impatrq/aeroalert/AES-CTRT-VDB_programs/pc-simulador/imagenes_GUI/llave2.png

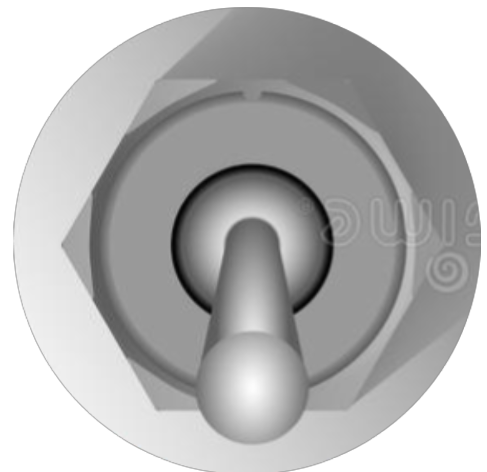
AES-CTRT-VDB_programs/pc-simulador/imagenes_GUI/llave2.png
