impatrq/aeroalert/AES-CTRT-VDB_programs/pc-simulador/imagenes_GUI/llave.png

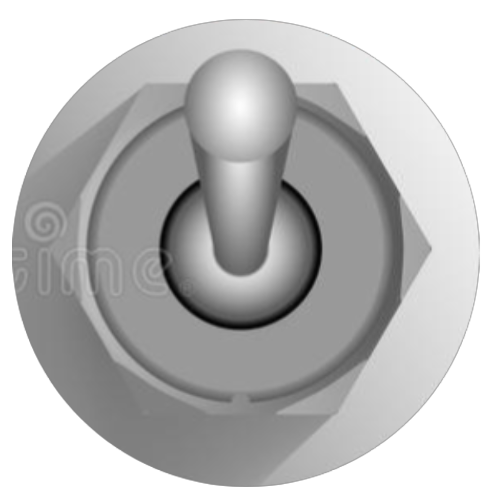
AES-CTRT-VDB_programs/pc-simulador/imagenes_GUI/llave.png
