impatrq/aeroalert/CAD/AES/AES - Exploded View.png

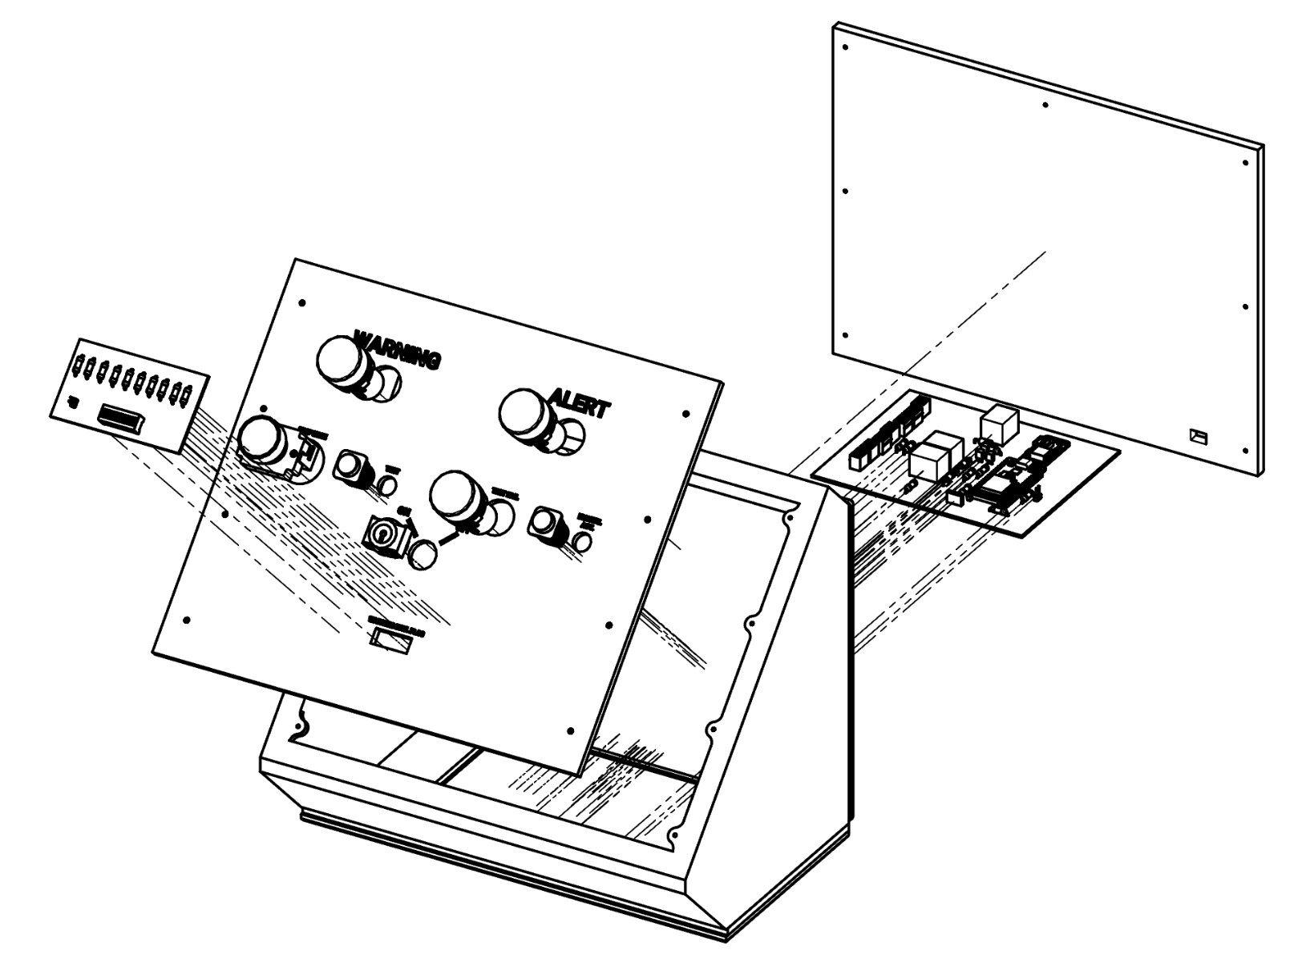
CAD/AES/AES - Exploded View.png
