impatrq/aeroalert/CAD/AES/Electrical/PCB/AES Blueprint.png

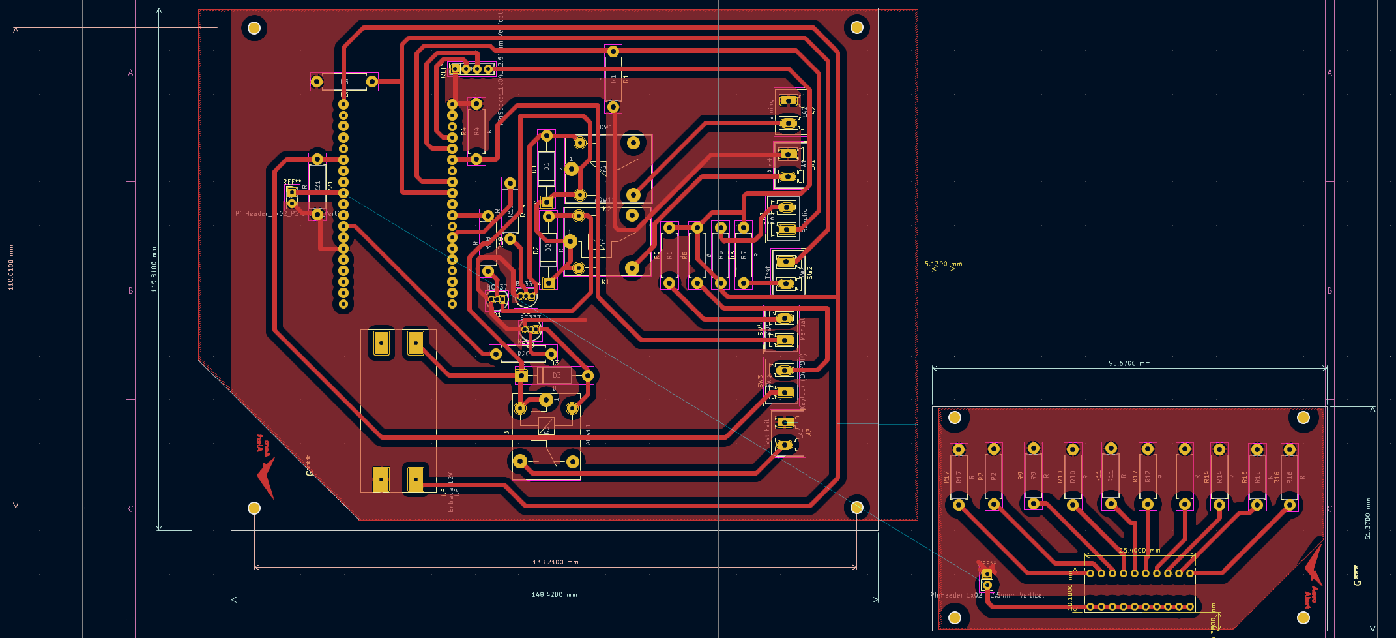
CAD/AES/Electrical/PCB/AES Blueprint.png
