impatrq/aeroalert/CAD/CTRT/CTRT - Exploded View.png

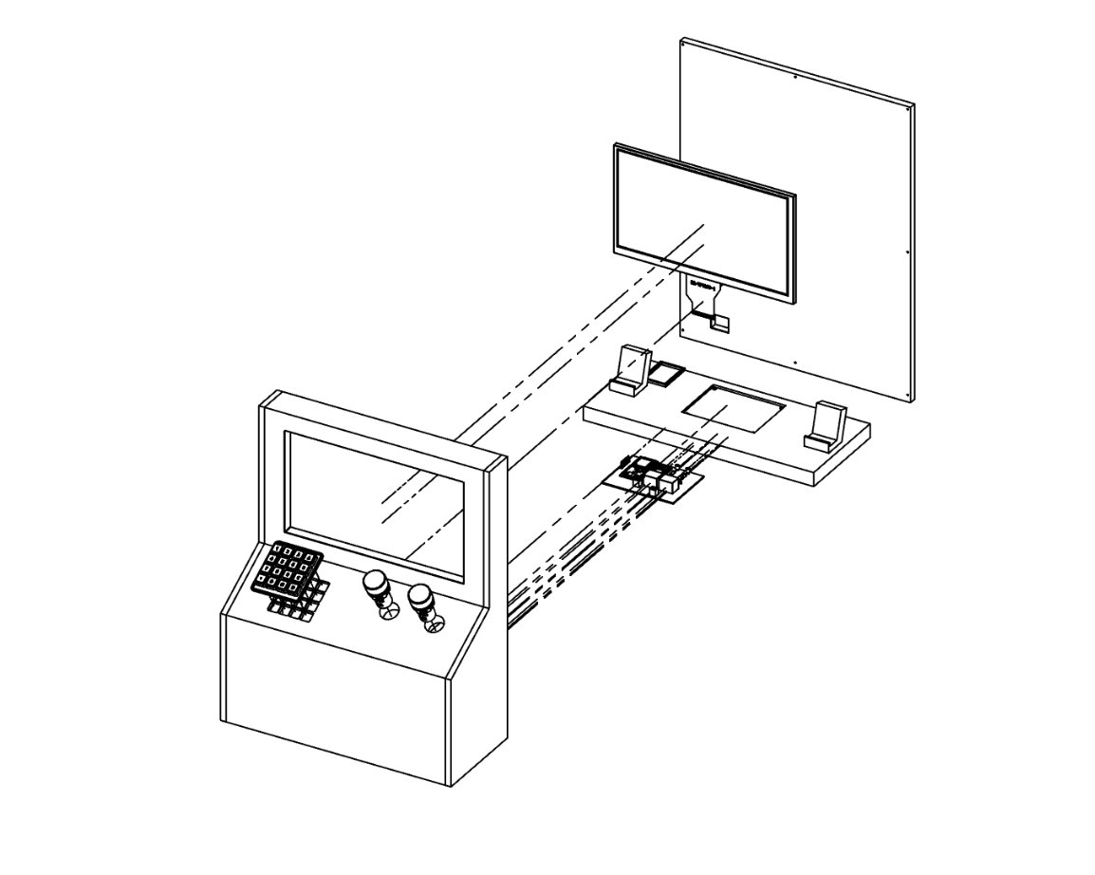
CAD/CTRT/CTRT - Exploded View.png
