impatrq/aeroalert/CAD/CTRT/Electrical/PCB/CTRT Blueprint.png

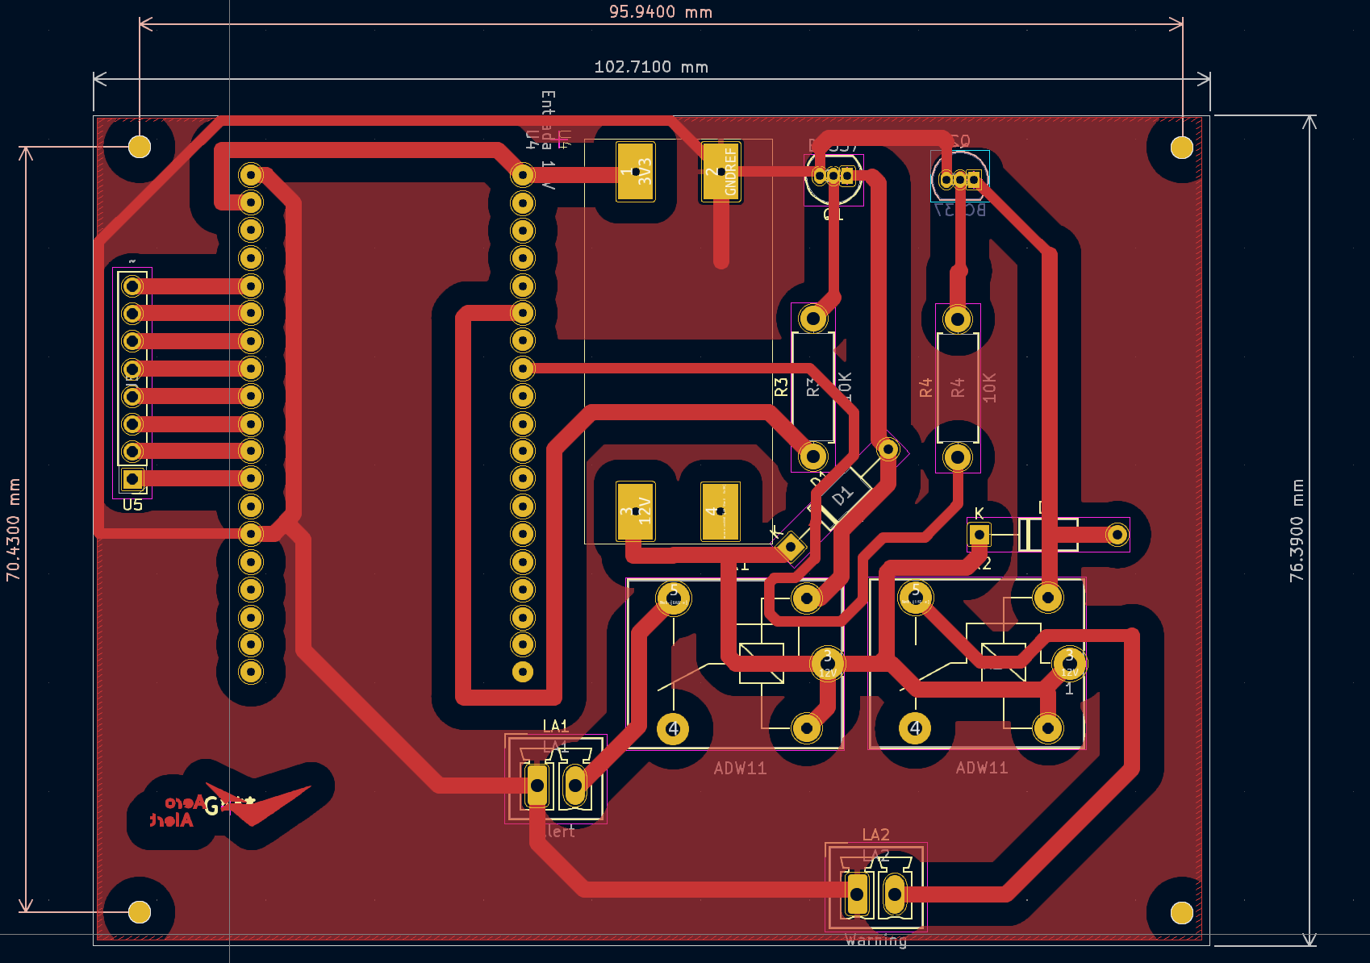
CAD/CTRT/Electrical/PCB/CTRT Blueprint.png
