impatrq/aeroalert/CAD/STEP Templates/Rendering/Pinout.jpg

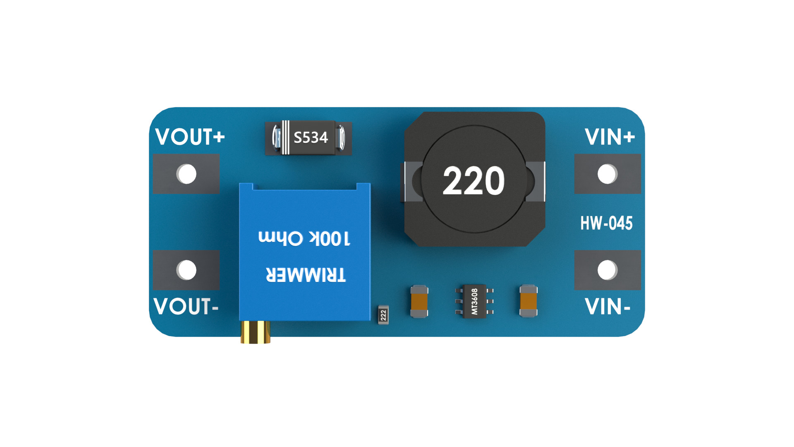
CAD/STEP Templates/Rendering/Pinout.jpg
