impatrq/aeroalert/CAD/VDB/Electrical/PCB/VDB Blueprint.png

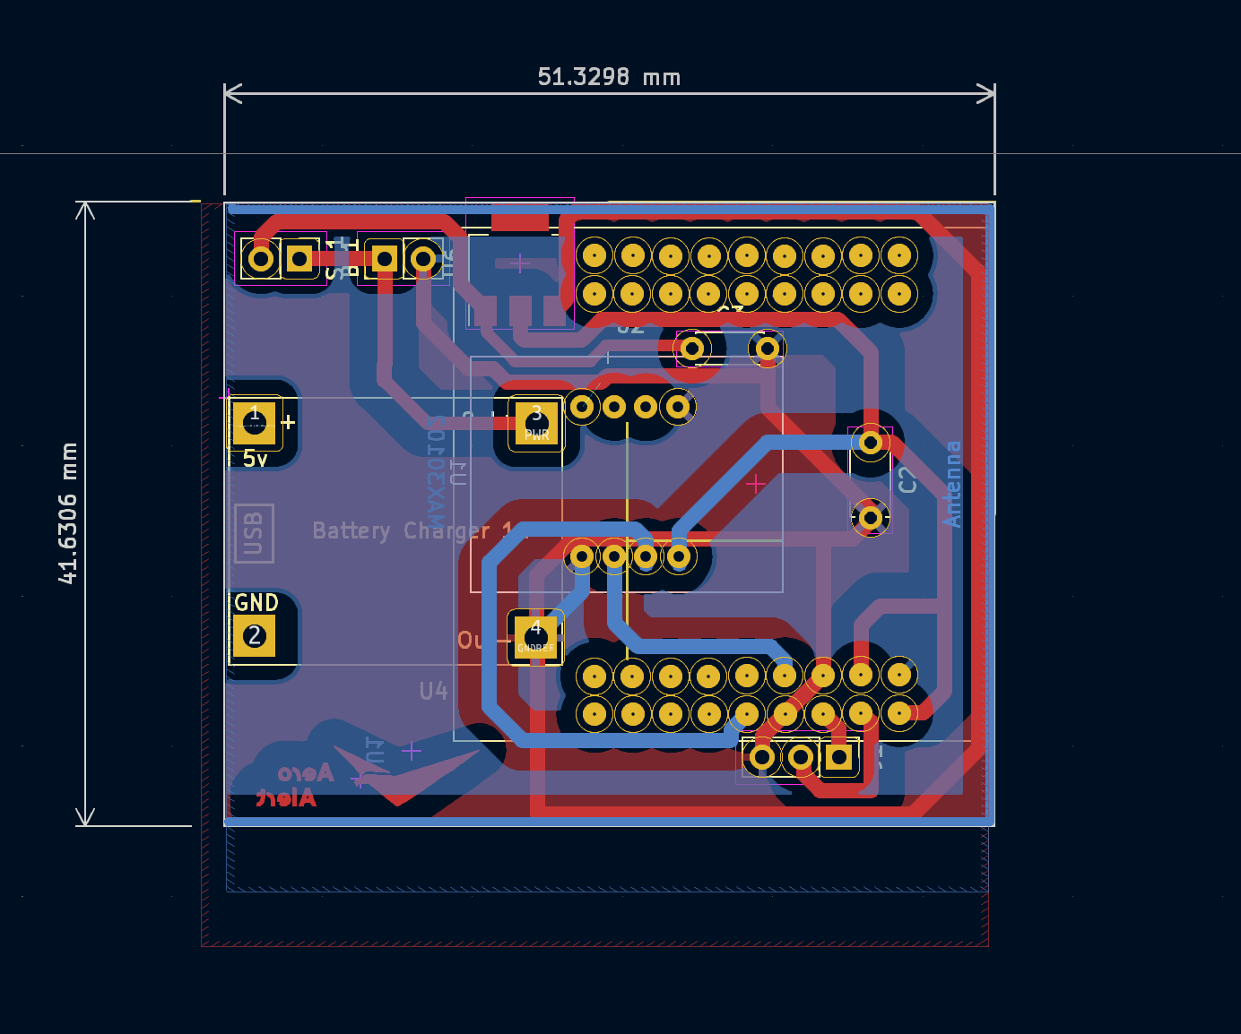
CAD/VDB/Electrical/PCB/VDB Blueprint.png
