impatrq/aeroalert/CAD/VDB/VDB - Exploded View.png

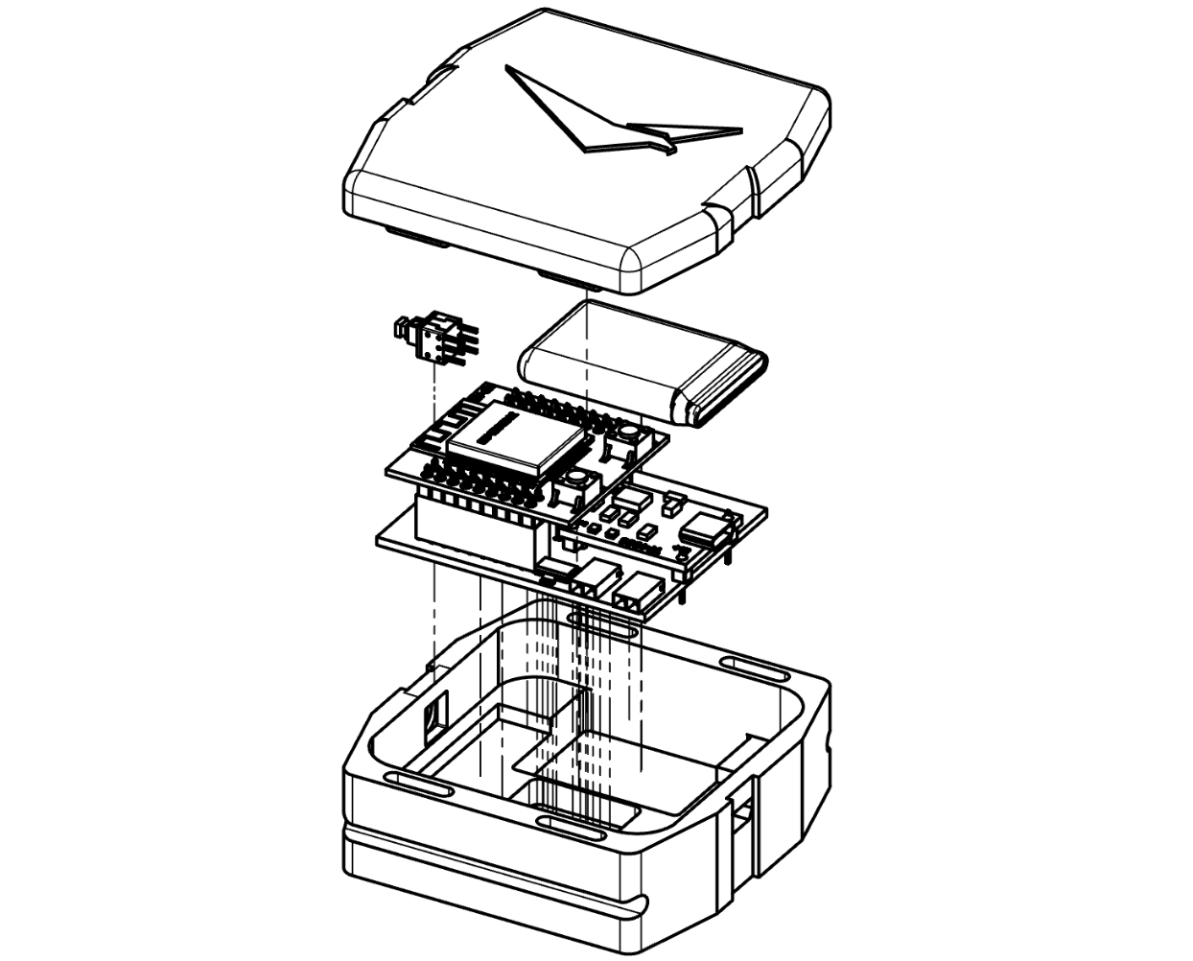
CAD/VDB/VDB - Exploded View.png
