impatrq/aeroalert/Diseños de marca/Destacadas/Nosotros AeroAlert.png

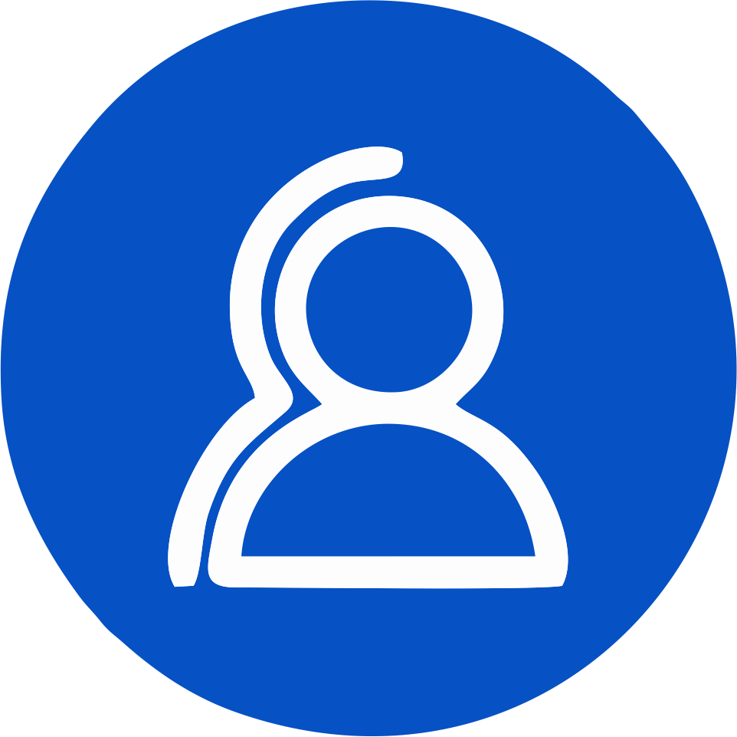
Diseños de marca/Destacadas/Nosotros AeroAlert.png
