impatrq/aeroalert/Diseños de marca/Destacadas/ONIET 2023.png

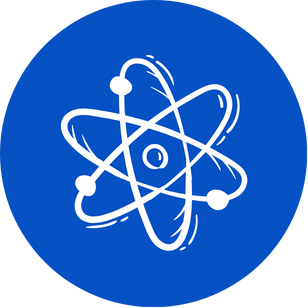
Diseños de marca/Destacadas/ONIET 2023.png
