impatrq/aeroalert/Diseños de marca/Destacadas/Progreso AeroAlert.png

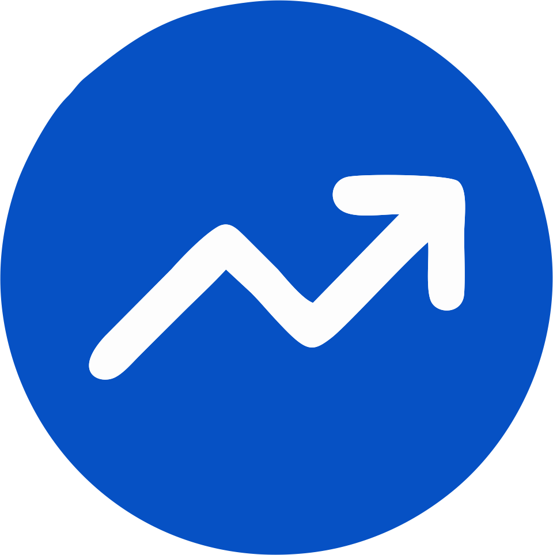
Diseños de marca/Destacadas/Progreso AeroAlert.png
