impatrq/aeroalert/Diseños de marca/Exposición/QR de Difusión.png

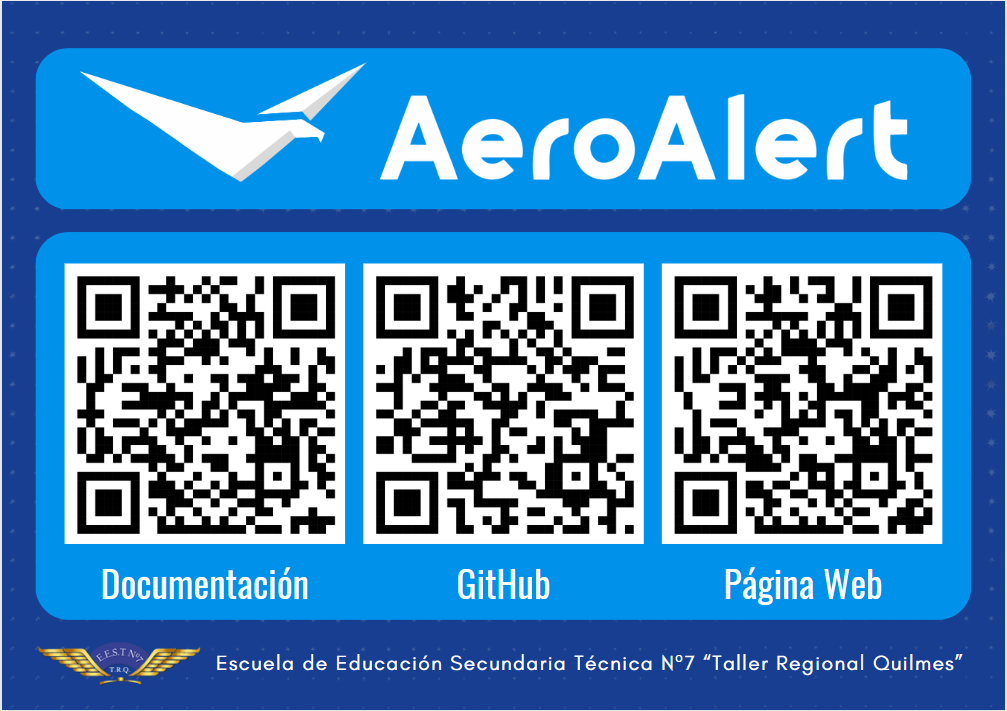
Diseños de marca/Exposición/QR de Difusión.png
