impatrq/aeroalert/Diseños de marca/Letras/Letras AeroAlert.png

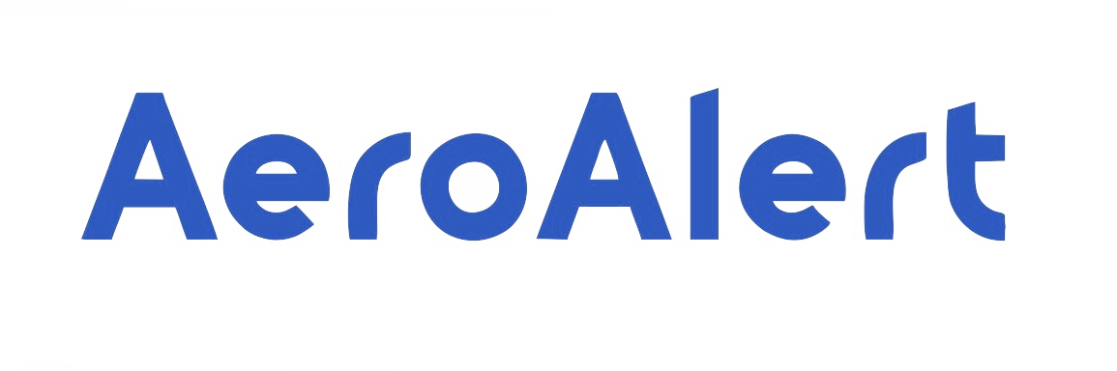
Diseños de marca/Letras/Letras AeroAlert.png
