impatrq/aeroalert/Diseños de marca/Recursos adicionales/inicio-avio.png

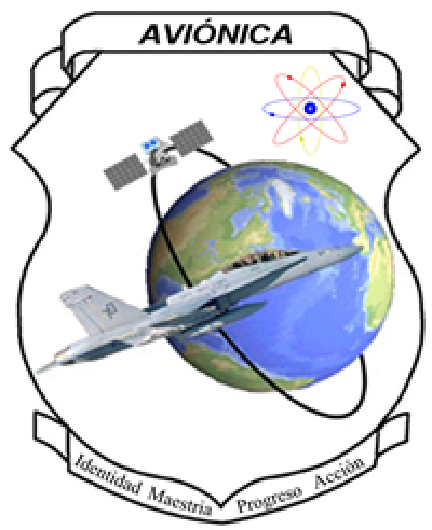
Diseños de marca/Recursos adicionales/inicio-avio.png
