impatrq/aeroalert/Pagina Web/CV Personales/CV Teo Lopez.jpeg

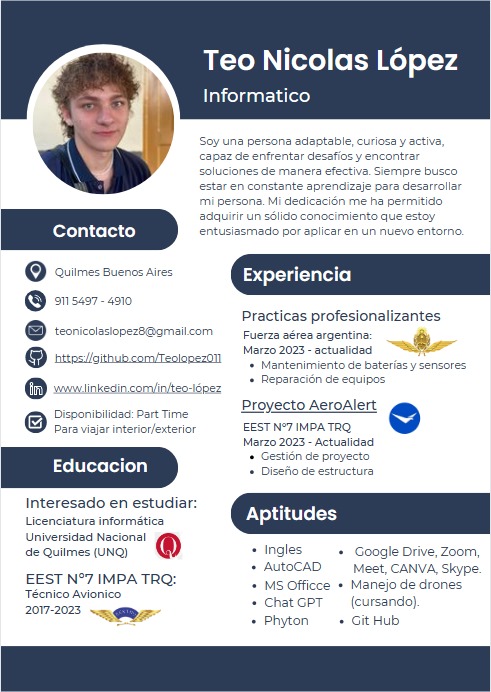
Pagina Web/CV Personales/CV Teo Lopez.jpeg
