impatrq/aeroalert/Pagina Web/imgs/Captura desde 2023-05-15 09-19-19.png

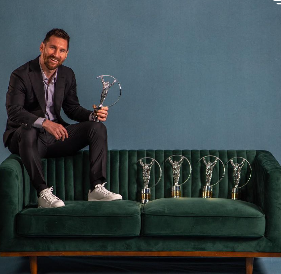
Pagina Web/imgs/Captura desde 2023-05-15 09-19-19.png
