impatrq/aeroalert/Pagina Web/imgs/Captura ESP32.png

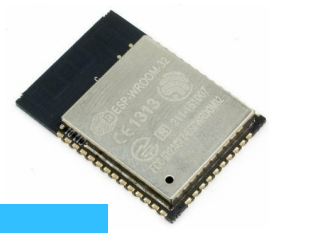
Pagina Web/imgs/Captura ESP32.png
