impatrq/aeroalert/Pagina Web/imgs/Captura Helios.png

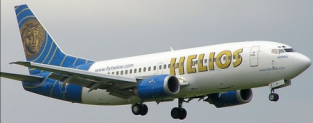
Pagina Web/imgs/Captura Helios.png
