impatrq/aeroalert/Pagina Web/imgs/Captura Pilotos zzzz.png

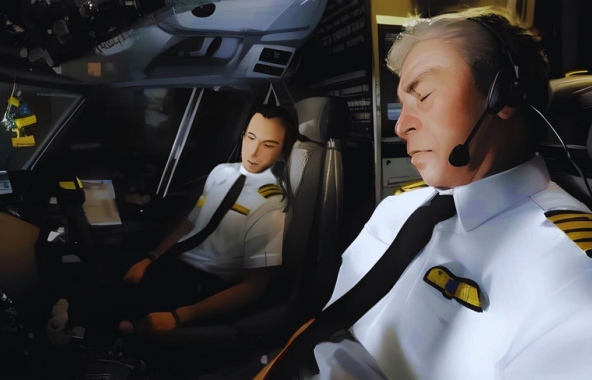
Pagina Web/imgs/Captura Pilotos zzzz.png
