impatrq/aeroalert/Pagina Web/imgs/Contacto.jpeg

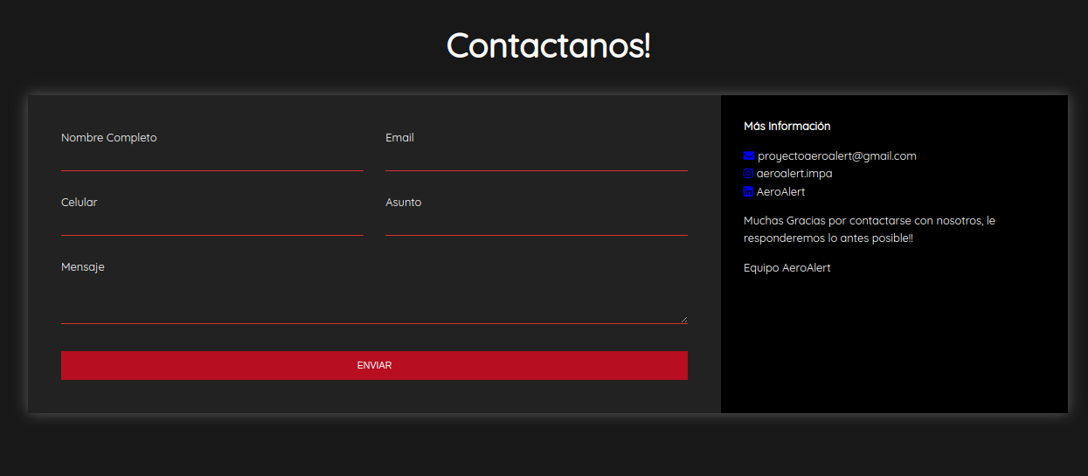
Pagina Web/imgs/Contacto.jpeg
