impatrq/aeroalert/Pagina Web/imgs/descarga.jpg

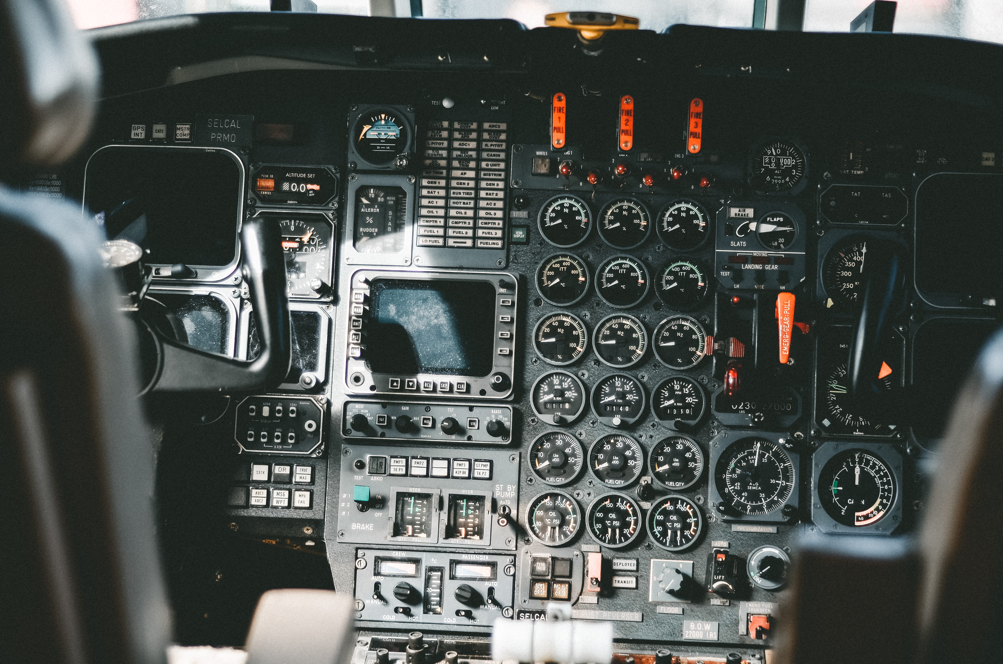
Pagina Web/imgs/descarga.jpg
