impatrq/aeroalert/Pagina Web/imgs/foto de los pibes.jpeg

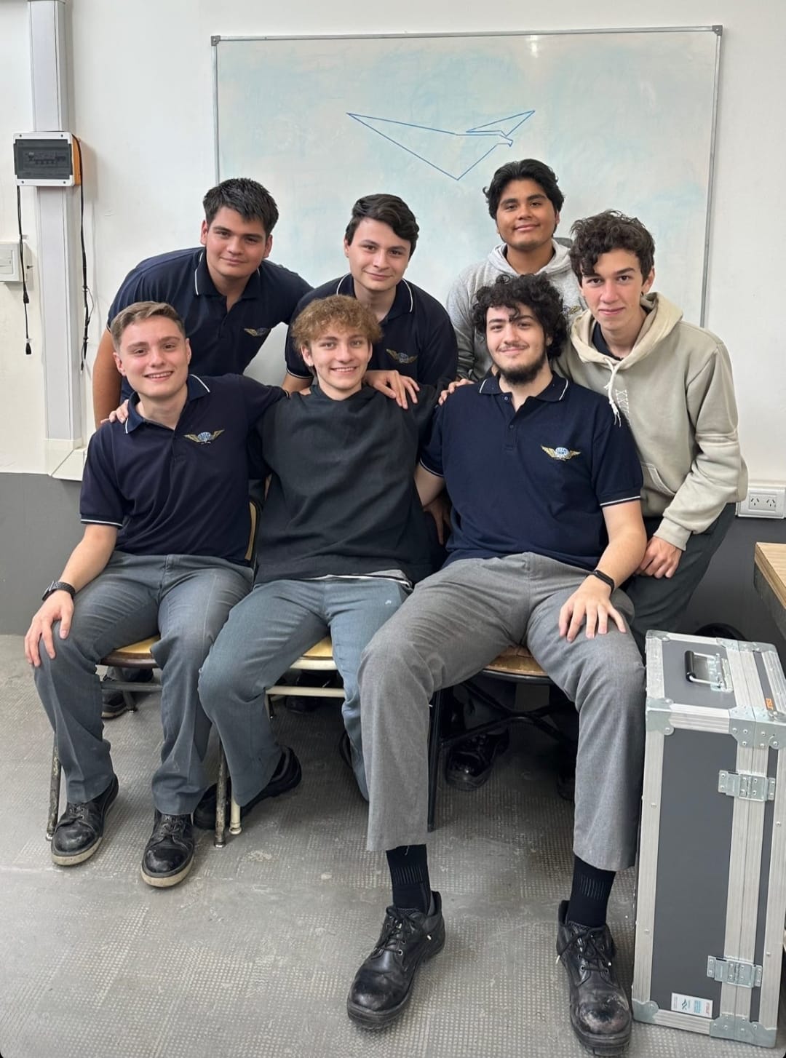
Pagina Web/imgs/foto de los pibes.jpeg
