impatrq/aeroalert/Pagina Web/imgs/husu 2 foto.jpeg

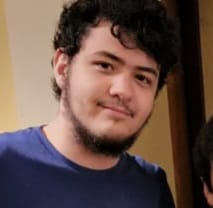
Pagina Web/imgs/husu 2 foto.jpeg
