impatrq/aeroalert/Pagina Web/imgs/Husu foto.jpeg

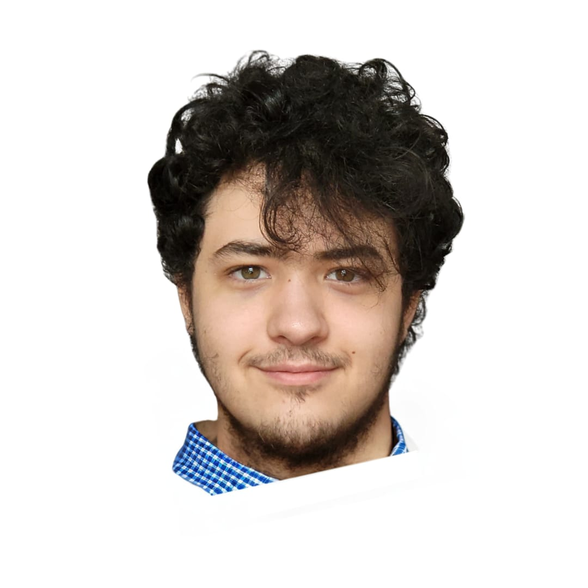
Pagina Web/imgs/Husu foto.jpeg
