impatrq/aeroalert/Pagina Web/imgs/Jonas foto.png

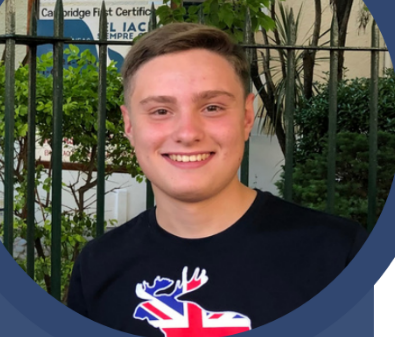
Pagina Web/imgs/Jonas foto.png
