impatrq/aeroalert/Pagina Web/imgs/juan foto.jpeg

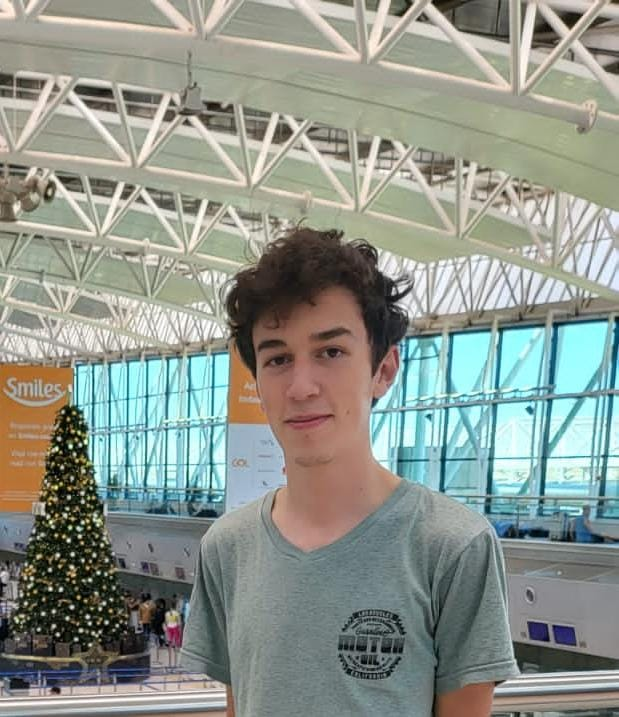
Pagina Web/imgs/juan foto.jpeg
