impatrq/aeroalert/Pagina Web/imgs/Mauro Foto 2.jpeg.png

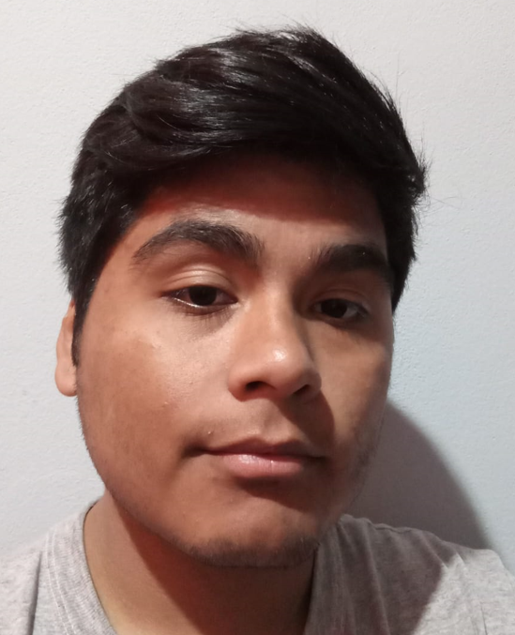
Pagina Web/imgs/Mauro Foto 2.jpeg.png
