impatrq/aeroalert/Pagina Web/imgs/Mauro Foto.jpeg

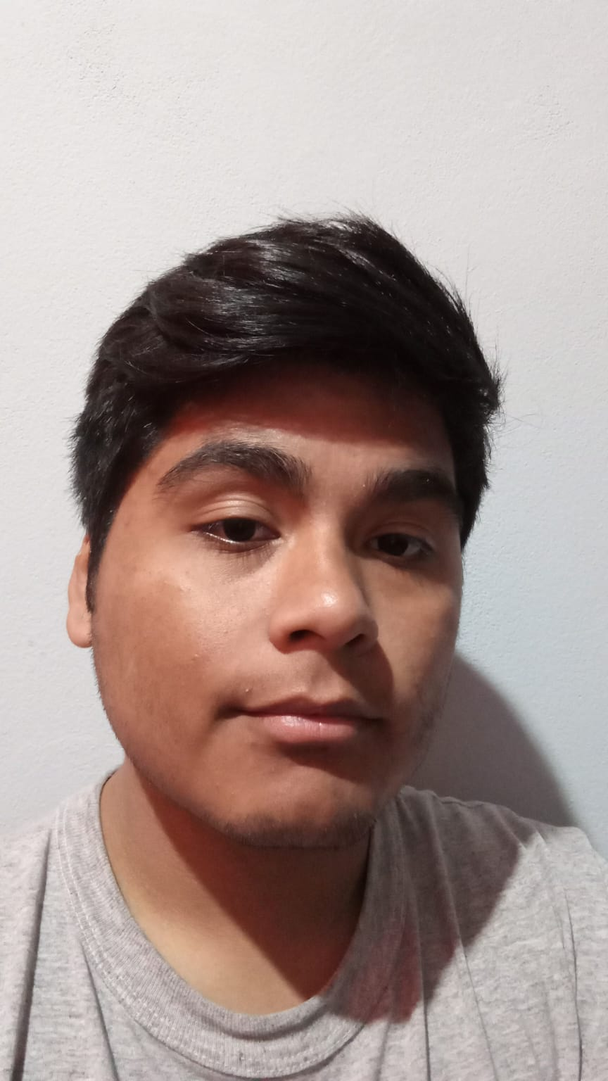
Pagina Web/imgs/Mauro Foto.jpeg
