impatrq/aeroalert/Pagina Web/imgs/Mi proyecto Azul.jpeg

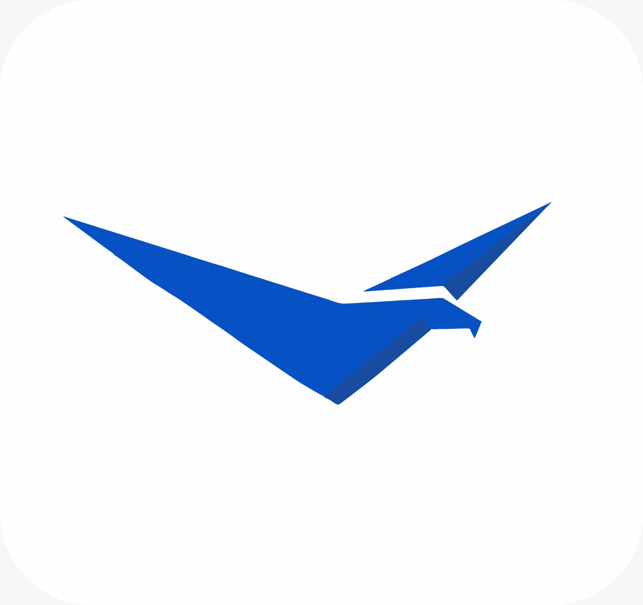
Pagina Web/imgs/Mi proyecto Azul.jpeg
