impatrq/aeroalert/Pagina Web/imgs/Mi proyecto.png

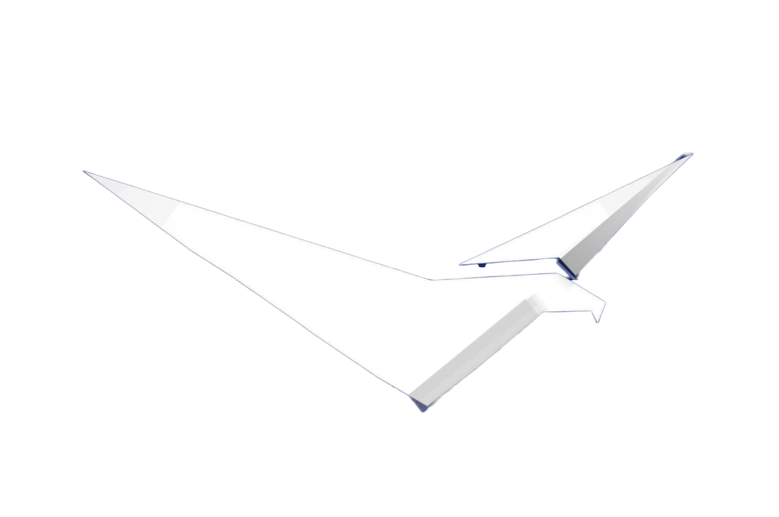
Pagina Web/imgs/Mi proyecto.png
