impatrq/aeroalert/Pagina Web/imgs/nicolas foto.jpeg

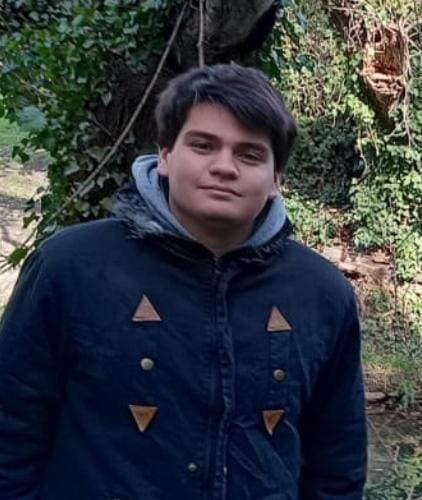
Pagina Web/imgs/nicolas foto.jpeg
