impatrq/aeroalert/Pagina Web/imgs/Programacion.jpg

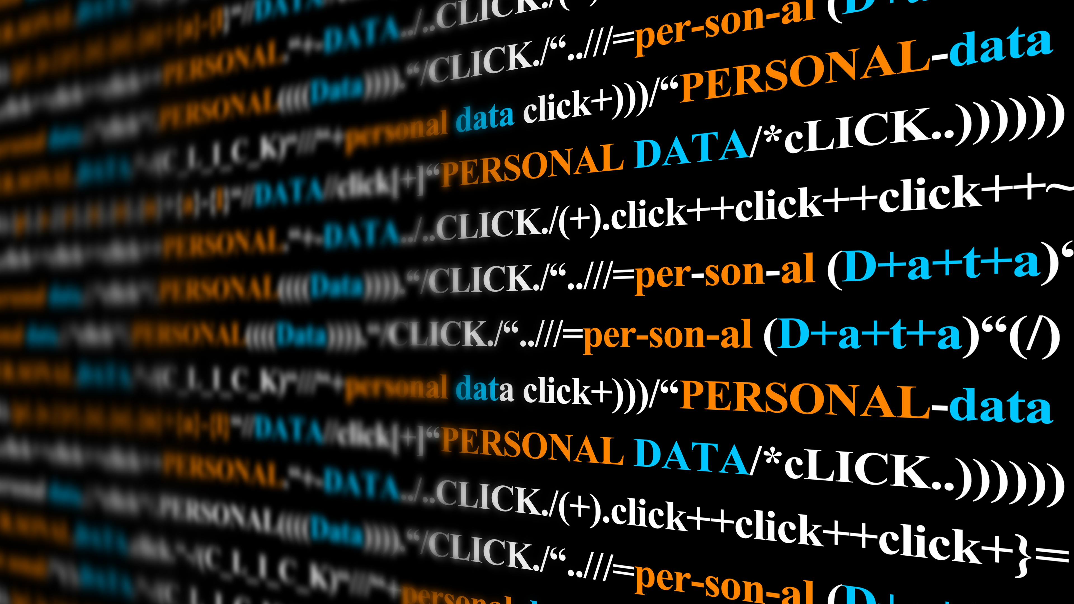
Pagina Web/imgs/Programacion.jpg
