impatrq/aeroalert/Pagina Web/imgs/Teo2.png

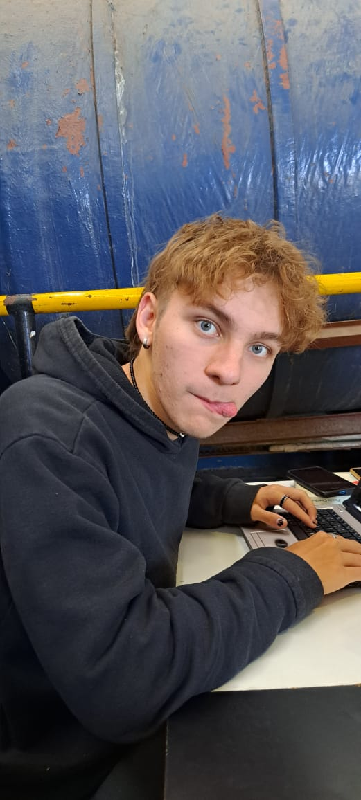
Pagina Web/imgs/Teo2.png
