impatrq/aeroalert/Pagina Web/imgs/Teo Lopez Foto.jpeg

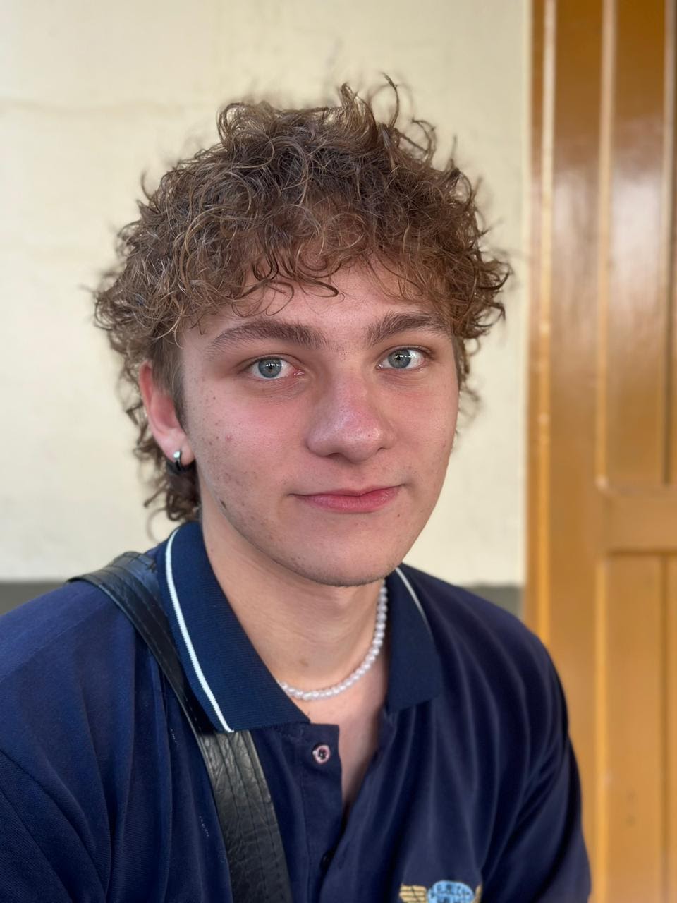
Pagina Web/imgs/Teo Lopez Foto.jpeg
