impatrq/aeroalert/Pagina Web/imgs/Teo.jpeg

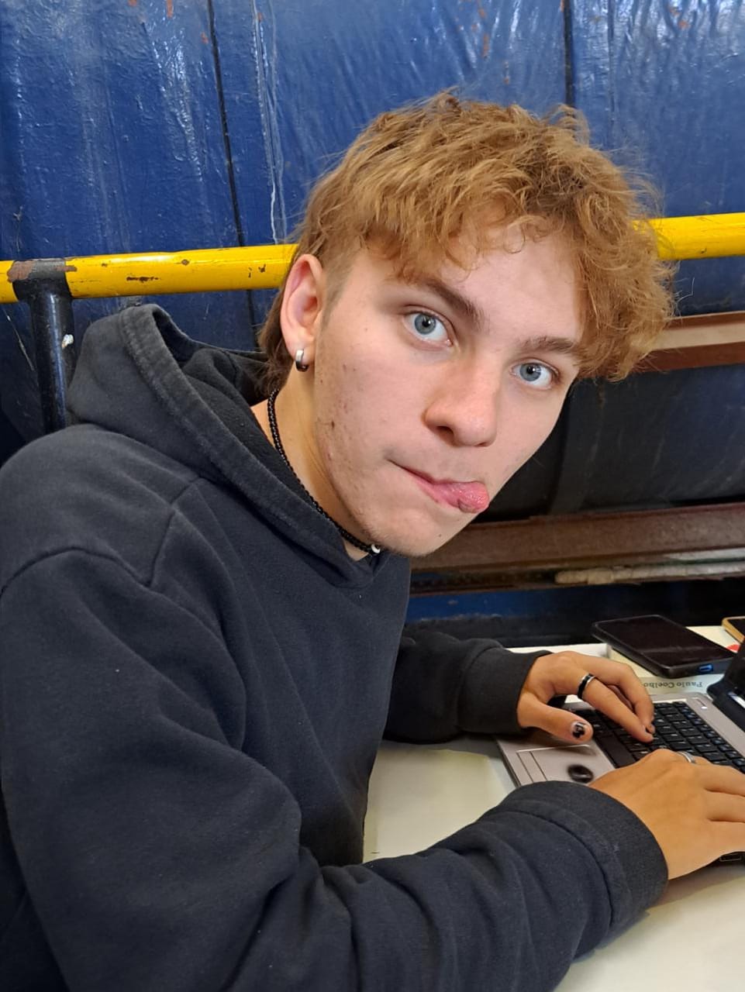
Pagina Web/imgs/Teo.jpeg
