impatrq/aeroalert/CAD/CNC Routing/CTRT/Part 3/Part Studio 1 - Part 3.dxf

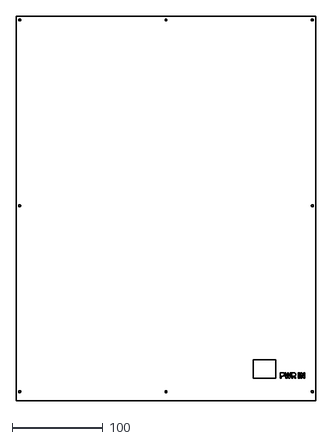
[picture p121: CAD file, 2023-11-29]
CAD/CNC Routing/CTRT/Part 3/Part Studio 1 - Part 3.dxf
330.0 x 423.0
