impatrq/aeroalert/CAD/CNC Routing/Plancha 120 x 80 cm.dxf

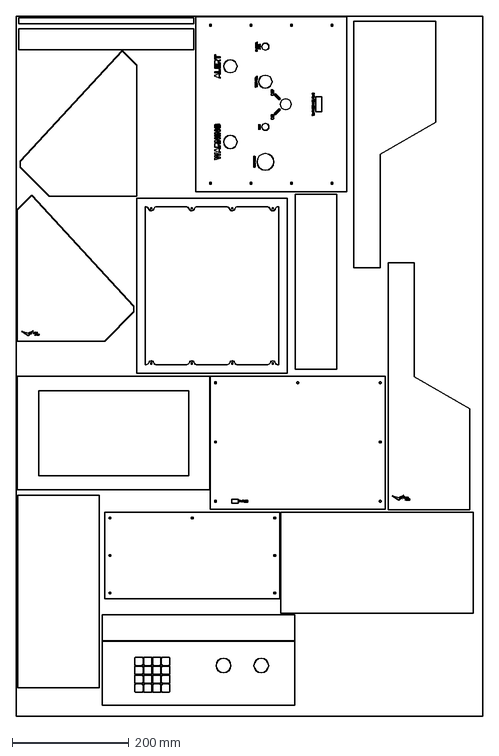
[picture p122: CAD file, 2023-11-29]
CAD/CNC Routing/Plancha 120 x 80 cm.dxf
800.0 x 1200.0 mm
