impatrq/aeroalert/CAD/CTRT/CTRT - Keycaps.stl

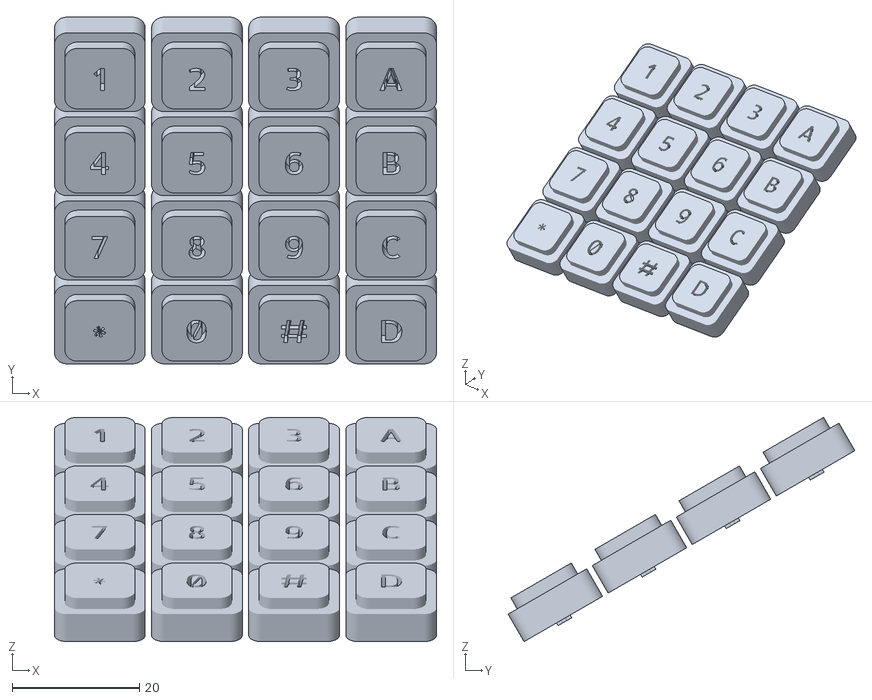
[picture p123: CAD file, 2023-11-15]
CAD/CTRT/CTRT - Keycaps.stl
60.1 x 54.6 x 35.3
