impatrq/aeroalert/CAD/STEP Templates/10-segment-linear-display-1/Display_10SegBlue.SLDPRT

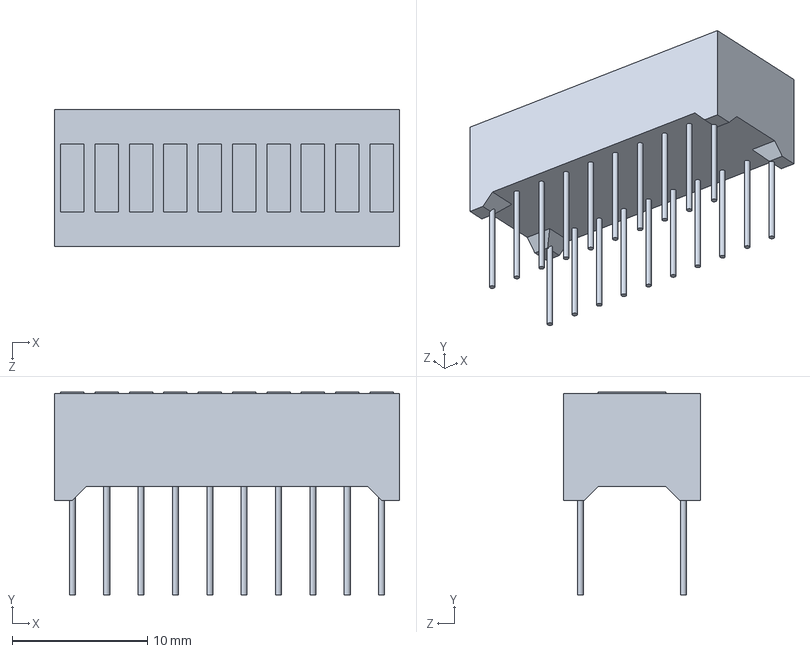
[picture p124: CAD file, 2023-11-28]
CAD/STEP Templates/10-segment-linear-display-1/Display_10SegBlue.SLDPRT
25.5 x 15.0 x 10.1 mm
