impatrq/aeroalert/CAD/STEP Templates/emergency-stop-12/PushButton27mm.STEP

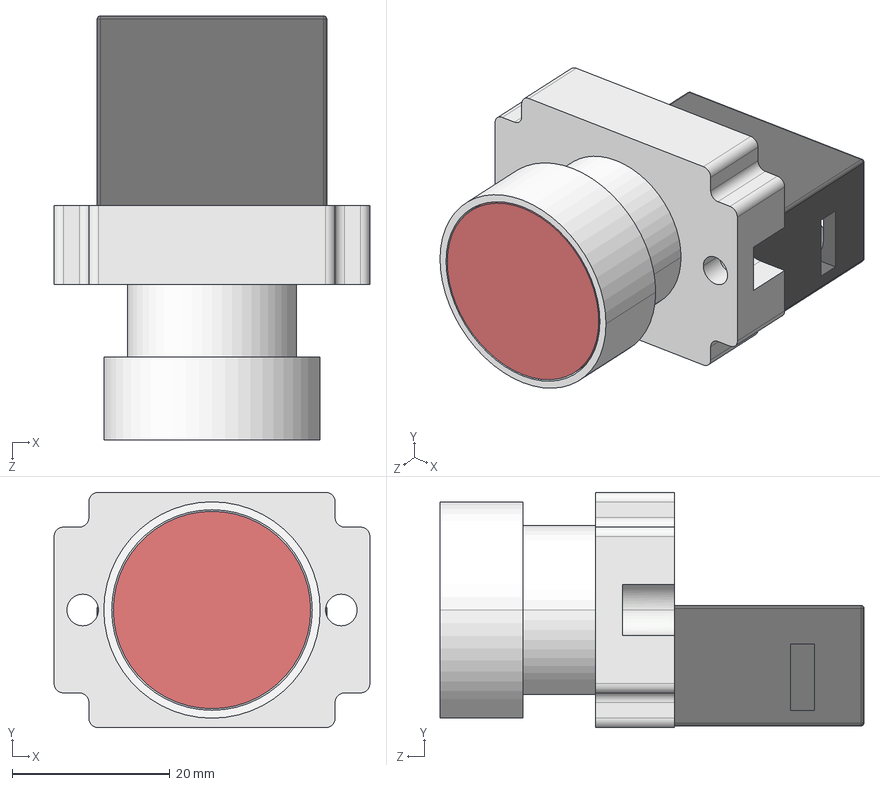
[picture p126: CAD file, 2023-11-28]
CAD/STEP Templates/emergency-stop-12/PushButton27mm.STEP
40.0 x 29.8 x 53.7 mm
