impatrq/aeroalert/CAD/STEP Templates/keyboard-4x4-1/TEC-MA-4X4.STEP

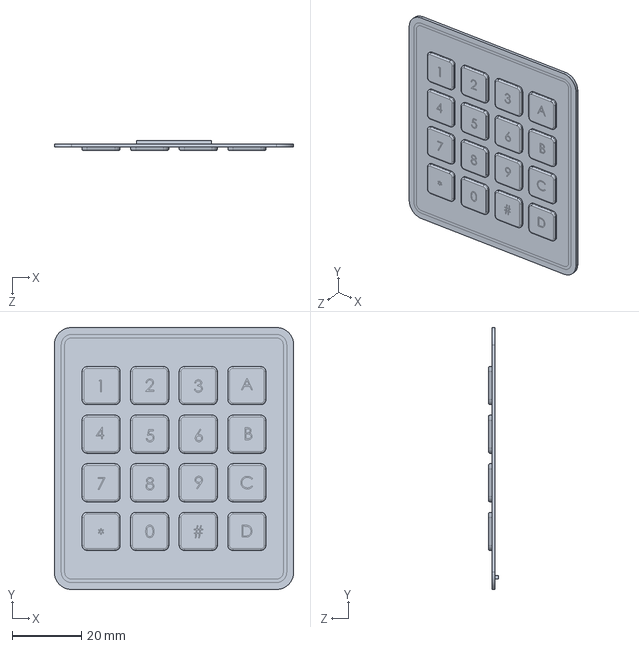
[picture p127: CAD file, 2023-11-28]
CAD/STEP Templates/keyboard-4x4-1/TEC-MA-4X4.STEP
69.0 x 75.5 x 3.00 mm
