impatrq/aeroalert/CAD/STEP Templates/keylock-switch-adp16k4-1/KeySwitch16_Part2.SLDPRT

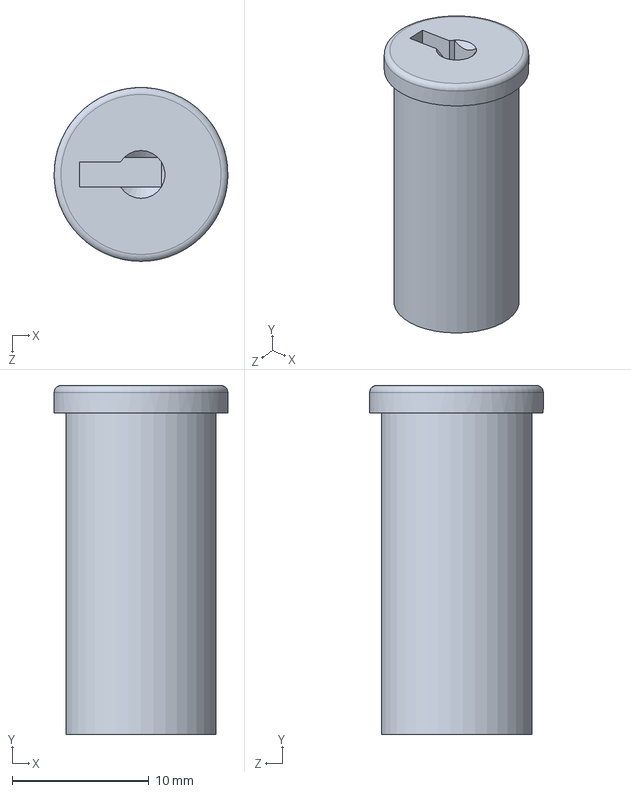
[picture p128: CAD file, 2023-11-28]
CAD/STEP Templates/keylock-switch-adp16k4-1/KeySwitch16_Part2.SLDPRT
12.7 x 25.5 x 12.7 mm
