impatrq/aeroalert/CAD/STEP Templates/led-pushbutton-1/LED Pushbutton.step

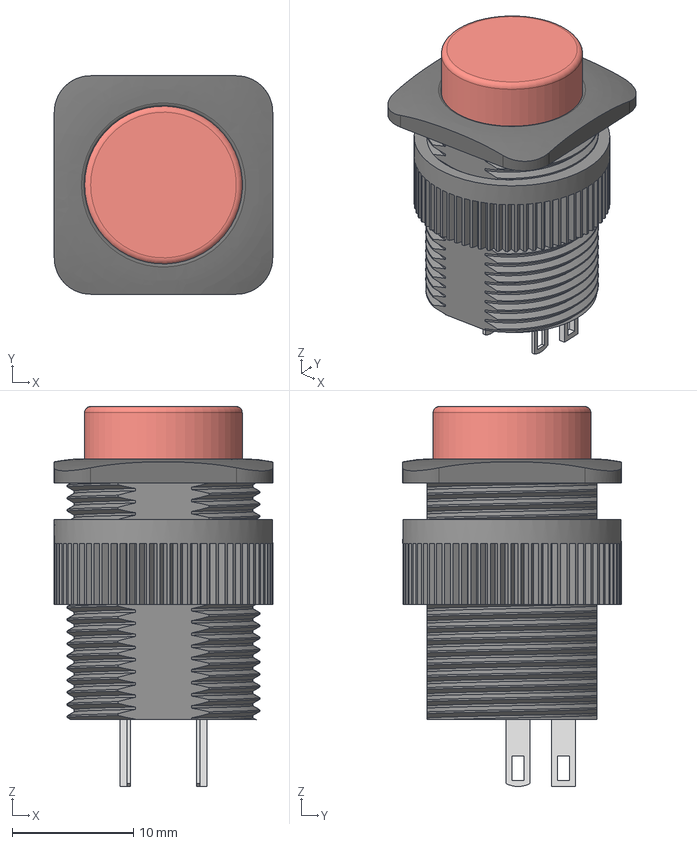
[picture p129: CAD file, 2023-11-28]
CAD/STEP Templates/led-pushbutton-1/LED Pushbutton.step
18.0 x 18.0 x 31.3 mm
Top
Bezel
Barrel
Lock Nut
Lug
Lug 2
Lug(Mirror)
Lug 2(Mirror)
