impatrq/aeroalert/CAD/STEP Templates/mini-toggle-switches-1/6mm DPDT Mini Toggle Switch.step

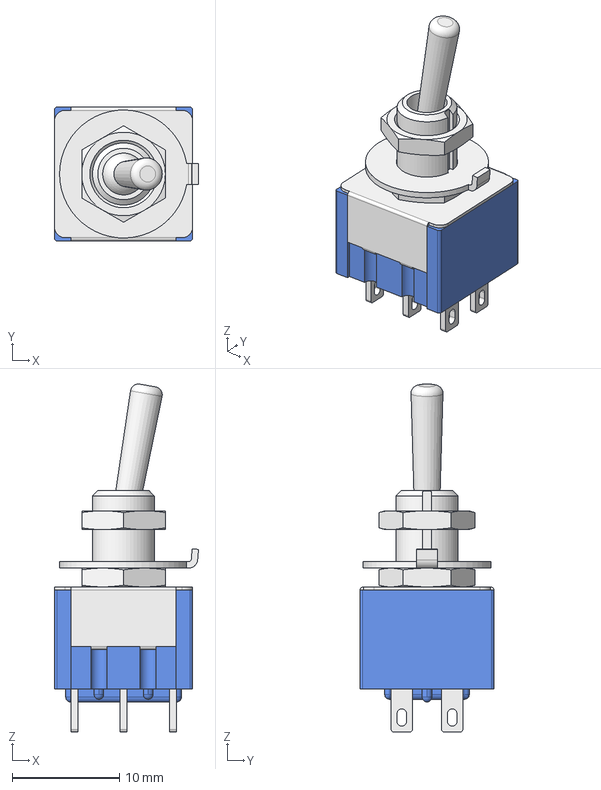
[picture p130: CAD file, 2023-11-28]
CAD/STEP Templates/mini-toggle-switches-1/6mm DPDT Mini Toggle Switch.step
13.4 x 12.5 x 32.5 mm
