impatrq/aeroalert/CAD/STEP Templates/mini-toggle-switches-1/FreeCAD Files/Set.FCStd

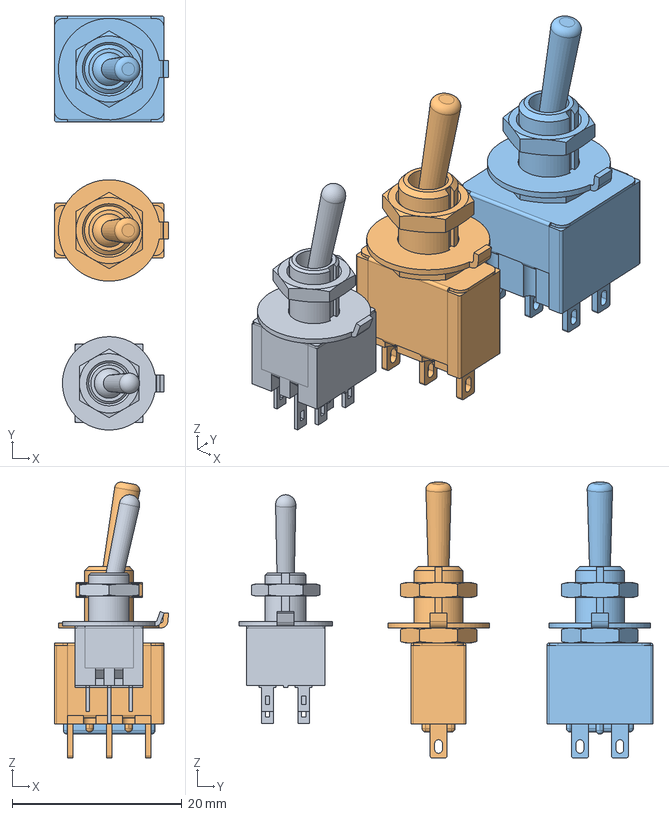
[picture p131: CAD file, 2023-11-28]
CAD/STEP Templates/mini-toggle-switches-1/FreeCAD Files/Set.FCStd
13.4 x 48.7 x 32.5 mm
5mm DPDT Mini Toggle Switch_001
6mm SPDT Mini Toggle Switch_001
6mm DPDT Mini Toggle Switch_001
