impatrq/aeroalert/CAD/STEP Templates/panel-light-indicator-_-red-1/PANEL LIGHT_RED.step

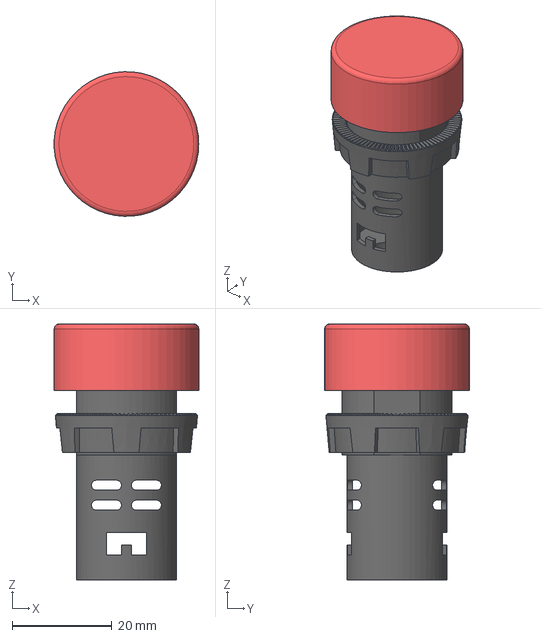
[picture p132: CAD file, 2023-11-28]
CAD/STEP Templates/panel-light-indicator-_-red-1/PANEL LIGHT_RED.step
29.0 x 29.0 x 51.3 mm
