impatrq/aeroalert/CAD/VDB/VDB - Top Cover.stl

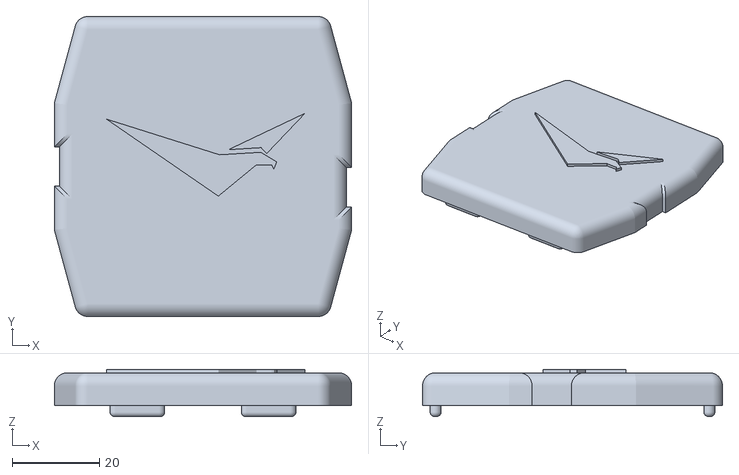
[picture p134: CAD file, 2023-11-15]
CAD/VDB/VDB - Top Cover.stl
68.0 x 68.6 x 10.8
