impatrq/aeroalert/CAD/CNC Routing/CTRT/Part 1/Part Studio 1 - Part 1-2.dxf

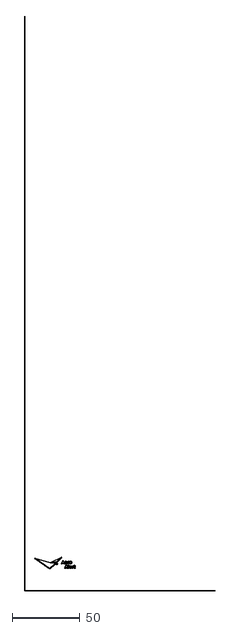
[picture p135: CAD file, 2023-11-29]
CAD/CNC Routing/CTRT/Part 1/Part Studio 1 - Part 1-2.dxf
140.0 x 423.0
