impatrq/aeroalert/CAD/STEP Templates/keylock-switch-adp16k4-1/Key Switch ADP16K4-ATO-1A.STEP

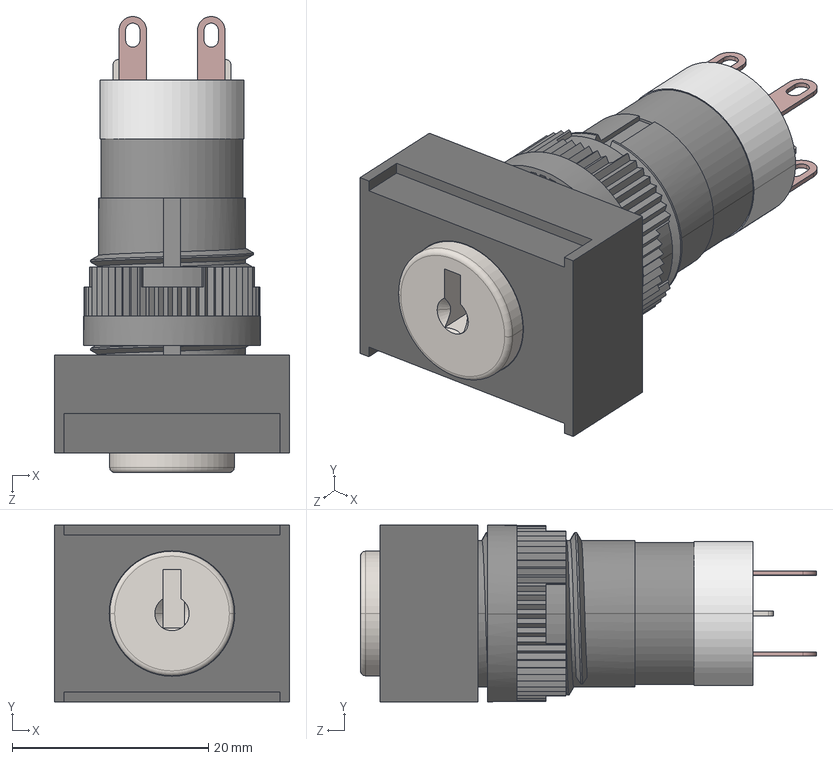
[picture p137: CAD file, 2023-11-28]
CAD/STEP Templates/keylock-switch-adp16k4-1/Key Switch ADP16K4-ATO-1A.STEP
24.0 x 18.0 x 46.5 mm
KeySwitch16_Part1
KeySwitch16_Part2
KeySwitch16_Part3
KeySwitch16_Part4
