impatrq/aeroalert/CAD/STEP Templates/LED bar.STEP

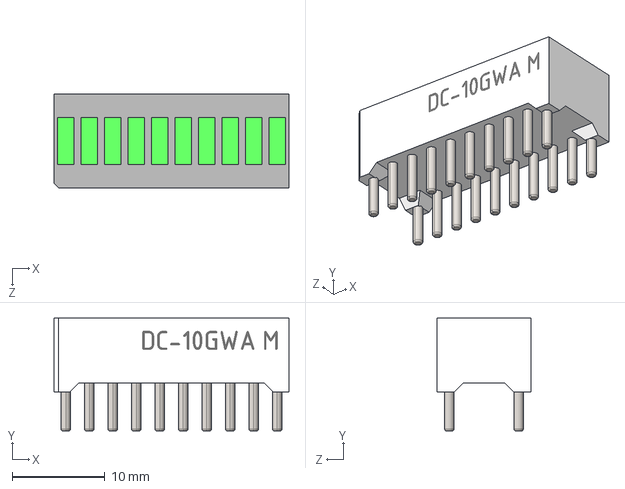
[picture p138: CAD file, 2023-11-28]
CAD/STEP Templates/LED bar.STEP
25.4 x 12.2 x 10.2 mm
