impatrq/aeroalert/CAD/STEP Templates/mini-toggle-switches-1/5mm DPDT Mini Toggle Switch.step

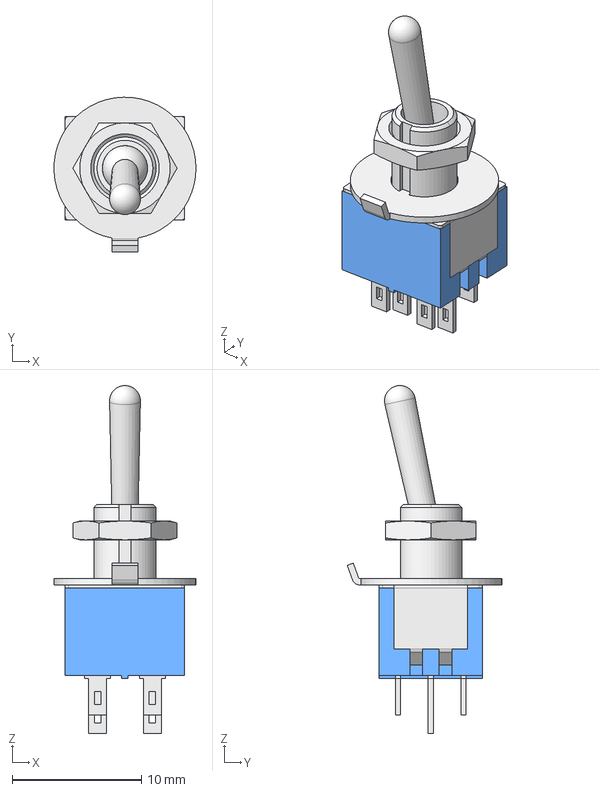
[picture p139: CAD file, 2023-11-28]
CAD/STEP Templates/mini-toggle-switches-1/5mm DPDT Mini Toggle Switch.step
11.0 x 12.0 x 26.9 mm
