impatrq/aeroalert/CAD/CNC Routing/CTRT/Part 1/Part Studio 1 - Part 1.dxf

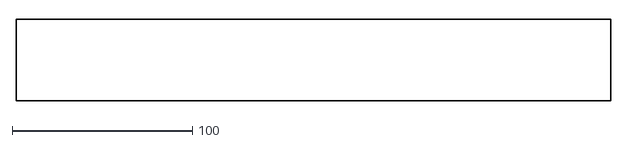
[picture p140: CAD file, 2023-11-29]
CAD/CNC Routing/CTRT/Part 1/Part Studio 1 - Part 1.dxf
330.0 x 45.0
