impatrq/aeroalert/CAD/STEP Templates/DS1040 (DIP-switch)/DS1040-04 (DIP_switch).stp

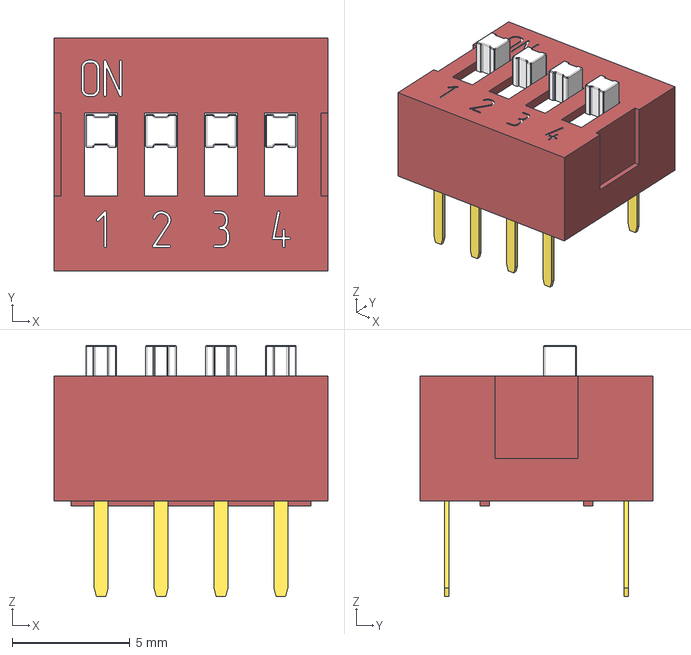
[picture p141: CAD file, 2023-11-28]
CAD/STEP Templates/DS1040 (DIP-switch)/DS1040-04 (DIP_switch).stp
11.6 x 9.90 x 10.7 mm
