impatrq/aeroalert/CAD/STEP Templates/keylock-switch-adp16k4-1/KeySwitch16_Part4.SLDPRT

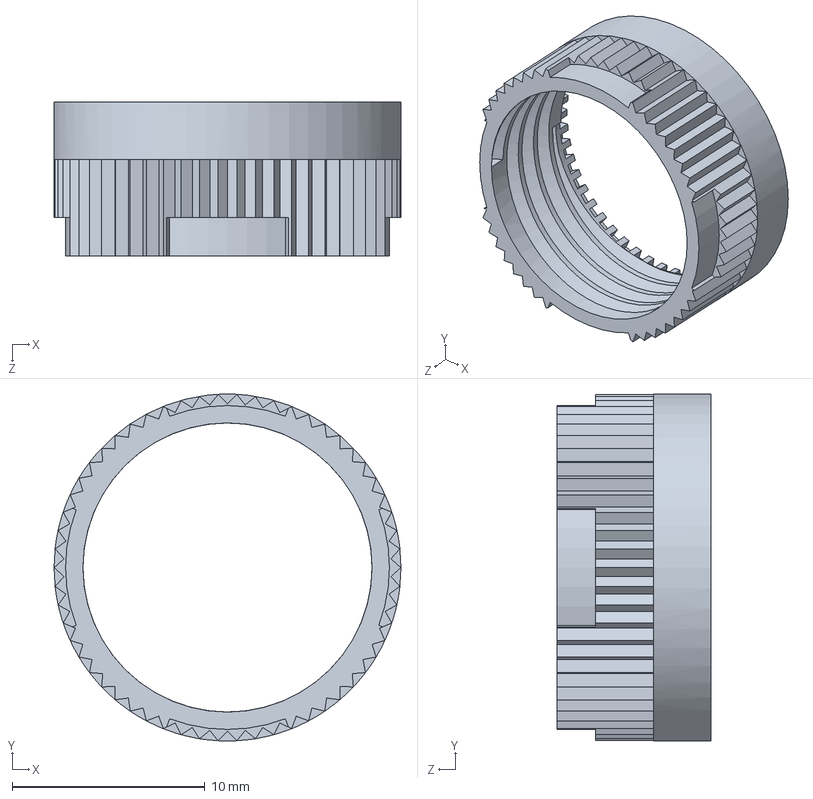
[picture p142: CAD file, 2023-11-28]
CAD/STEP Templates/keylock-switch-adp16k4-1/KeySwitch16_Part4.SLDPRT
18.0 x 18.0 x 8.00 mm
