impatrq/aeroalert/CAD/STEP Templates/mini-toggle-switches-1/6mm SPDT Mini Toggle Switch.step

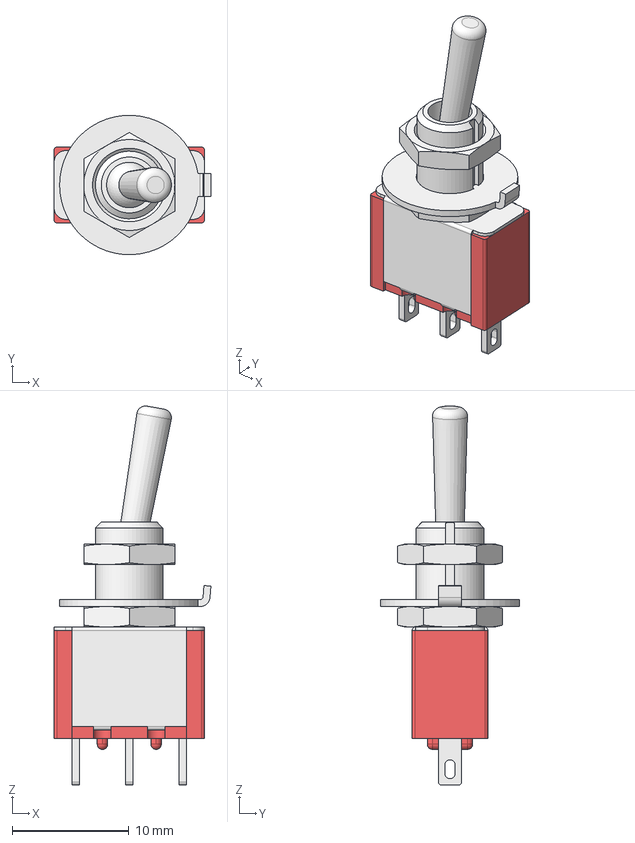
[picture p143: CAD file, 2023-11-28]
CAD/STEP Templates/mini-toggle-switches-1/6mm SPDT Mini Toggle Switch.step
13.4 x 11.9 x 32.5 mm
