impatrq/aeroalert/CAD/STEP Templates/PinHeader_3x06_P2.54mm_Horizontal.step

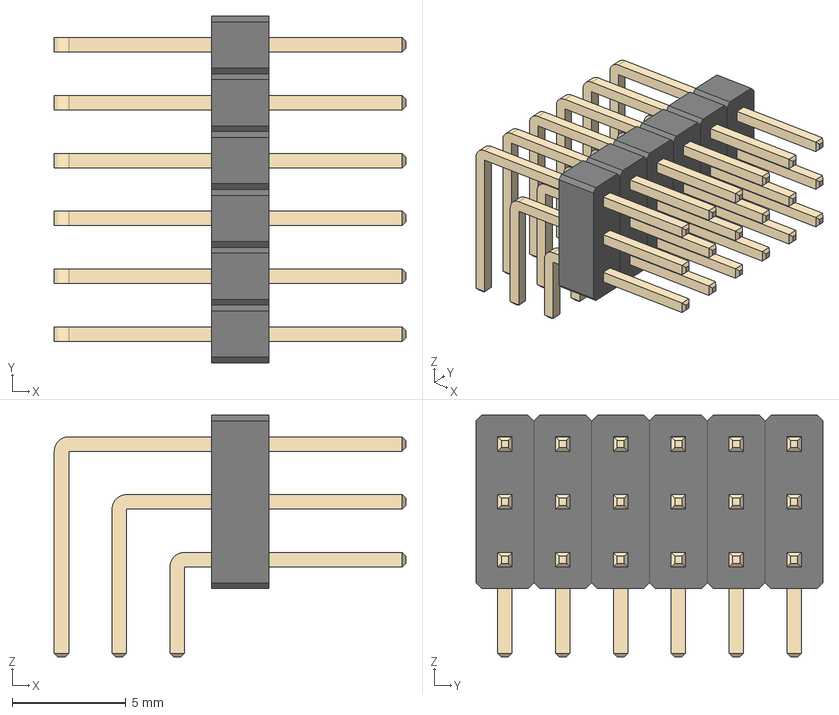
[picture p144: CAD file, 2023-11-28]
CAD/STEP Templates/PinHeader_3x06_P2.54mm_Horizontal.step
15.4 x 15.2 x 10.6 mm
