impatrq/aeroalert/CAD/CNC Routing/CTRT/Part 1/Part Studio 1 - Part 1-4.dxf

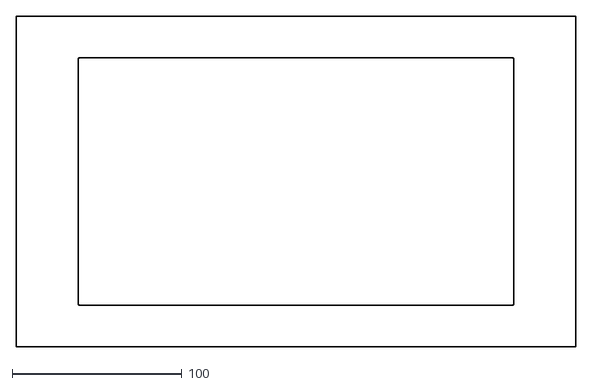
[picture p145: CAD file, 2023-11-29]
CAD/CNC Routing/CTRT/Part 1/Part Studio 1 - Part 1-4.dxf
330.0 x 195.2
