impatrq/aeroalert/CAD/STEP Templates/keylock-switch-adp16k4-1/KeySwitch16_Part1.SLDPRT

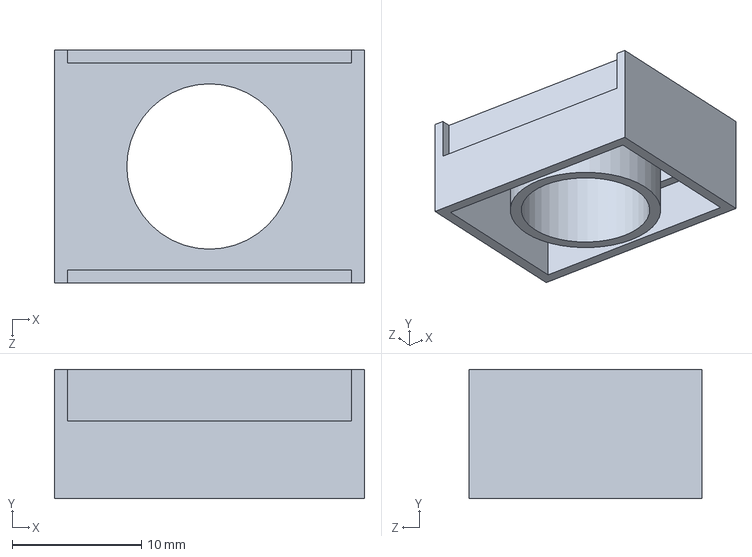
[picture p147: CAD file, 2023-11-28]
CAD/STEP Templates/keylock-switch-adp16k4-1/KeySwitch16_Part1.SLDPRT
24.0 x 10.0 x 18.0 mm
