impatrq/aeroalert/CAD/CNC Routing/CTRT/Part 1/Part Studio 1 - Part 1-7.dxf

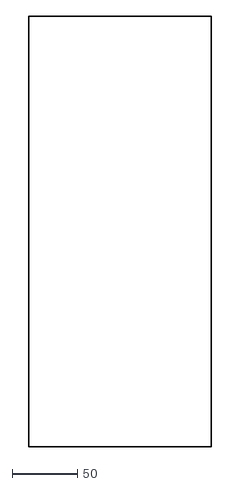
[picture p148: CAD file, 2023-11-29]
CAD/CNC Routing/CTRT/Part 1/Part Studio 1 - Part 1-7.dxf
140.0 x 330.0
