impatrq/aeroalert/CAD/STEP Templates/keylock-switch-adp16k4-1/KeySwitch16_Part3.SLDPRT

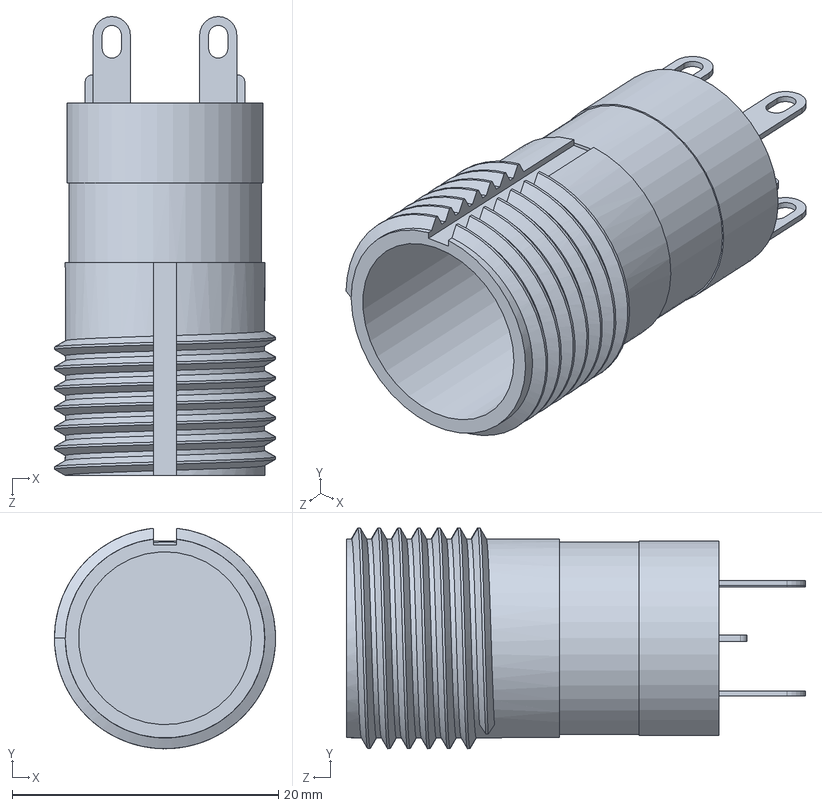
[picture p150: CAD file, 2023-11-28]
CAD/STEP Templates/keylock-switch-adp16k4-1/KeySwitch16_Part3.SLDPRT
16.6 x 16.6 x 34.5 mm
