impatrq/aeroalert/CAD/STEP Templates/PinHeader_3x40_P2.54mm_Horizontal.step

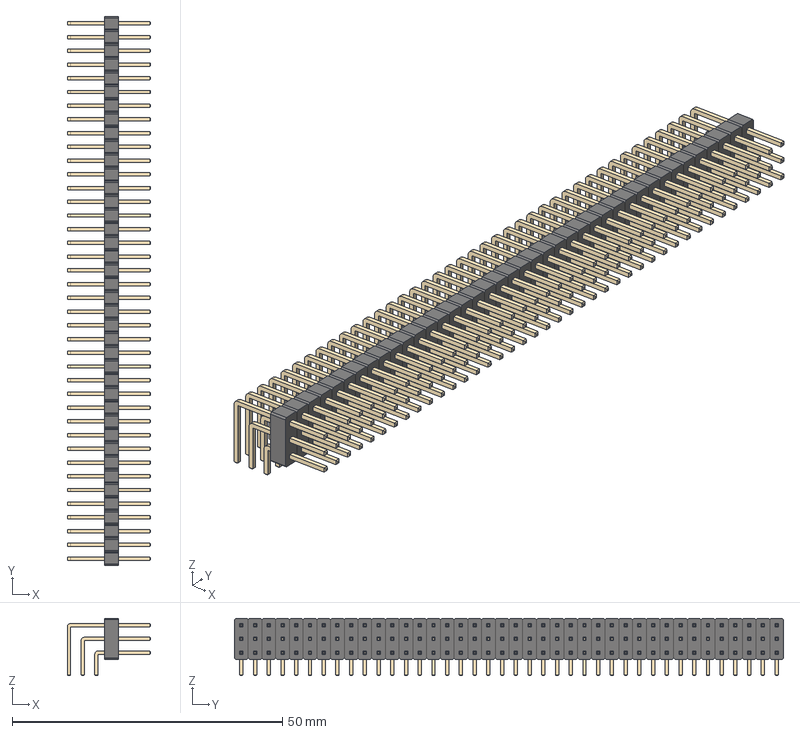
[picture p151: CAD file, 2023-11-28]
CAD/STEP Templates/PinHeader_3x40_P2.54mm_Horizontal.step
15.4 x 101.6 x 10.6 mm
Body_01 - 3x01_P2.54_Horizontal
Pin_02 - 3x01_P2.54_Horizontal
Pin_03 - 3x01_P2.54_Horizontal
Pin_01 - 3x01_P2.54_Horizontal
