impatrq/aeroalert/CAD/CNC Routing/CTRT/Part 1/Part Studio 1 - Part 1-5.dxf

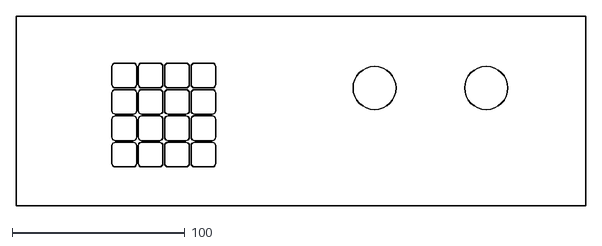
[picture p152: CAD file, 2023-11-29]
CAD/CNC Routing/CTRT/Part 1/Part Studio 1 - Part 1-5.dxf
330.0 x 109.7
