impatrq/aeroalert/CAD/STEP Templates/13-Pin Header - Female - 2.54mm.step

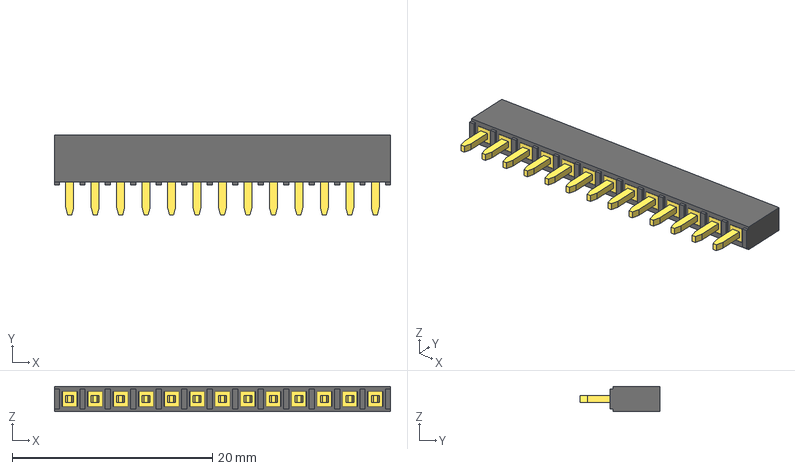
[picture p153: CAD file, 2023-11-28]
CAD/STEP Templates/13-Pin Header - Female - 2.54mm.step
33.5 x 8.00 x 2.50 mm
