impatrq/aeroalert/CAD/STEP Templates/DS1040 (DIP-switch)/DS1040-09 (DIP_switch).stp

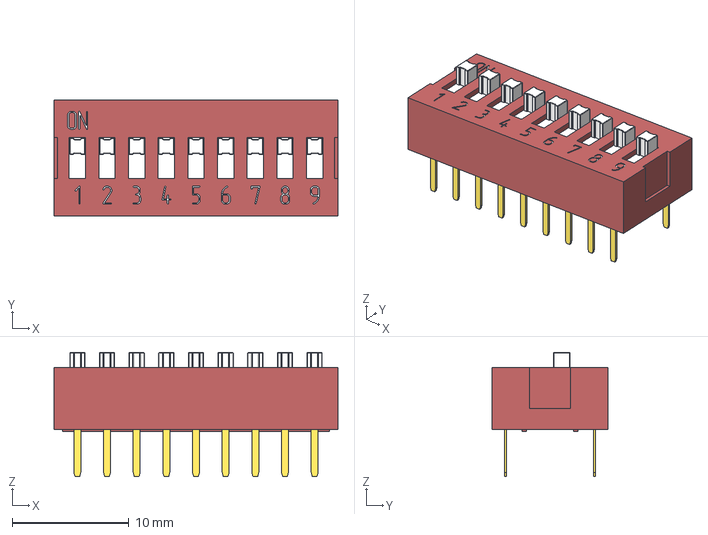
[picture p154: CAD file, 2023-11-28]
CAD/STEP Templates/DS1040 (DIP-switch)/DS1040-09 (DIP_switch).stp
24.3 x 9.90 x 10.7 mm
