impatrq/aeroalert/CAD/STEP Templates/H254_90deg_2pin.STEP

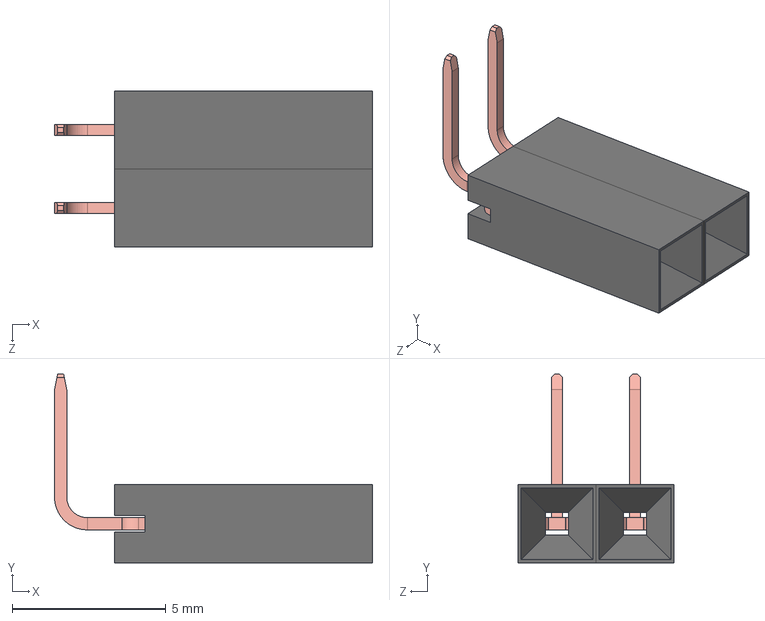
[picture p157: CAD file, 2023-11-28]
CAD/STEP Templates/H254_90deg_2pin.STEP
10.4 x 6.14 x 5.08 mm
frame_H254 x 2
pin-90deg x 2
