impatrq/aeroalert/CAD/STEP Templates/DS1040 (DIP-switch)/DS1040-10 (DIP_switch).stp

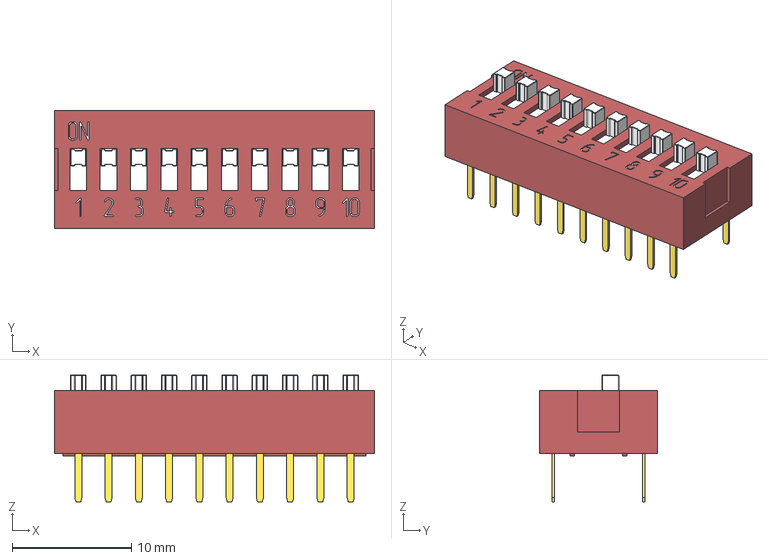
[picture p159: CAD file, 2023-11-28]
CAD/STEP Templates/DS1040 (DIP-switch)/DS1040-10 (DIP_switch).stp
26.9 x 9.90 x 10.7 mm
