impatrq/aeroalert/CAD/STEP Templates/TP4056 - No Pins.step

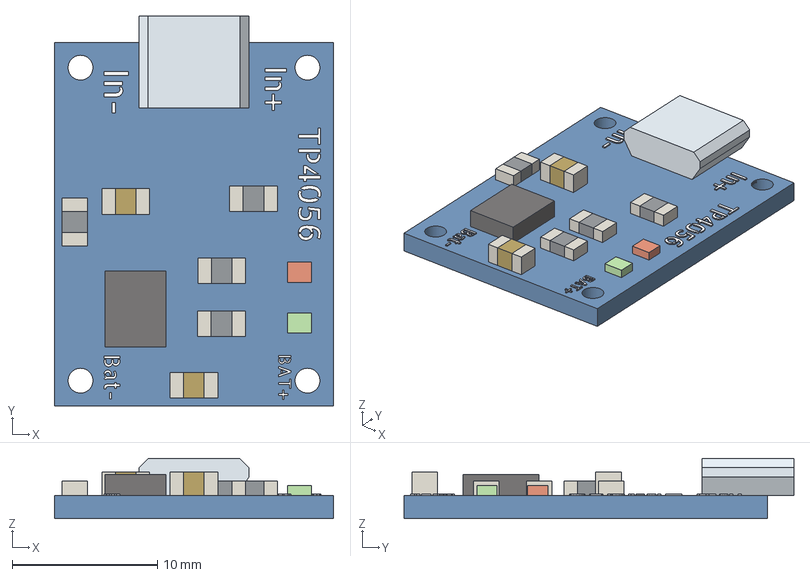
[picture p161: CAD file, 2023-11-28]
CAD/STEP Templates/TP4056 - No Pins.step
19.2 x 26.8 x 4.13 mm
