impatrq/aeroalert/CAD/STEP Templates/DS1040 (DIP-switch)/DS1040-07 (DIP_switch).stp

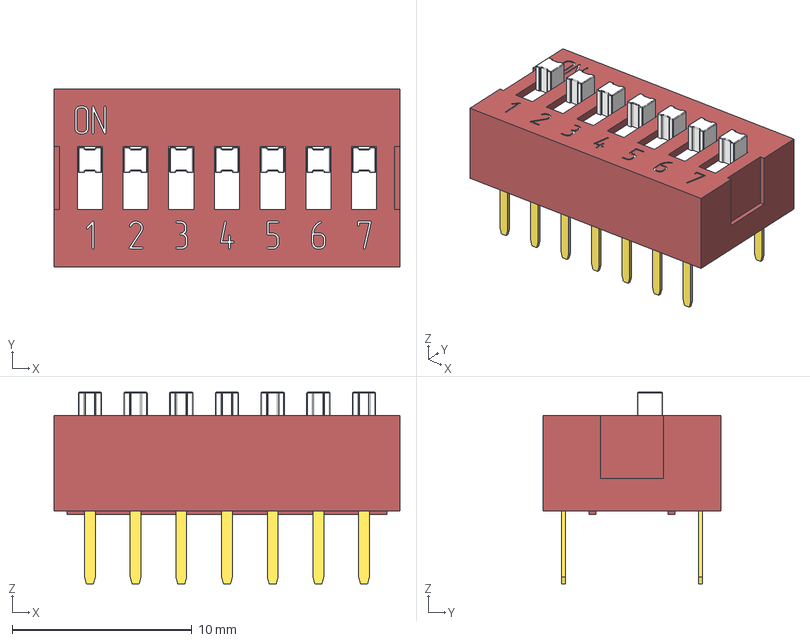
[picture p162: CAD file, 2023-11-28]
CAD/STEP Templates/DS1040 (DIP-switch)/DS1040-07 (DIP_switch).stp
19.2 x 9.90 x 10.7 mm
