impatrq/aeroalert/CAD/STEP Templates/PinHeader_3x28_P2.54mm_Horizontal.step

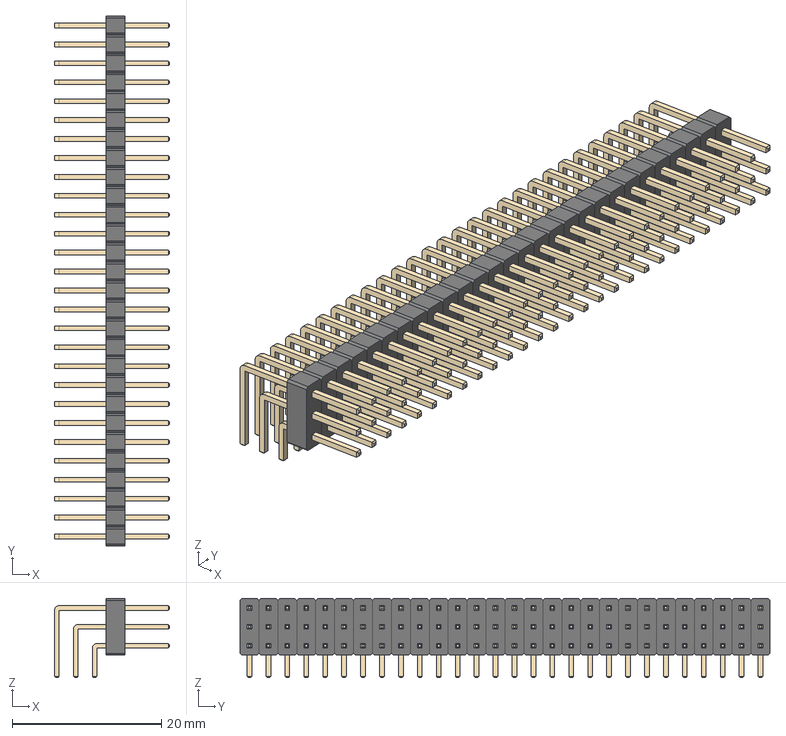
[picture p165: CAD file, 2023-11-28]
CAD/STEP Templates/PinHeader_3x28_P2.54mm_Horizontal.step
15.4 x 71.1 x 10.6 mm
