impatrq/aeroalert/CAD/STEP Templates/4-Pin Header - Male - 2.54mm.step

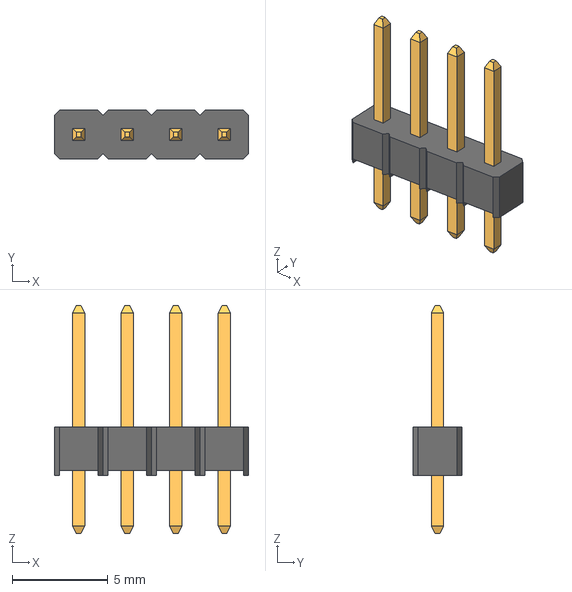
[picture p166: CAD file, 2023-11-28]
CAD/STEP Templates/4-Pin Header - Male - 2.54mm.step
10.2 x 2.54 x 11.9 mm
