impatrq/aeroalert/CAD/STEP Templates/PinHeader_3x22_P2.54mm_Horizontal.step

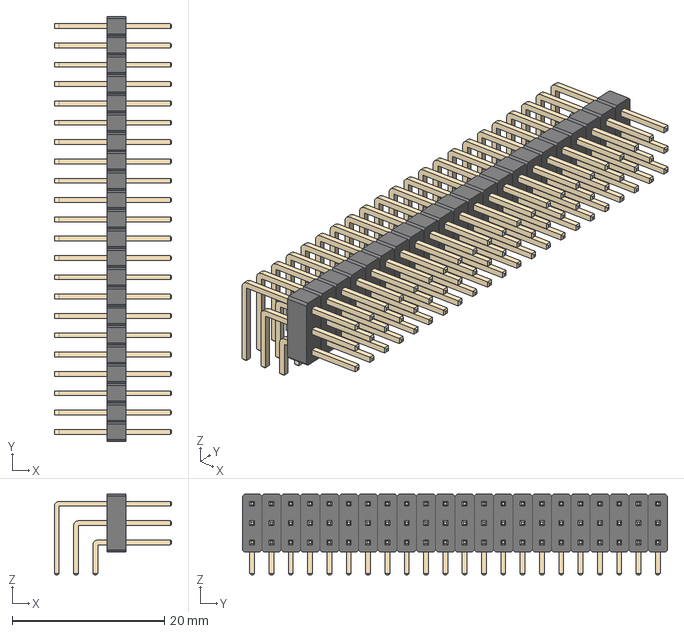
[picture p168: CAD file, 2023-11-28]
CAD/STEP Templates/PinHeader_3x22_P2.54mm_Horizontal.step
15.4 x 55.9 x 10.6 mm
