impatrq/aeroalert/CAD/STEP Templates/PinHeader_3x01_P2.54mm_Horizontal.step

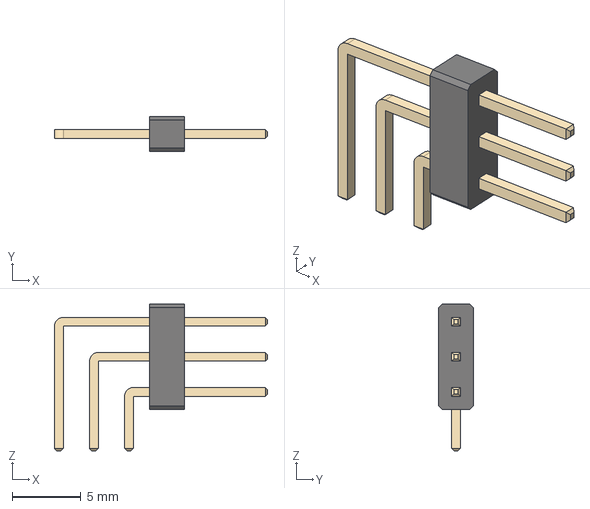
[picture p169: CAD file, 2023-11-28]
CAD/STEP Templates/PinHeader_3x01_P2.54mm_Horizontal.step
15.4 x 2.54 x 10.6 mm
