impatrq/aeroalert/CAD/STEP Templates/19-Pin Header - Female - 2.54mm.step

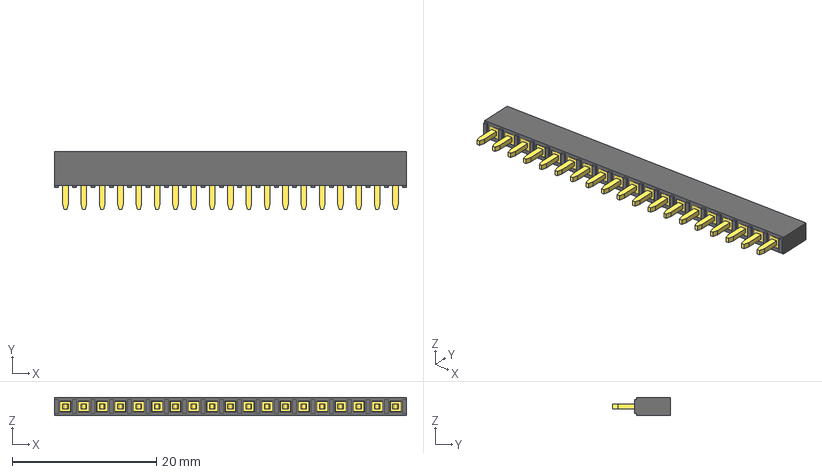
[picture p170: CAD file, 2023-11-28]
CAD/STEP Templates/19-Pin Header - Female - 2.54mm.step
48.8 x 8.00 x 2.50 mm
