impatrq/aeroalert/CAD/STEP Templates/TP4056 Charger Module.step

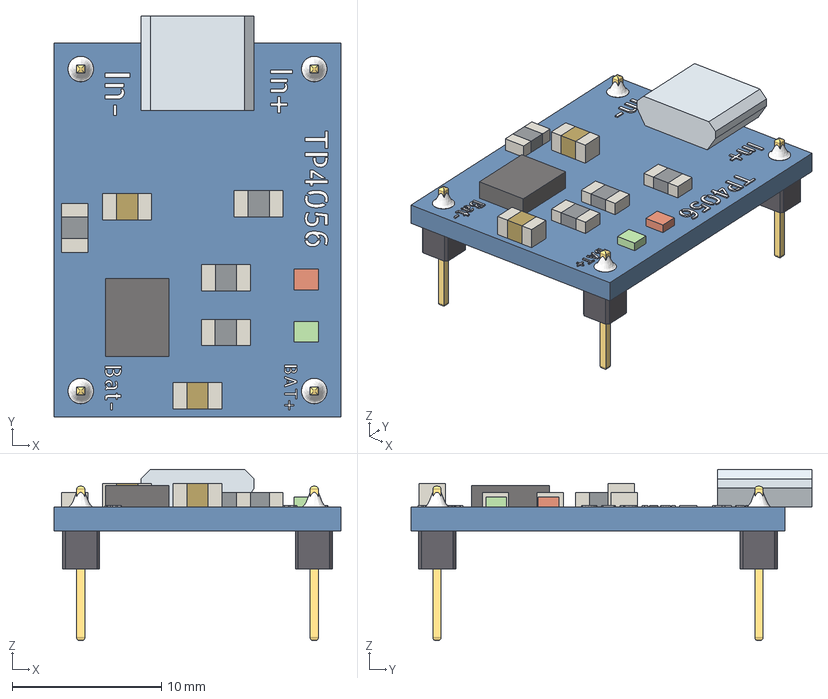
[picture p172: CAD file, 2023-11-28]
CAD/STEP Templates/TP4056 Charger Module.step
19.2 x 26.8 x 11.5 mm
Cap Body
Cap Ends
GREEN LED
IC
PCB
RED LED
Res Body
Res Ends
