impatrq/aeroalert/CAD/STEP Templates/12-Pin Header - Male - 2.54mm.step

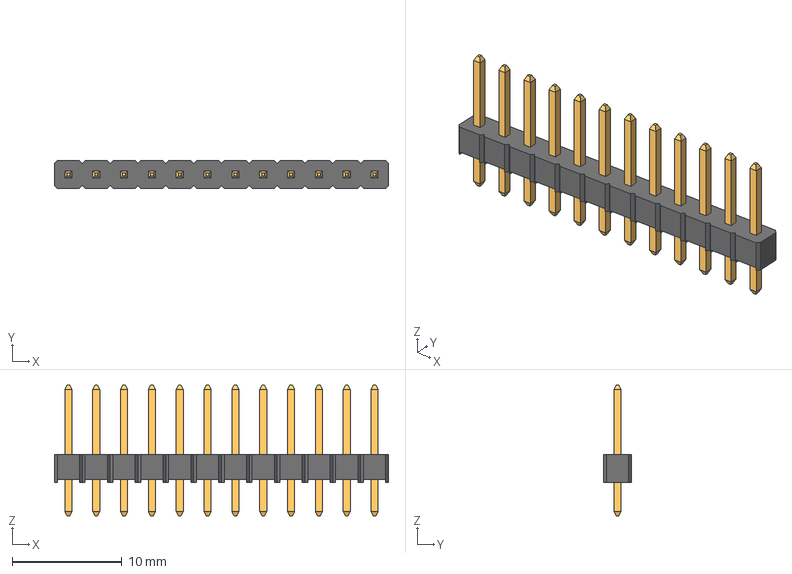
[picture p173: CAD file, 2023-11-28]
CAD/STEP Templates/12-Pin Header - Male - 2.54mm.step
30.5 x 2.54 x 11.9 mm
