impatrq/aeroalert/CAD/STEP Templates/2-Pin Header - Male - 2.54mm.step

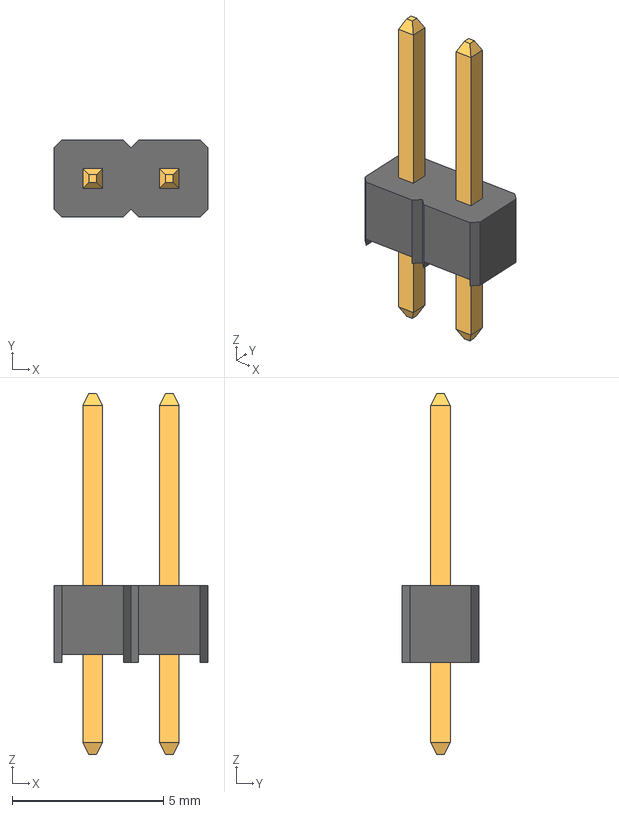
[picture p174: CAD file, 2023-11-28]
CAD/STEP Templates/2-Pin Header - Male - 2.54mm.step
5.08 x 2.54 x 11.9 mm
