impatrq/aeroalert/CAD/STEP Templates/PinHeader_3x10_P2.54mm_Horizontal.step

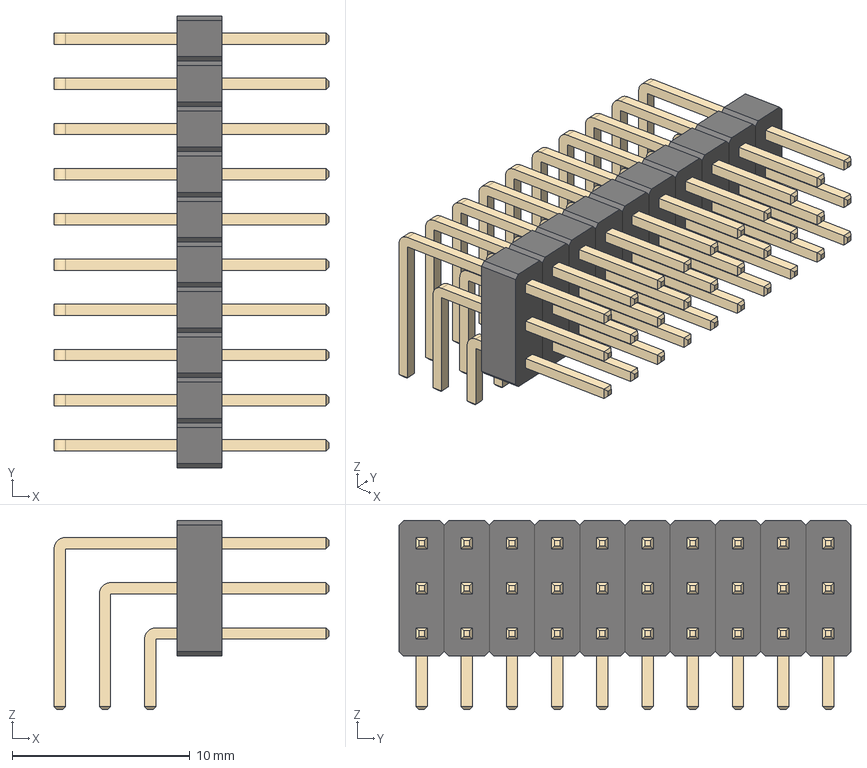
[picture p175: CAD file, 2023-11-28]
CAD/STEP Templates/PinHeader_3x10_P2.54mm_Horizontal.step
15.4 x 25.4 x 10.6 mm
