impatrq/aeroalert/CAD/STEP Templates/PinHeader_3x31_P2.54mm_Horizontal.step

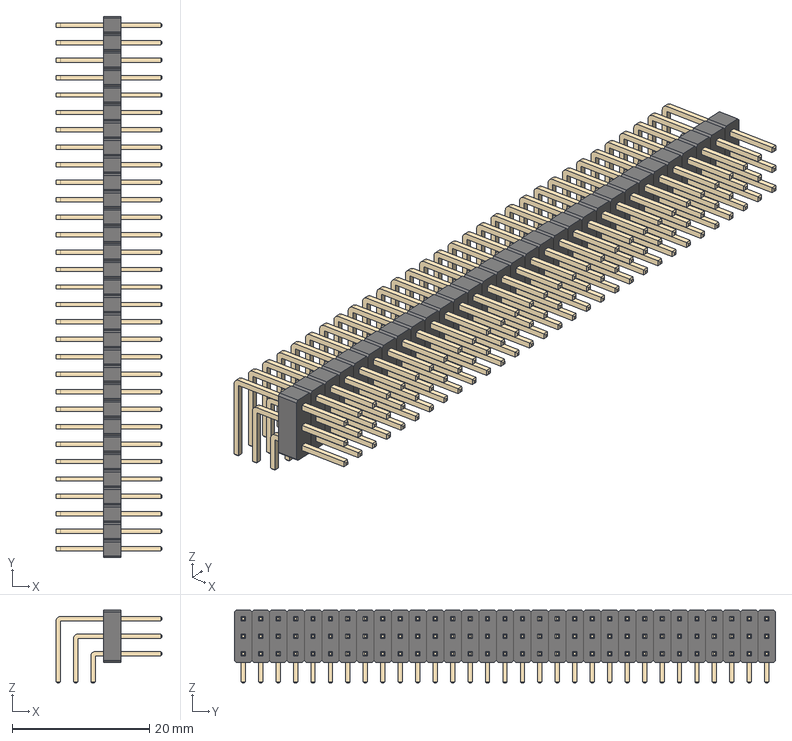
[picture p176: CAD file, 2023-11-28]
CAD/STEP Templates/PinHeader_3x31_P2.54mm_Horizontal.step
15.4 x 78.7 x 10.6 mm
