impatrq/aeroalert/CAD/STEP Templates/PinHeader_3x09_P2.54mm_Horizontal.step

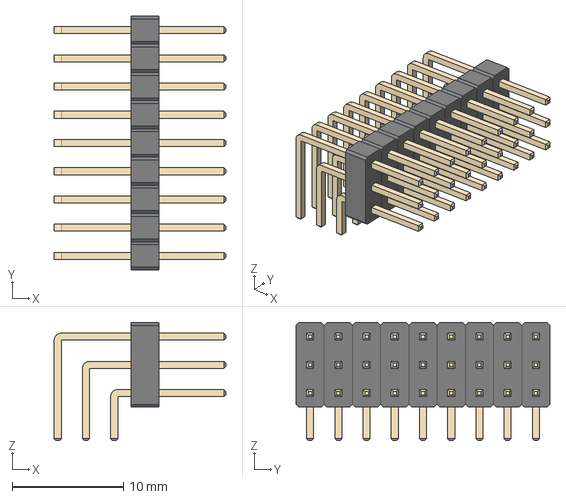
[picture p179: CAD file, 2023-11-28]
CAD/STEP Templates/PinHeader_3x09_P2.54mm_Horizontal.step
15.4 x 22.9 x 10.6 mm
