impatrq/aeroalert/CAD/STEP Templates/PinHeader_3x20_P2.54mm_Horizontal.step

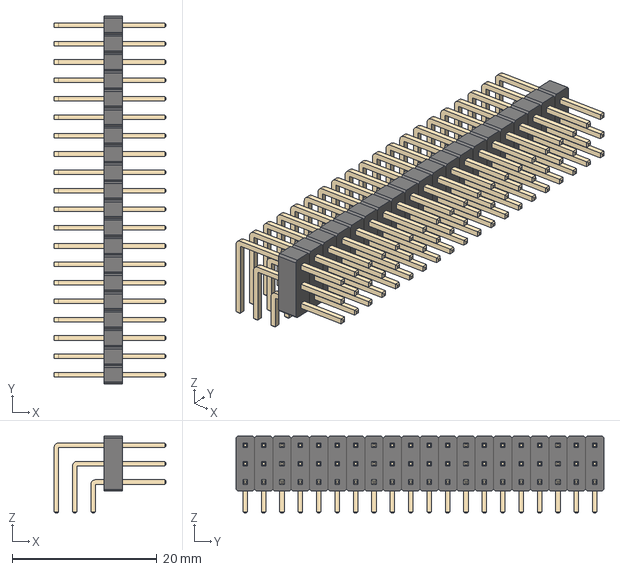
[picture p180: CAD file, 2023-11-28]
CAD/STEP Templates/PinHeader_3x20_P2.54mm_Horizontal.step
15.4 x 50.8 x 10.6 mm
