impatrq/aeroalert/CAD/STEP Templates/4-Pin Header - Female - 2.54mm.step

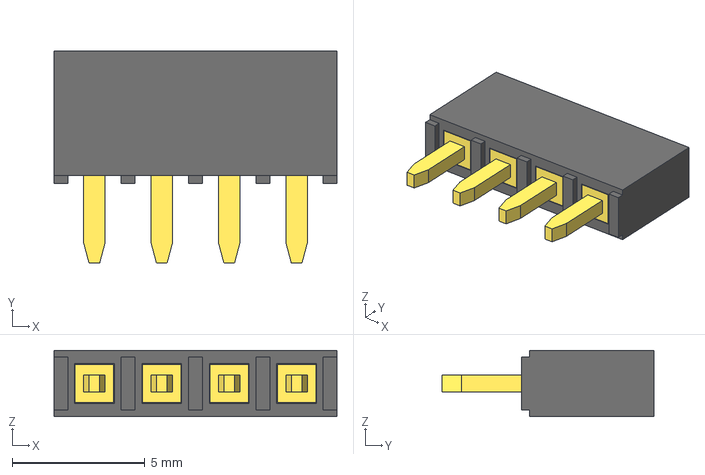
[picture p181: CAD file, 2023-11-28]
CAD/STEP Templates/4-Pin Header - Female - 2.54mm.step
10.7 x 8.00 x 2.50 mm
