impatrq/aeroalert/CAD/STEP Templates/PinHeader_3x39_P2.54mm_Horizontal.step

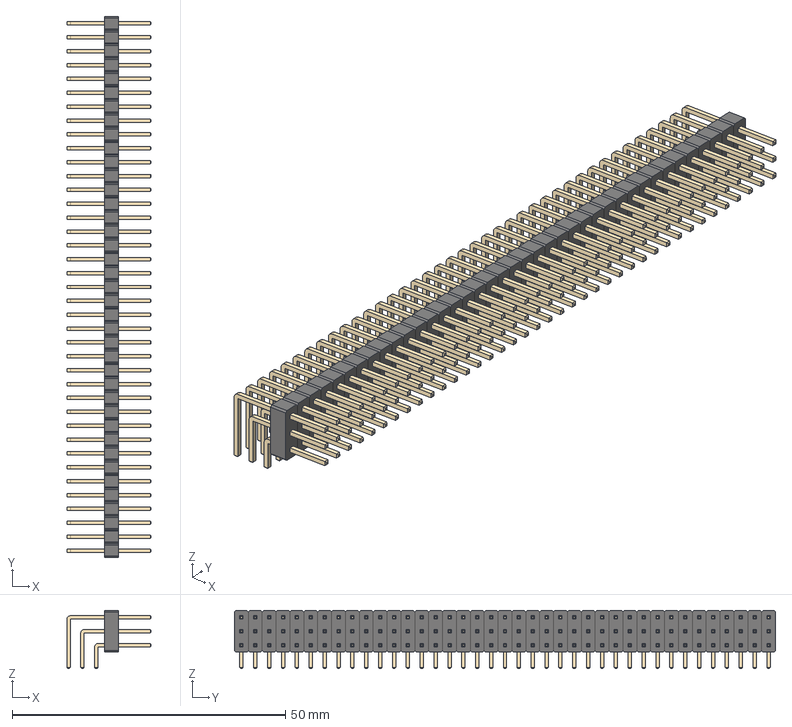
[picture p182: CAD file, 2023-11-28]
CAD/STEP Templates/PinHeader_3x39_P2.54mm_Horizontal.step
15.4 x 99.1 x 10.6 mm
Body_01 - 3x01_P2.54_Horizontal
Pin_02 - 3x01_P2.54_Horizontal
Pin_03 - 3x01_P2.54_Horizontal
Pin_01 - 3x01_P2.54_Horizontal
