impatrq/aeroalert/CAD/STEP Templates/PinHeader_3x19_P2.54mm_Horizontal.step

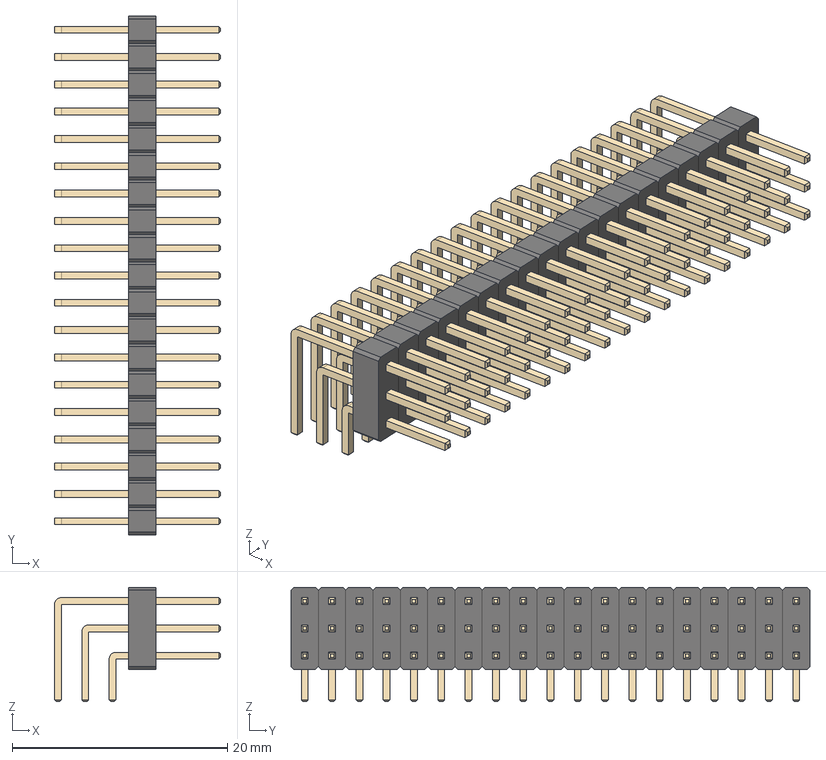
[picture p183: CAD file, 2023-11-28]
CAD/STEP Templates/PinHeader_3x19_P2.54mm_Horizontal.step
15.4 x 48.3 x 10.6 mm
