impatrq/aeroalert/CAD/STEP Templates/3-Pin Header - Male - 2.54mm.step

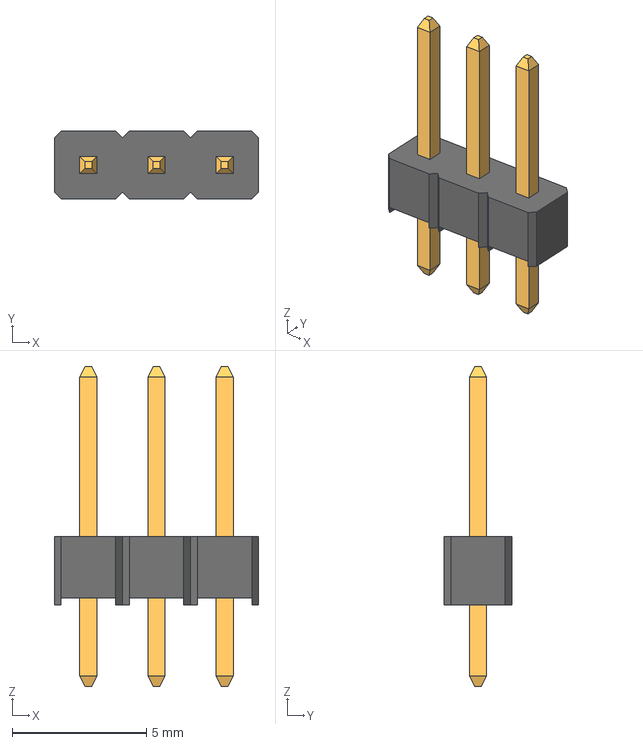
[picture p185: CAD file, 2023-11-28]
CAD/STEP Templates/3-Pin Header - Male - 2.54mm.step
7.62 x 2.54 x 11.9 mm
