impatrq/aeroalert/CAD/STEP Templates/PinHeader_3x08_P2.54mm_Horizontal.step

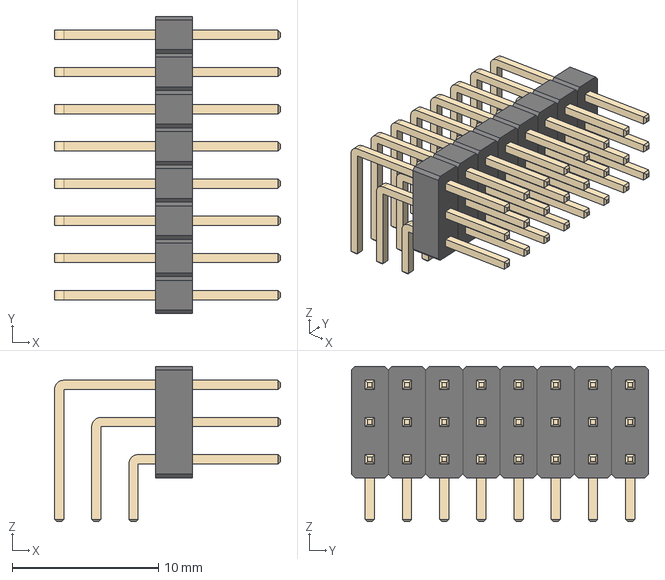
[picture p186: CAD file, 2023-11-28]
CAD/STEP Templates/PinHeader_3x08_P2.54mm_Horizontal.step
15.4 x 20.3 x 10.6 mm
