impatrq/aeroalert/CAD/STEP Templates/H254_90deg_3pin.STEP

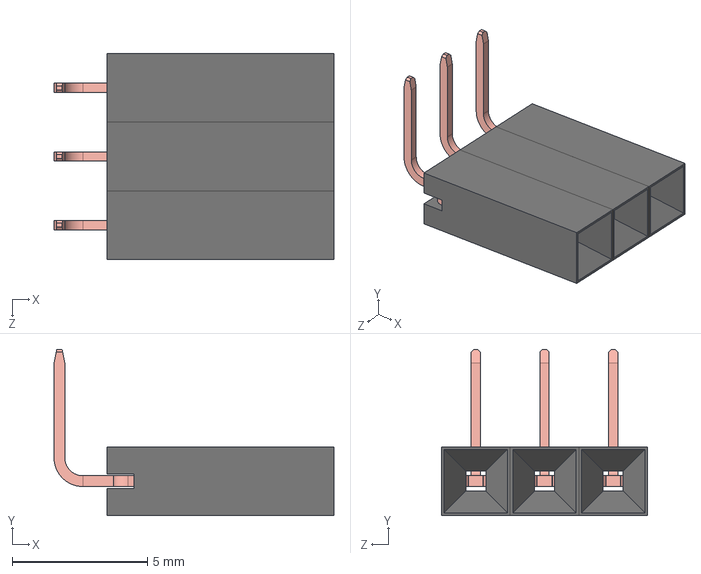
[picture p187: CAD file, 2023-11-28]
CAD/STEP Templates/H254_90deg_3pin.STEP
10.4 x 6.14 x 7.62 mm
frame_H254 x 3
pin-90deg x 3
