impatrq/aeroalert/CAD/STEP Templates/10-Pin Header - Female - 2.54mm.step

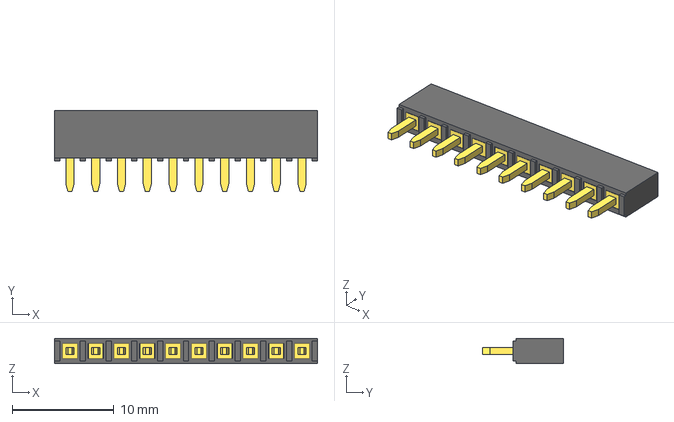
[picture p188: CAD file, 2023-11-28]
CAD/STEP Templates/10-Pin Header - Female - 2.54mm.step
25.9 x 8.00 x 2.50 mm
