impatrq/aeroalert/CAD/STEP Templates/2-Pin Header - Female - 2.54mm.step

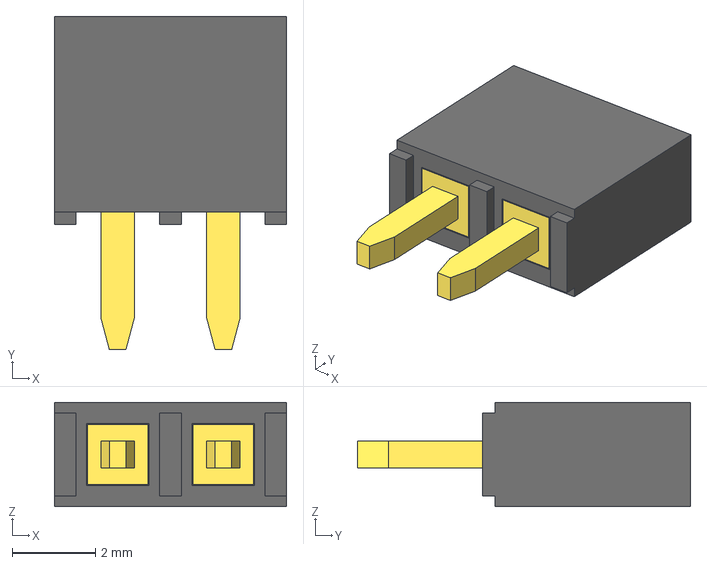
[picture p189: CAD file, 2023-11-28]
CAD/STEP Templates/2-Pin Header - Female - 2.54mm.step
5.58 x 8.00 x 2.50 mm
