impatrq/aeroalert/CAD/STEP Templates/12-Pin Header - Female - 2.54mm.step

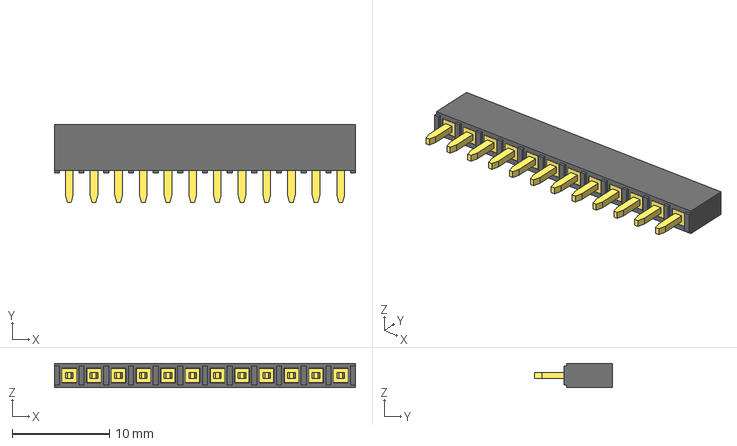
[picture p190: CAD file, 2023-11-28]
CAD/STEP Templates/12-Pin Header - Female - 2.54mm.step
31.0 x 8.00 x 2.50 mm
