impatrq/aeroalert/CAD/STEP Templates/PinHeaderTripleRow.step

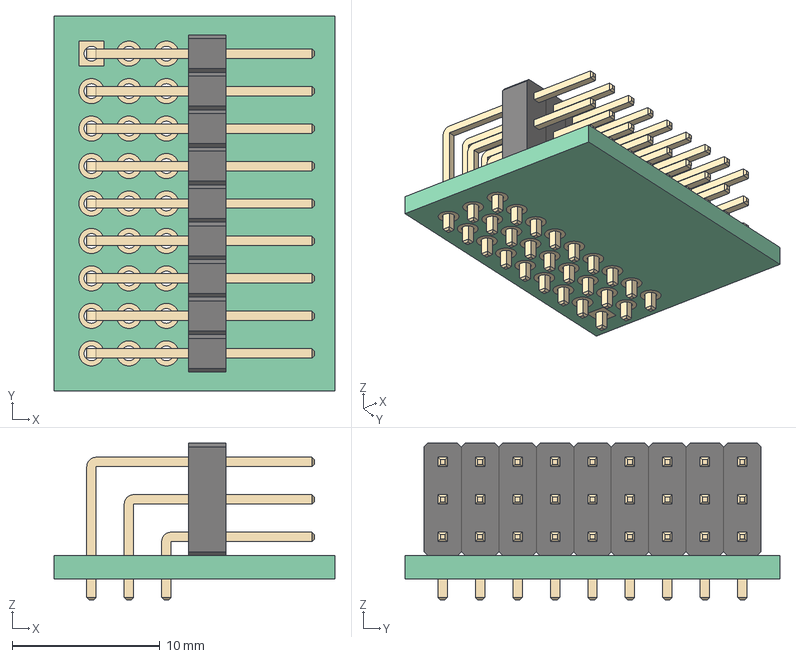
[picture p192: CAD file, 2023-11-28]
CAD/STEP Templates/PinHeaderTripleRow.step
19.0 x 25.4 x 10.6 mm
Pcb_36a9
topPads_36a9_cut
botPads_36a9
PinHeader_3x09_P2.54mm_Horizontal
PinHeader_3x09_P2.54mm_Horizontal001
PinHeader_3x09_P2.54mm_Horizontal002
PinHeader_3x09_P2.54mm_Horizontal003
PinHeader_3x09_P2.54mm_Horizontal004
PinHeader_3x09_P2.54mm_Horizontal005
PinHeader_3x09_P2.54mm_Horizontal006
PinHeader_3x09_P2.54mm_Horizontal007
PinHeader_3x09_P2.54mm_Horizontal008
PinHeader_3x09_P2.54mm_Horizontal009
PinHeader_3x09_P2.54mm_Horizontal010
PinHeader_3x09_P2.54mm_Horizontal011
PinHeader_3x09_P2.54mm_Horizontal012
PinHeader_3x09_P2.54mm_Horizontal013
PinHeader_3x09_P2.54mm_Horizontal014
PinHeader_3x09_P2.54mm_Horizontal015
PinHeader_3x09_P2.54mm_Horizontal016
PinHeader_3x09_P2.54mm_Horizontal017
PinHeader_3x09_P2.54mm_Horizontal018
PinHeader_3x09_P2.54mm_Horizontal019
PinHeader_3x09_P2.54mm_Horizontal020
PinHeader_3x09_P2.54mm_Horizontal021
PinHeader_3x09_P2.54mm_Horizontal022
PinHeader_3x09_P2.54mm_Horizontal023
PinHeader_3x09_P2.54mm_Horizontal024
PinHeader_3x09_P2.54mm_Horizontal025
PinHeader_3x09_P2.54mm_Horizontal026
PinHeader_3x09_P2.54mm_Horizontal027
PinHeader_3x09_P2.54mm_Horizontal028
PinHeader_3x09_P2.54mm_Horizontal029
PinHeader_3x09_P2.54mm_Horizontal030
PinHeader_3x09_P2.54mm_Horizontal031
PinHeader_3x09_P2.54mm_Horizontal032
PinHeader_3x09_P2.54mm_Horizontal033
PinHeader_3x09_P2.54mm_Horizontal034
PinHeader_3x09_P2.54mm_Horizontal035
