impatrq/aeroalert/CAD/STEP Templates/6-Pin Header - Male - 2.54mm.step

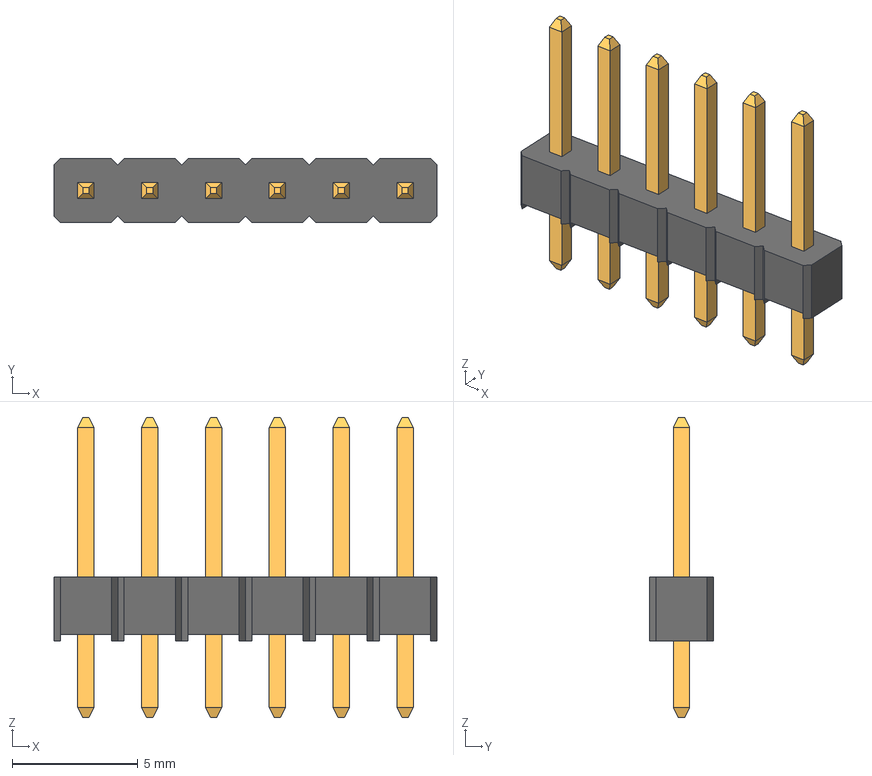
[picture p194: CAD file, 2023-11-28]
CAD/STEP Templates/6-Pin Header - Male - 2.54mm.step
15.2 x 2.54 x 11.9 mm
