impatrq/aeroalert/CAD/STEP Templates/pin-90deg.SLDPRT

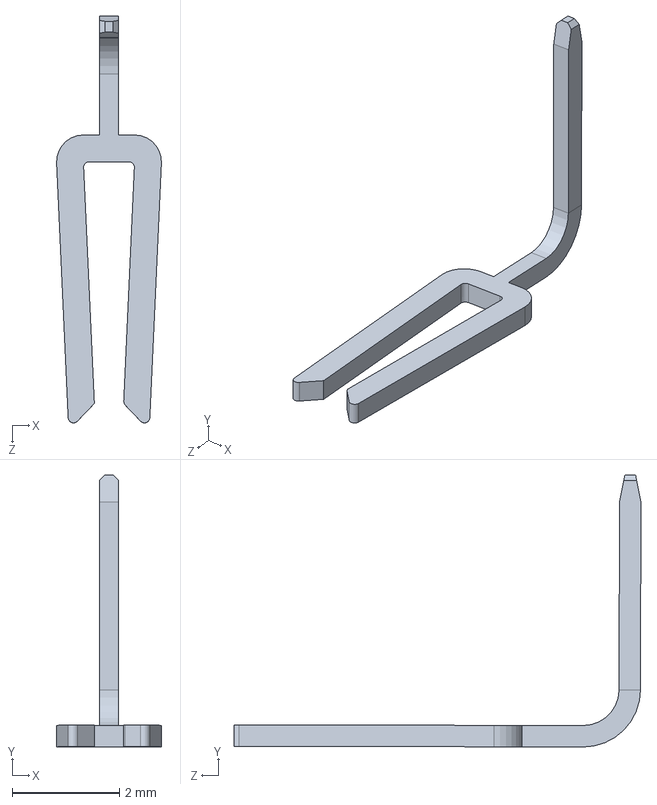
[picture p195: CAD file, 2023-11-28]
CAD/STEP Templates/pin-90deg.SLDPRT
1.95 x 5.07 x 7.58 mm
