impatrq/aeroalert/CAD/STEP Templates/PinHeader_3x23_P2.54mm_Horizontal.step

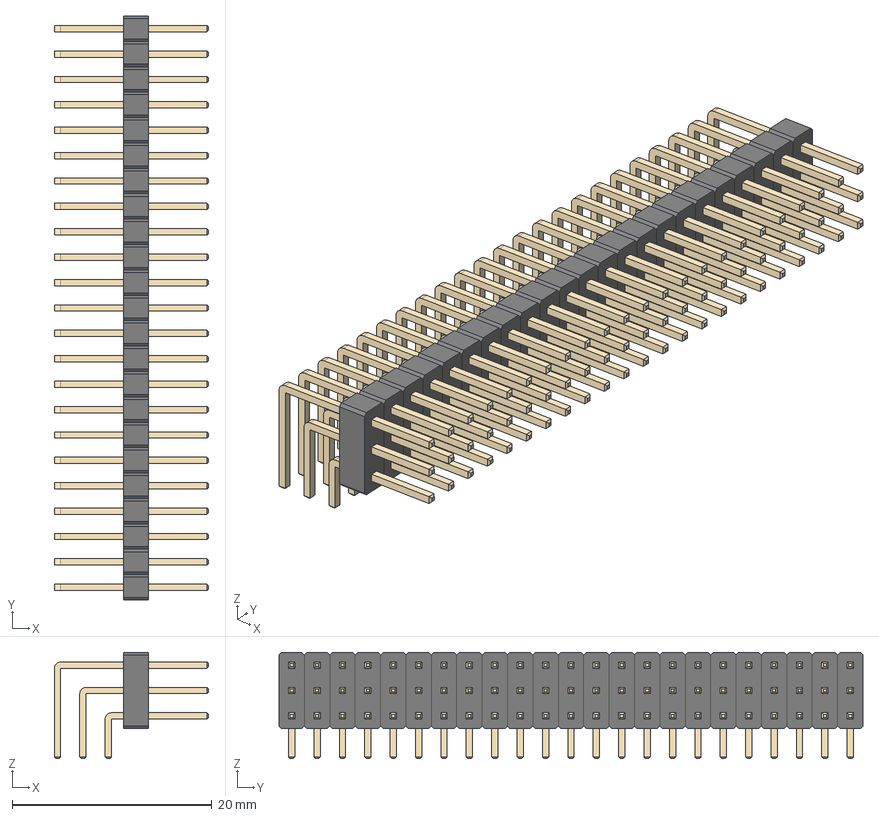
[picture p196: CAD file, 2023-11-28]
CAD/STEP Templates/PinHeader_3x23_P2.54mm_Horizontal.step
15.4 x 58.4 x 10.6 mm
