impatrq/aeroalert/CAD/STEP Templates/PinHeader_3x30_P2.54mm_Horizontal.step

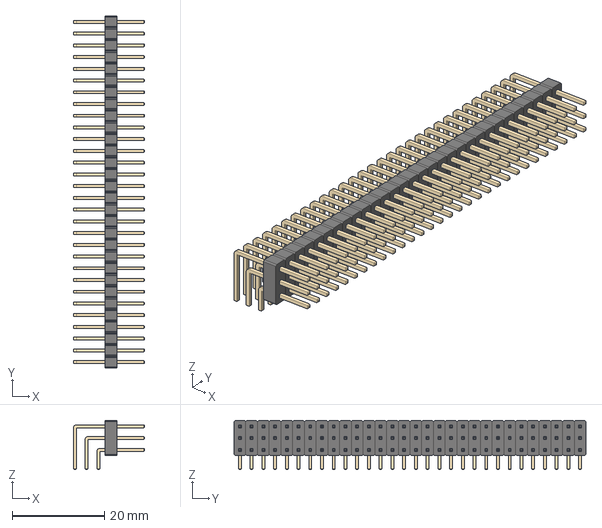
[picture p197: CAD file, 2023-11-28]
CAD/STEP Templates/PinHeader_3x30_P2.54mm_Horizontal.step
15.4 x 76.2 x 10.6 mm
