impatrq/aeroalert/CAD/STEP Templates/PinHeader_3x27_P2.54mm_Horizontal.step

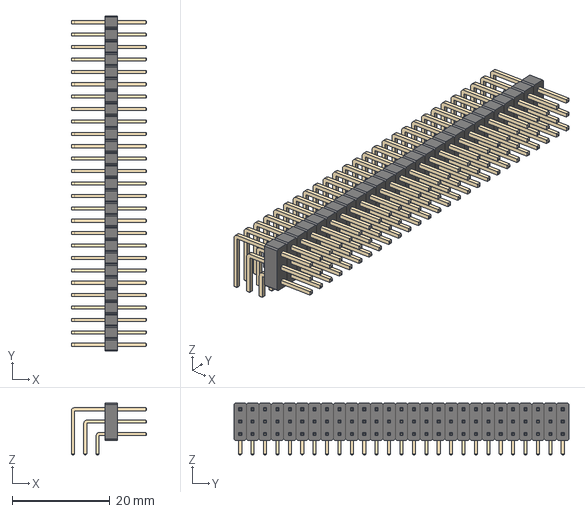
[picture p198: CAD file, 2023-11-28]
CAD/STEP Templates/PinHeader_3x27_P2.54mm_Horizontal.step
15.4 x 68.6 x 10.6 mm
