impatrq/aeroalert/CAD/STEP Templates/9-Pin Header - Female - 2.54mm.step

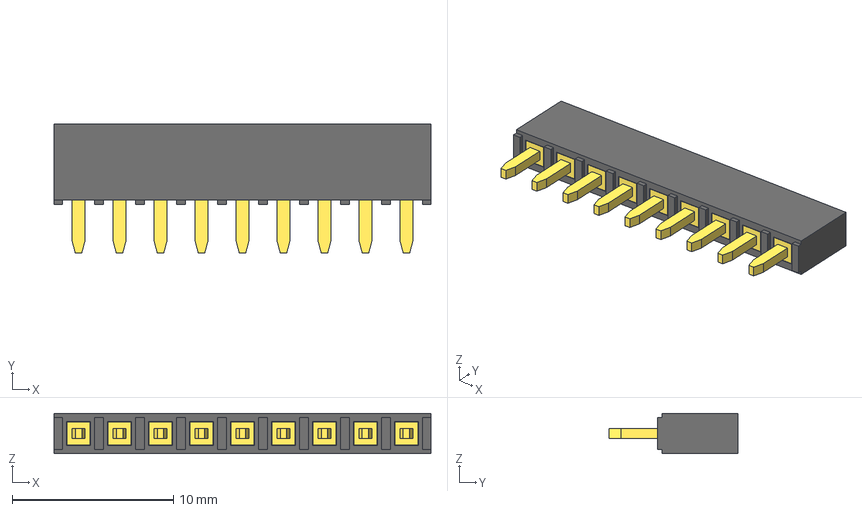
[picture p200: CAD file, 2023-11-28]
CAD/STEP Templates/9-Pin Header - Female - 2.54mm.step
23.4 x 8.00 x 2.50 mm
