impatrq/aeroalert/CAD/STEP Templates/7-Pin Header - Female - 2.54mm.step

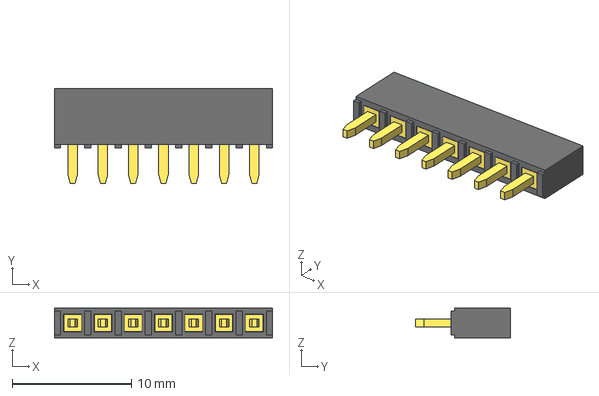
[picture p201: CAD file, 2023-11-28]
CAD/STEP Templates/7-Pin Header - Female - 2.54mm.step
18.3 x 8.00 x 2.50 mm
