impatrq/aeroalert/CAD/STEP Templates/PinHeader_3x29_P2.54mm_Horizontal.step

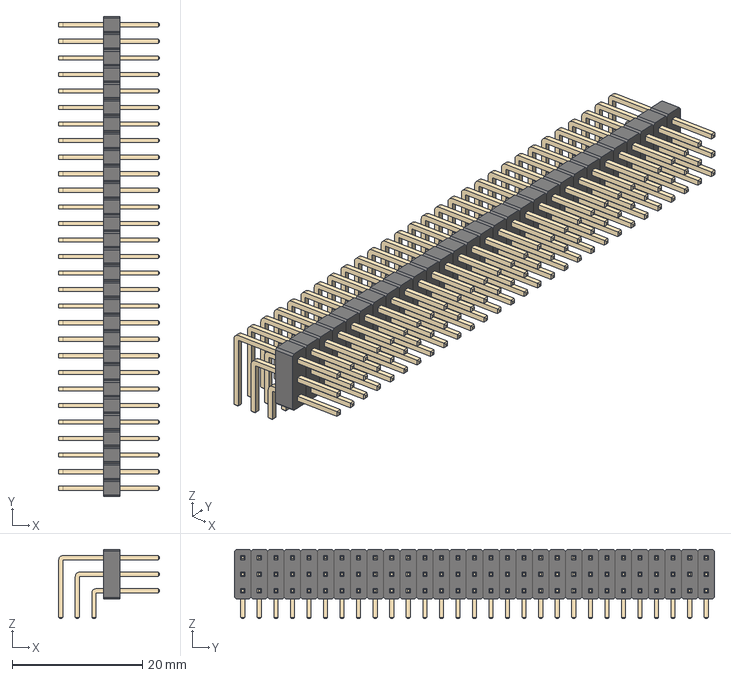
[picture p203: CAD file, 2023-11-28]
CAD/STEP Templates/PinHeader_3x29_P2.54mm_Horizontal.step
15.4 x 73.7 x 10.6 mm
