impatrq/aeroalert/CAD/STEP Templates/5-Pin Header - Male - 2.54mm.step

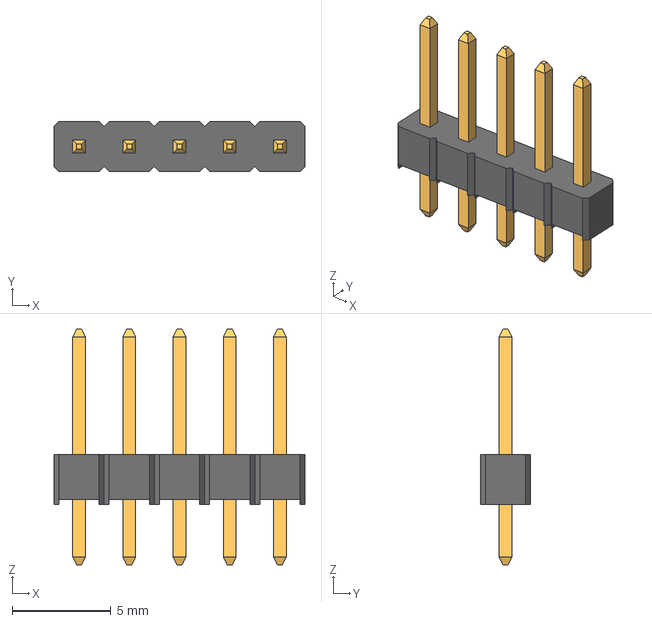
[picture p204: CAD file, 2023-11-28]
CAD/STEP Templates/5-Pin Header - Male - 2.54mm.step
12.7 x 2.54 x 11.9 mm
