impatrq/aeroalert/CAD/STEP Templates/female connector for apple watch band.STEP

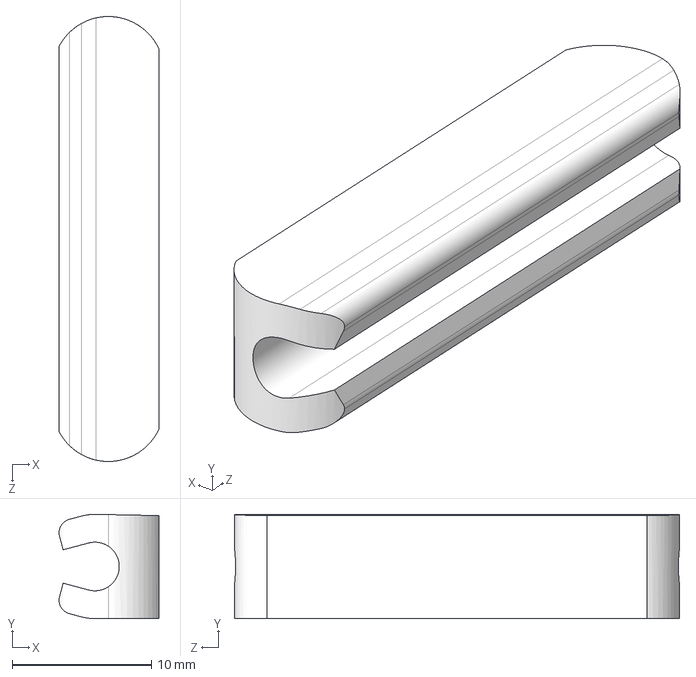
[picture p206: CAD file, 2023-11-28]
CAD/STEP Templates/female connector for apple watch band.STEP
7.18 x 7.50 x 32.0 mm
