impatrq/aeroalert/CAD/STEP Templates/8-Pin Header - Male - 2.54mm.step

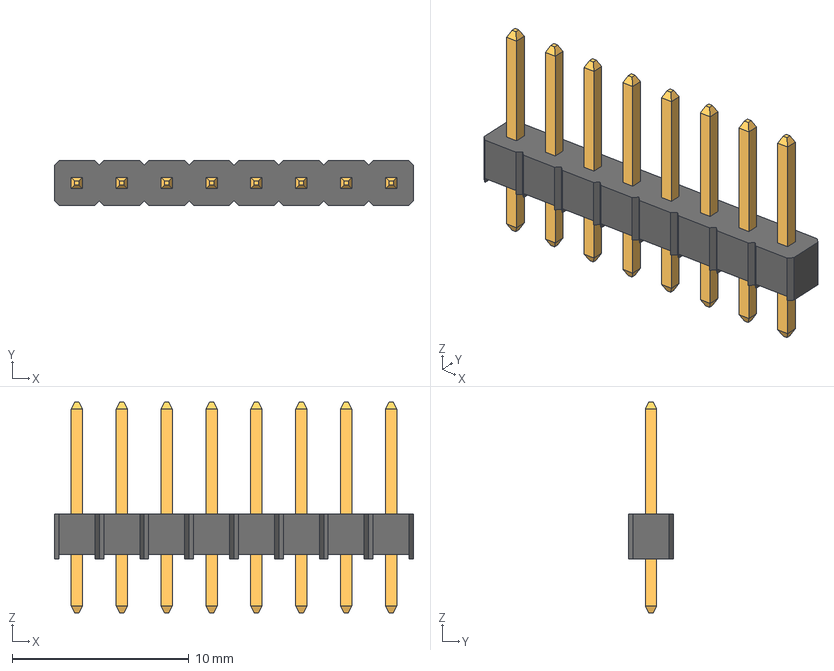
[picture p207: CAD file, 2023-11-28]
CAD/STEP Templates/8-Pin Header - Male - 2.54mm.step
20.3 x 2.54 x 11.9 mm
