impatrq/aeroalert/CAD/STEP Templates/19-Pin Header - Male - 2.54mm.step

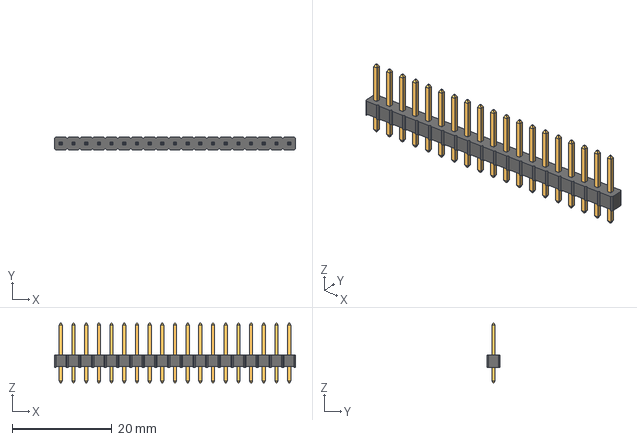
[picture p208: CAD file, 2023-11-28]
CAD/STEP Templates/19-Pin Header - Male - 2.54mm.step
48.3 x 2.54 x 11.9 mm
