impatrq/aeroalert/CAD/STEP Templates/Male HDR 2.54 2x1 Right Angle.STEP

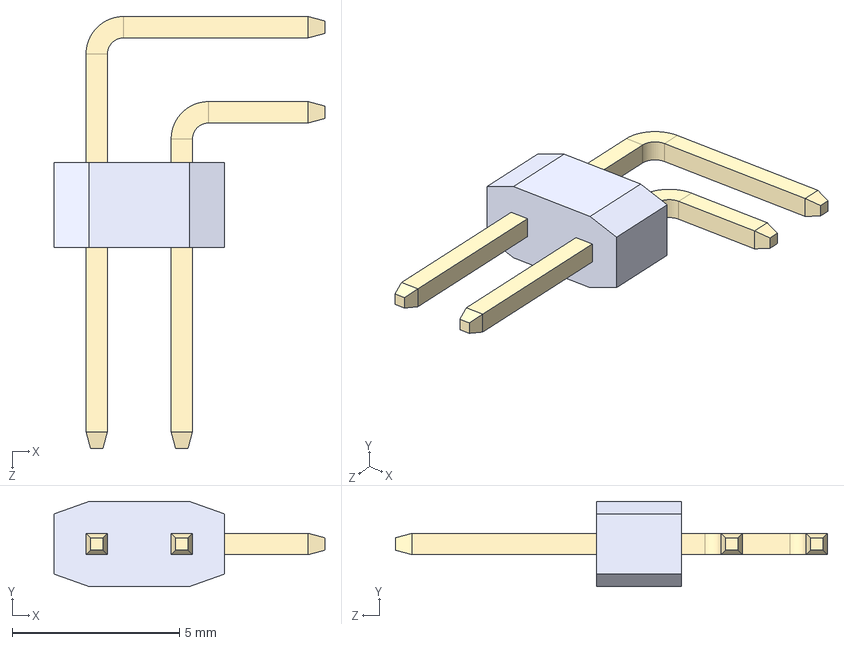
[picture p209: CAD file, 2023-11-28]
CAD/STEP Templates/Male HDR 2.54 2x1 Right Angle.STEP
8.08 x 2.54 x 12.9 mm
