impatrq/aeroalert/CAD/STEP Templates/13-Pin Header - Male - 2.54mm.step

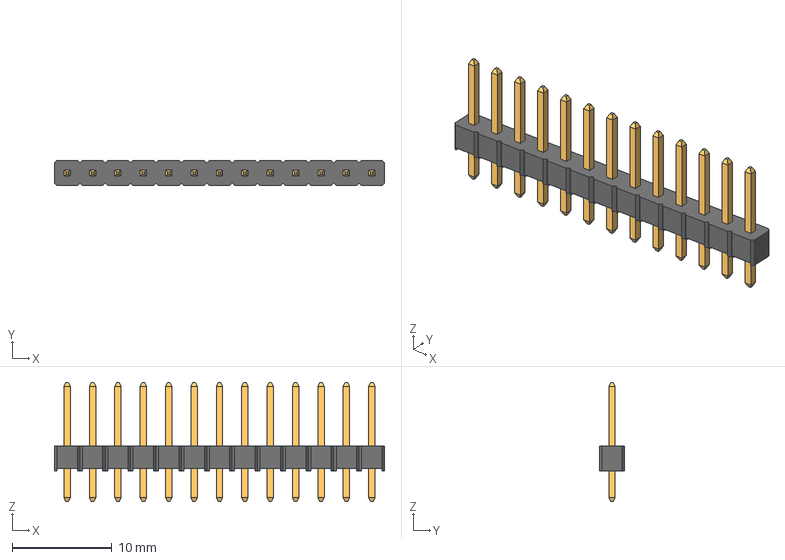
[picture p211: CAD file, 2023-11-28]
CAD/STEP Templates/13-Pin Header - Male - 2.54mm.step
33.0 x 2.54 x 11.9 mm
