impatrq/aeroalert/CAD/STEP Templates/PinHeader_3x07_P2.54mm_Horizontal.step

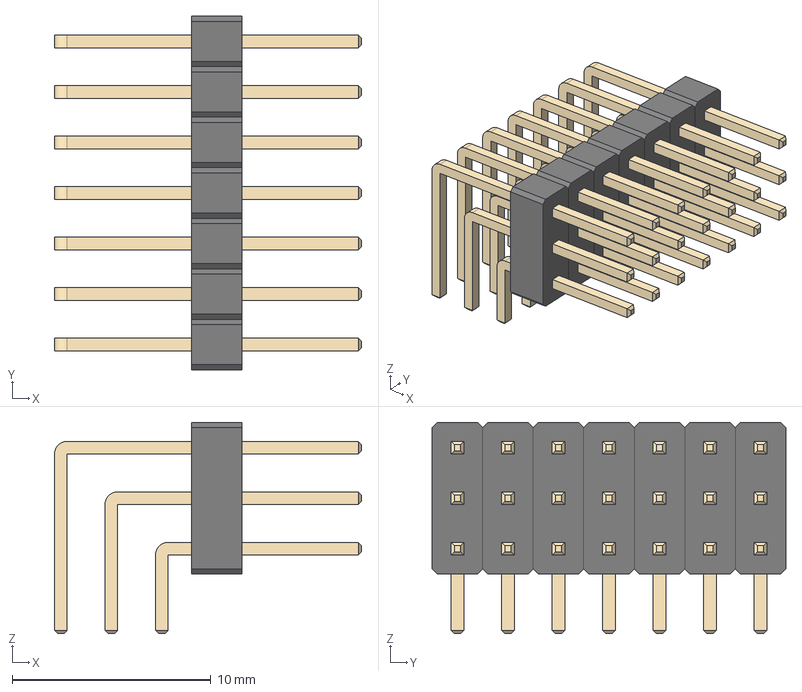
[picture p212: CAD file, 2023-11-28]
CAD/STEP Templates/PinHeader_3x07_P2.54mm_Horizontal.step
15.4 x 17.8 x 10.6 mm
