impatrq/aeroalert/CAD/STEP Templates/PinHeader_3x11_P2.54mm_Horizontal.step

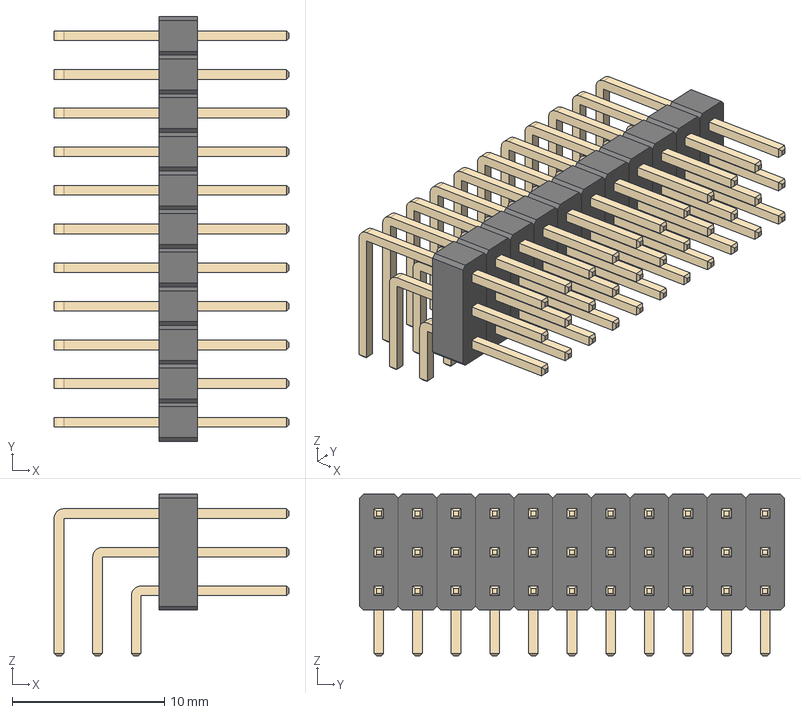
[picture p213: CAD file, 2023-11-28]
CAD/STEP Templates/PinHeader_3x11_P2.54mm_Horizontal.step
15.4 x 27.9 x 10.6 mm
