impatrq/aeroalert/CAD/STEP Templates/9-Pin Header - Male - 2.54mm.step

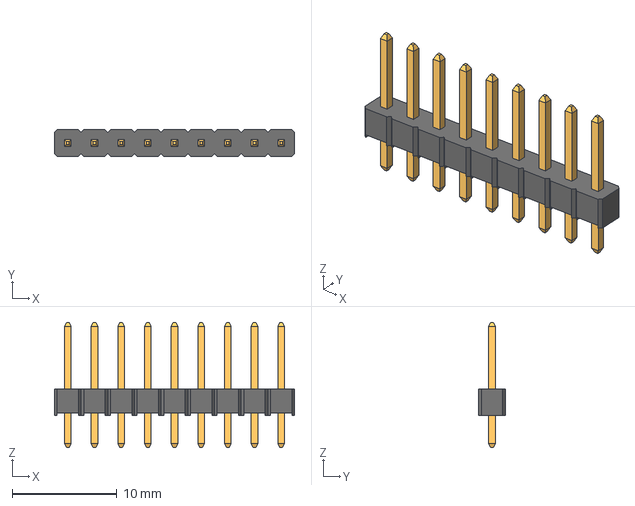
[picture p214: CAD file, 2023-11-28]
CAD/STEP Templates/9-Pin Header - Male - 2.54mm.step
22.9 x 2.54 x 11.9 mm
