impatrq/aeroalert/CAD/STEP Templates/16-Pin Header - Female - 2.54mm.step

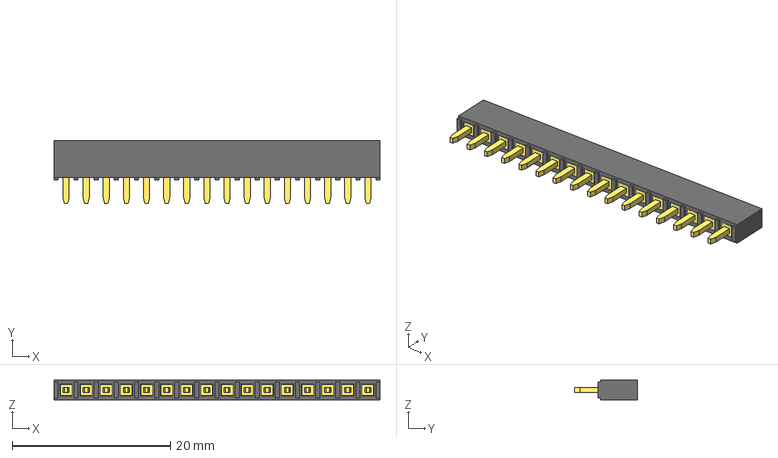
[picture p215: CAD file, 2023-11-28]
CAD/STEP Templates/16-Pin Header - Female - 2.54mm.step
41.1 x 8.00 x 2.50 mm
