impatrq/aeroalert/CAD/STEP Templates/SOT-223.step

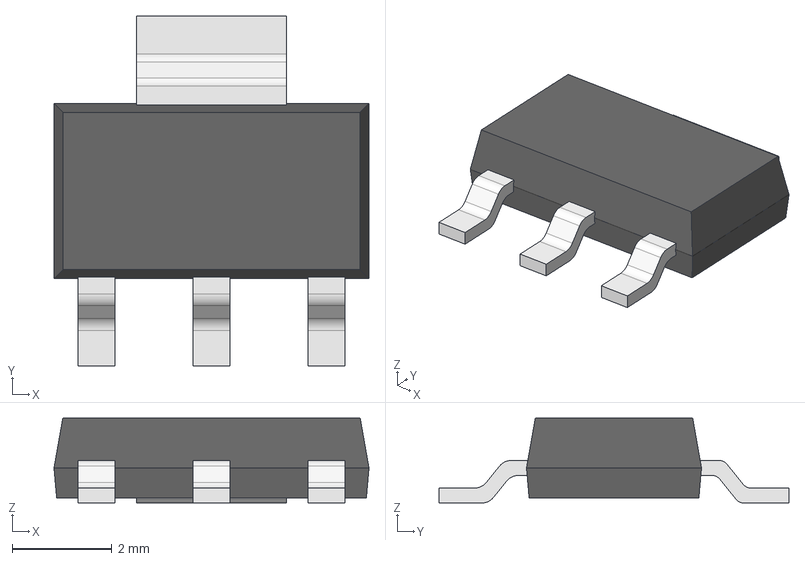
[picture p216: CAD file, 2023-11-28]
CAD/STEP Templates/SOT-223.step
6.30 x 7.00 x 1.70 mm
