impatrq/aeroalert/CAD/STEP Templates/8-Pin Header - Female - 2.54mm.step

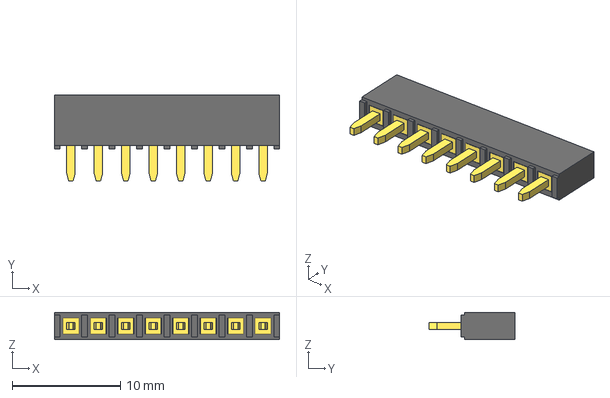
[picture p219: CAD file, 2023-11-28]
CAD/STEP Templates/8-Pin Header - Female - 2.54mm.step
20.8 x 8.00 x 2.50 mm
