impatrq/aeroalert/CAD/STEP Templates/17-Pin Header - Male - 2.54mm.step

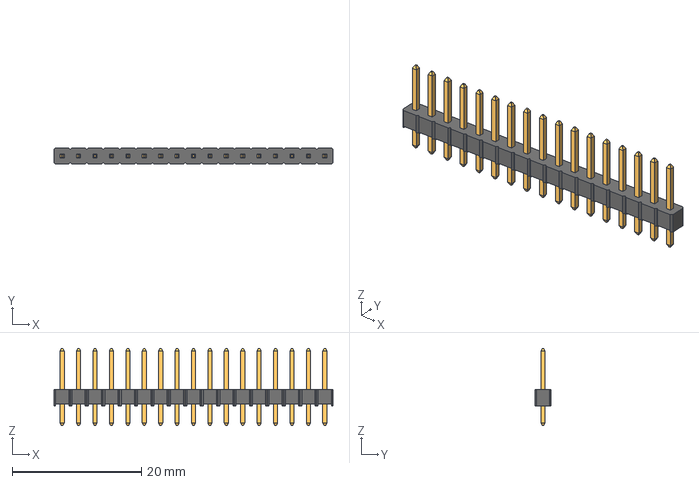
[picture p220: CAD file, 2023-11-28]
CAD/STEP Templates/17-Pin Header - Male - 2.54mm.step
43.2 x 2.54 x 11.9 mm
