impatrq/aeroalert/CAD/STEP Templates/3-Pin Header - Female - 2.54mm.step

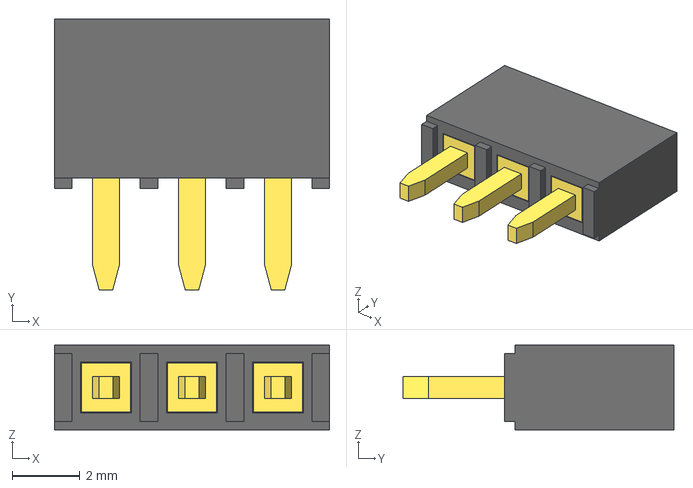
[picture p221: CAD file, 2023-11-28]
CAD/STEP Templates/3-Pin Header - Female - 2.54mm.step
8.12 x 8.00 x 2.50 mm
