impatrq/aeroalert/CAD/STEP Templates/14-Pin Header - Male - 2.54mm.step

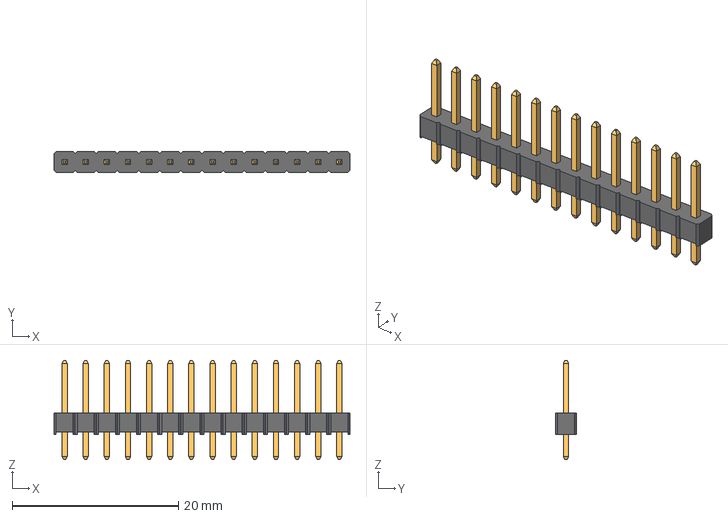
[picture p222: CAD file, 2023-11-28]
CAD/STEP Templates/14-Pin Header - Male - 2.54mm.step
35.6 x 2.54 x 11.9 mm
