impatrq/aeroalert/CAD/STEP Templates/15-Pin Header - Female - 2.54mm.step

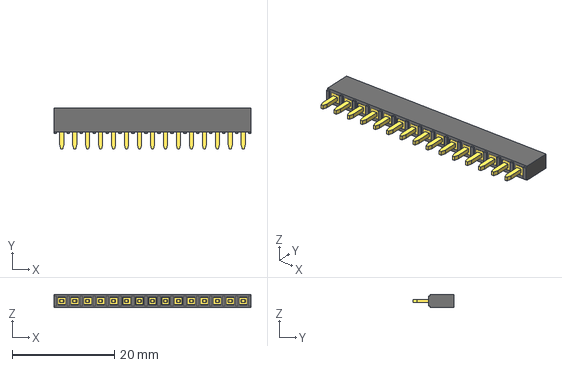
[picture p223: CAD file, 2023-11-28]
CAD/STEP Templates/15-Pin Header - Female - 2.54mm.step
38.6 x 8.00 x 2.50 mm
