impatrq/aeroalert/CAD/STEP Templates/SENSOR DE LA PULSERA.sldprt

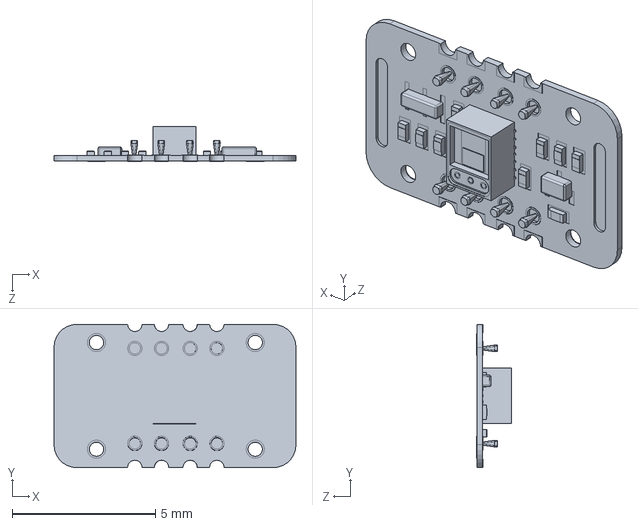
[picture p224: CAD file, 2023-11-28]
CAD/STEP Templates/SENSOR DE LA PULSERA.sldprt
8.44 x 5.00 x 1.21 mm
