impatrq/aeroalert/CAD/STEP Templates/frame_H254.sldprt

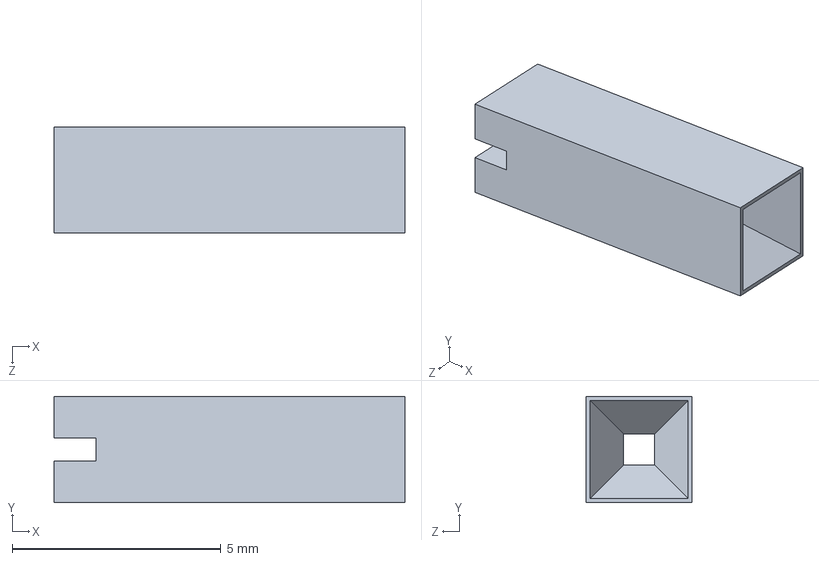
[picture p225: CAD file, 2023-11-28]
CAD/STEP Templates/frame_H254.sldprt
8.40 x 2.54 x 2.54 mm
