impatrq/aeroalert/CAD/STEP Templates/3.7v li-ion 500mah Battery.step

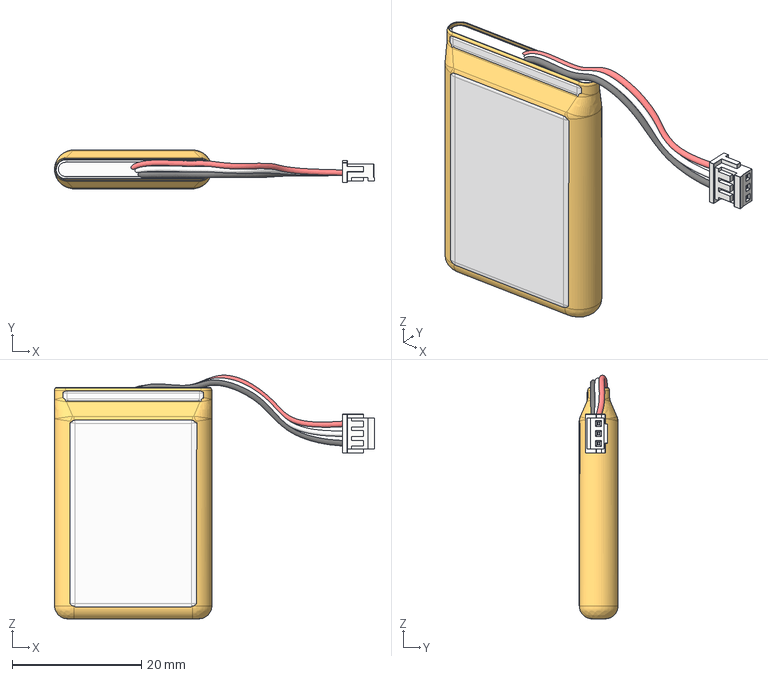
[picture p226: CAD file, 2023-11-28]
CAD/STEP Templates/3.7v li-ion 500mah Battery.step
49.6 x 6.05 x 37.8 mm
