impatrq/aeroalert/CAD/STEP Templates/10-Pin Header - Male - 2.54mm.step

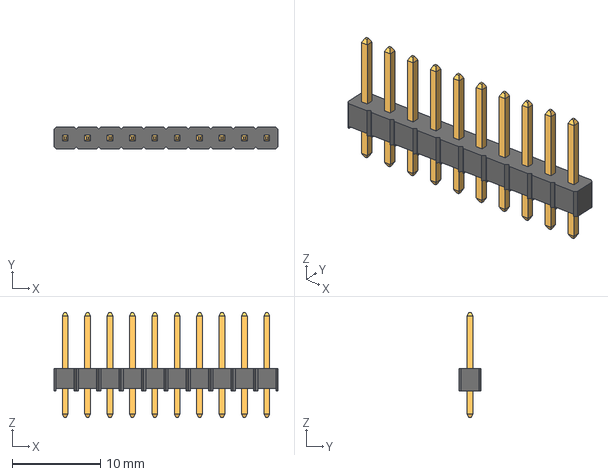
[picture p227: CAD file, 2023-11-28]
CAD/STEP Templates/10-Pin Header - Male - 2.54mm.step
25.4 x 2.54 x 11.9 mm
