impatrq/aeroalert/CAD/STEP Templates/PinHeader_3x05_P2.54mm_Horizontal.step

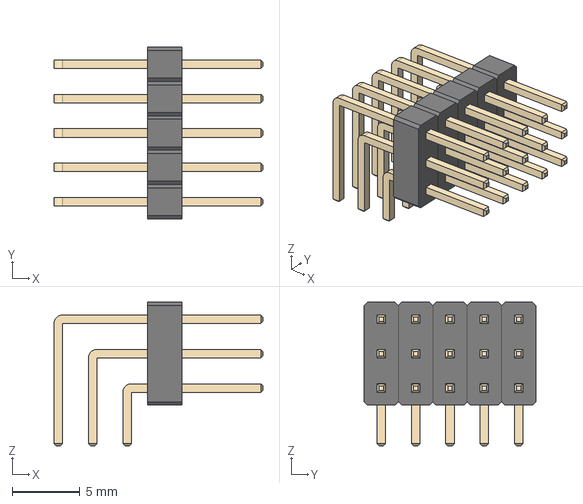
[picture p228: CAD file, 2023-11-28]
CAD/STEP Templates/PinHeader_3x05_P2.54mm_Horizontal.step
15.4 x 12.7 x 10.6 mm
