impatrq/aeroalert/CAD/STEP Templates/5-Pin Header - Female - 2.54mm.step

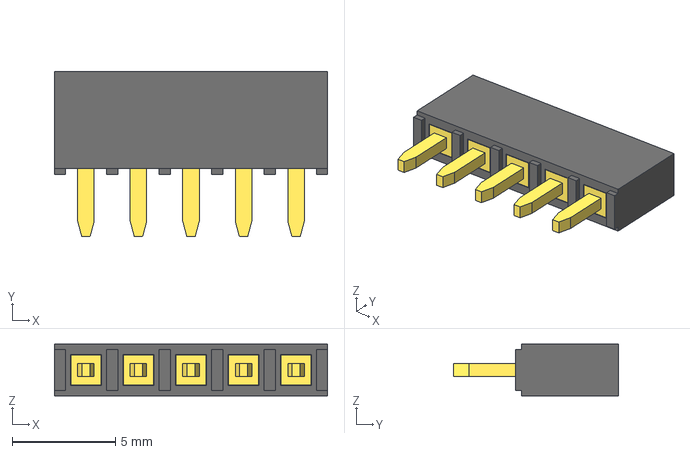
[picture p229: CAD file, 2023-11-28]
CAD/STEP Templates/5-Pin Header - Female - 2.54mm.step
13.2 x 8.00 x 2.50 mm
