impatrq/aeroalert/CAD/STEP Templates/11-Pin Header - Male - 2.54mm.step

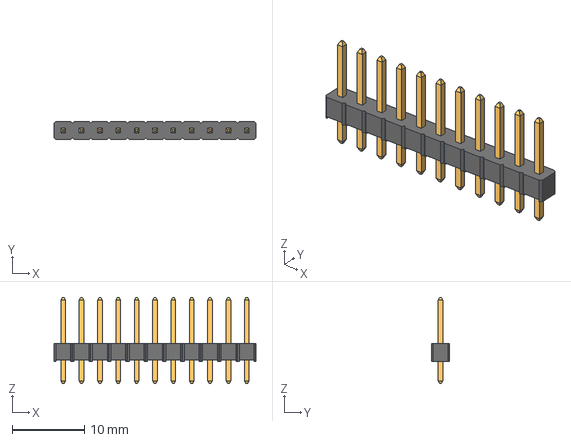
[picture p230: CAD file, 2023-11-28]
CAD/STEP Templates/11-Pin Header - Male - 2.54mm.step
27.9 x 2.54 x 11.9 mm
