impatrq/aeroalert/CAD/STEP Templates/PinHeader_3x25_P2.54mm_Horizontal.step

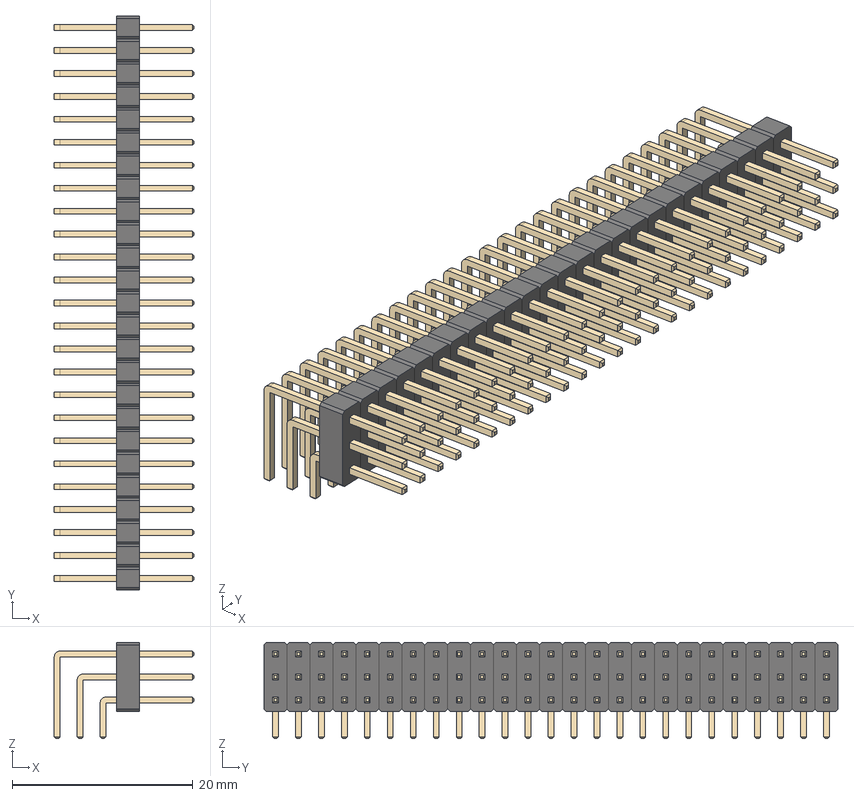
[picture p231: CAD file, 2023-11-28]
CAD/STEP Templates/PinHeader_3x25_P2.54mm_Horizontal.step
15.4 x 63.5 x 10.6 mm
