impatrq/aeroalert/CAD/STEP Templates/PinHeader_3x15_P2.54mm_Horizontal.step

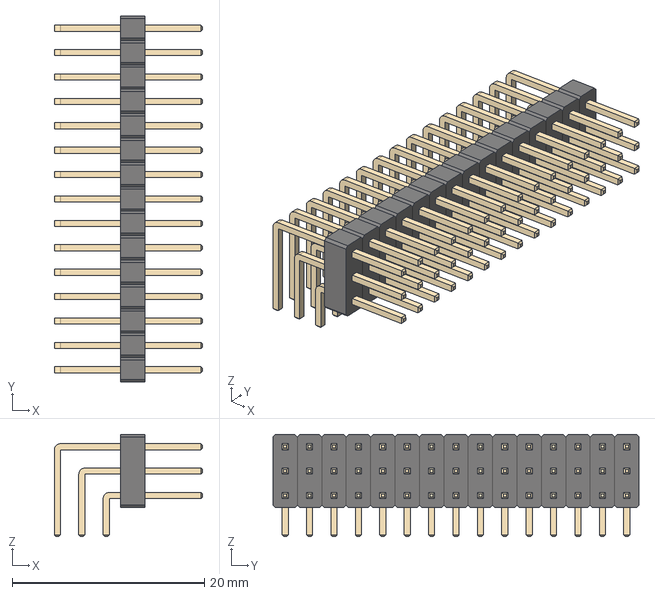
[picture p232: CAD file, 2023-11-28]
CAD/STEP Templates/PinHeader_3x15_P2.54mm_Horizontal.step
15.4 x 38.1 x 10.6 mm
