impatrq/aeroalert/CAD/STEP Templates/H254_90deg_5pin.STEP

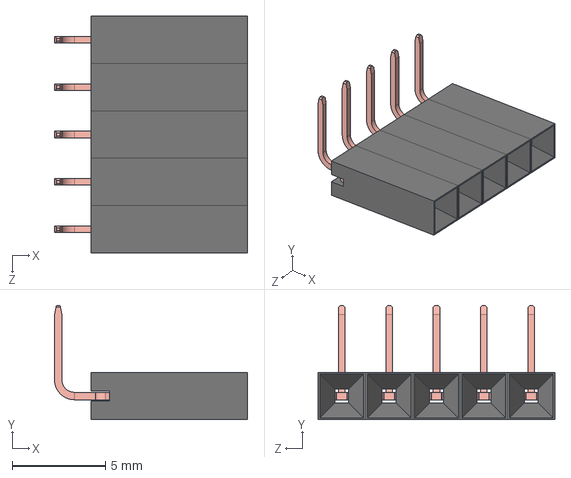
[picture p233: CAD file, 2023-11-28]
CAD/STEP Templates/H254_90deg_5pin.STEP
10.4 x 6.14 x 12.7 mm
frame_H254 x 5
pin-90deg x 5
