impatrq/aeroalert/CAD/STEP Templates/11-Pin Header - Female - 2.54mm.step

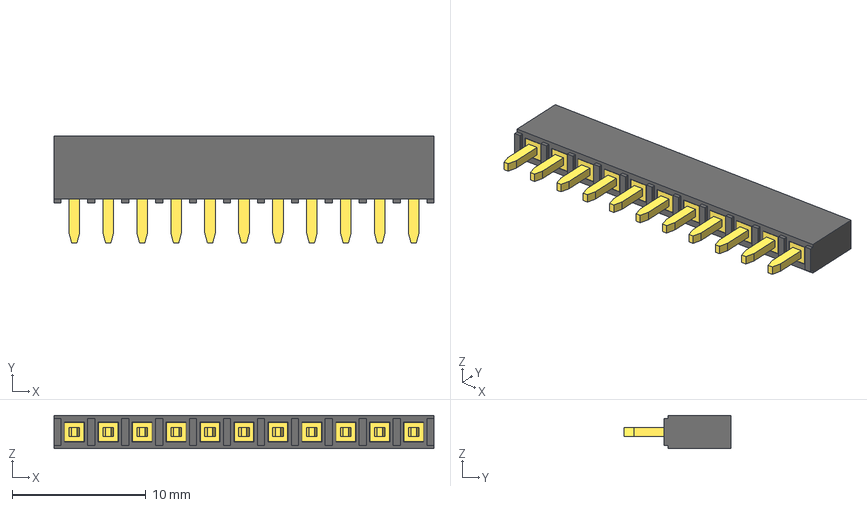
[picture p234: CAD file, 2023-11-28]
CAD/STEP Templates/11-Pin Header - Female - 2.54mm.step
28.4 x 8.00 x 2.50 mm
