impatrq/aeroalert/CAD/STEP Templates/15-Pin Header - Male - 2.54mm.step

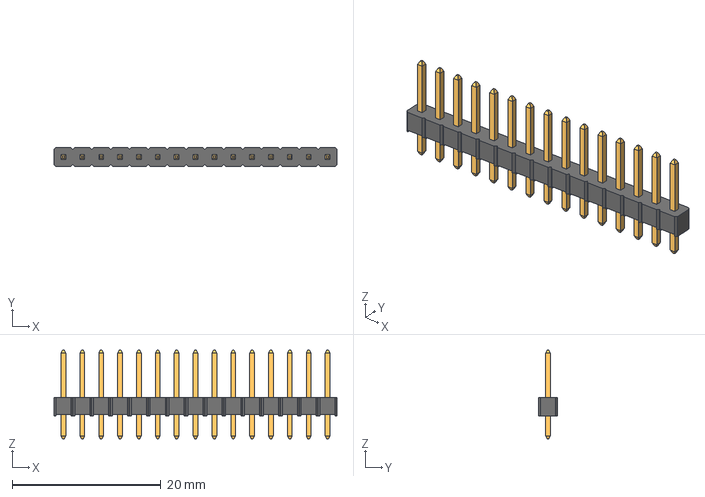
[picture p235: CAD file, 2023-11-28]
CAD/STEP Templates/15-Pin Header - Male - 2.54mm.step
38.1 x 2.54 x 11.9 mm
