impatrq/aeroalert/CAD/STEP Templates/17-Pin Header - Female - 2.54mm.step

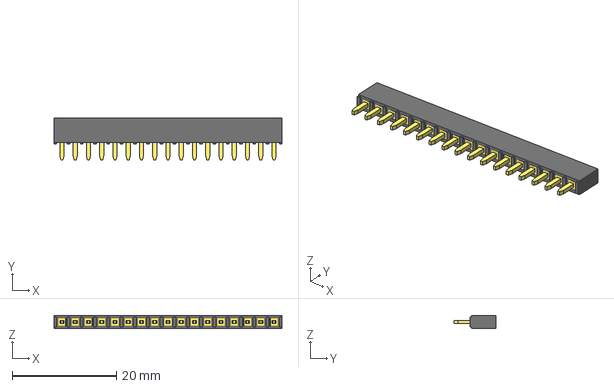
[picture p236: CAD file, 2023-11-28]
CAD/STEP Templates/17-Pin Header - Female - 2.54mm.step
43.7 x 8.00 x 2.50 mm
