impatrq/aeroalert/CAD/STEP Templates/PinHeader_3x14_P2.54mm_Horizontal.step

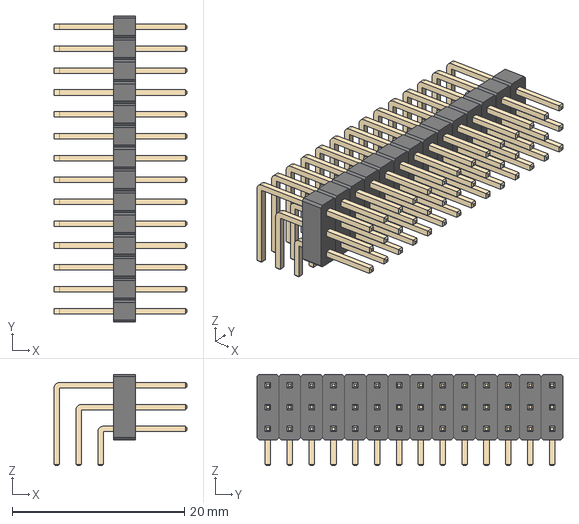
[picture p237: CAD file, 2023-11-28]
CAD/STEP Templates/PinHeader_3x14_P2.54mm_Horizontal.step
15.4 x 35.6 x 10.6 mm
