impatrq/aeroalert/CAD/STEP Templates/20-Pin Header - Male - 2.54mm.step

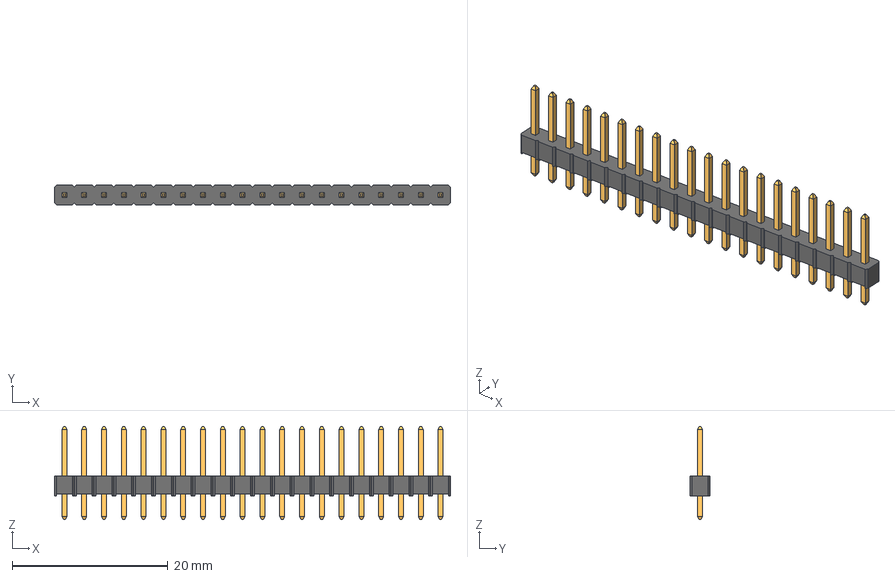
[picture p238: CAD file, 2023-11-28]
CAD/STEP Templates/20-Pin Header - Male - 2.54mm.step
50.8 x 2.54 x 11.9 mm
