impatrq/aeroalert/CAD/STEP Templates/18-Pin Header - Male - 2.54mm.step

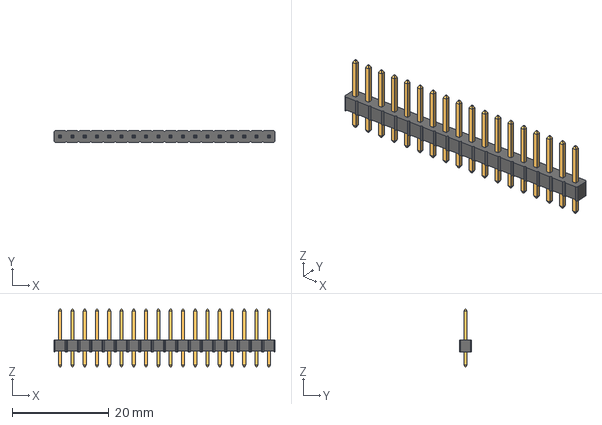
[picture p240: CAD file, 2023-11-28]
CAD/STEP Templates/18-Pin Header - Male - 2.54mm.step
45.7 x 2.54 x 11.9 mm
