impatrq/aeroalert/CAD/STEP Templates/PinHeader_3x32_P2.54mm_Horizontal.step

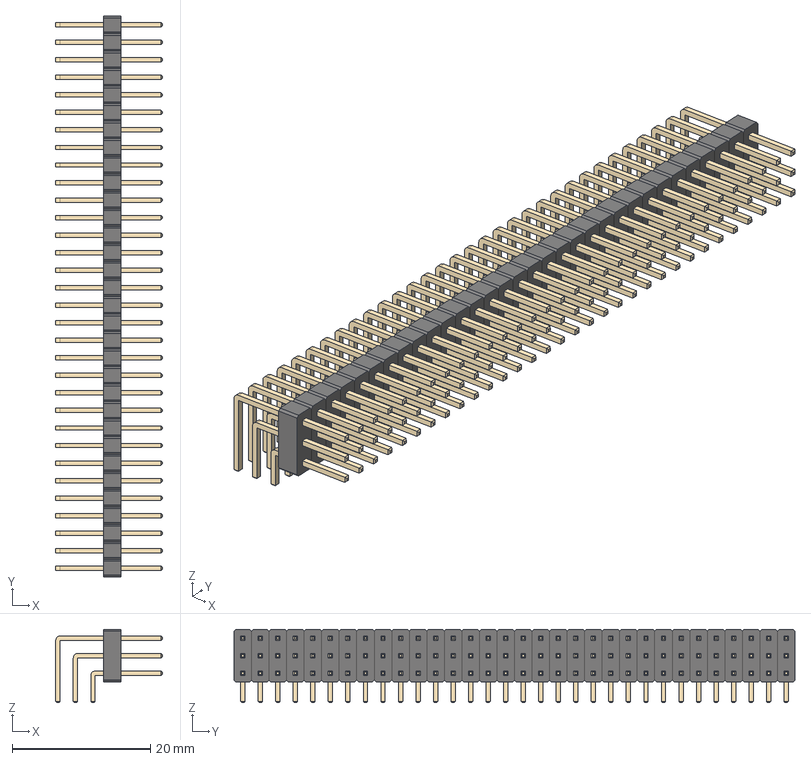
[picture p241: CAD file, 2023-11-28]
CAD/STEP Templates/PinHeader_3x32_P2.54mm_Horizontal.step
15.4 x 81.3 x 10.6 mm
