impatrq/aeroalert/CAD/STEP Templates/PinHeader_3x21_P2.54mm_Horizontal.step

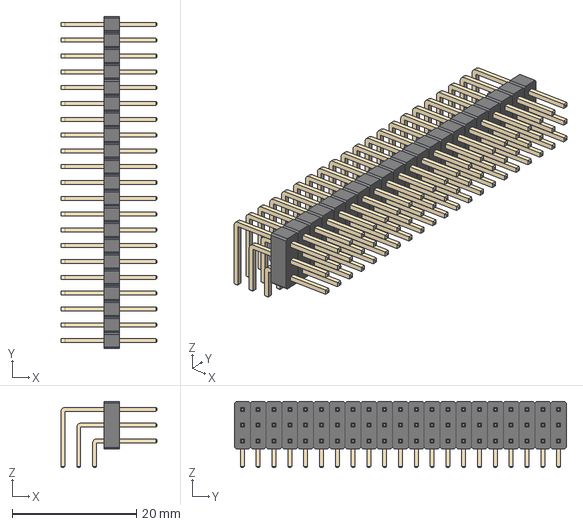
[picture p242: CAD file, 2023-11-28]
CAD/STEP Templates/PinHeader_3x21_P2.54mm_Horizontal.step
15.4 x 53.3 x 10.6 mm
