impatrq/aeroalert/CAD/STEP Templates/H254_90deg_6pin.STEP

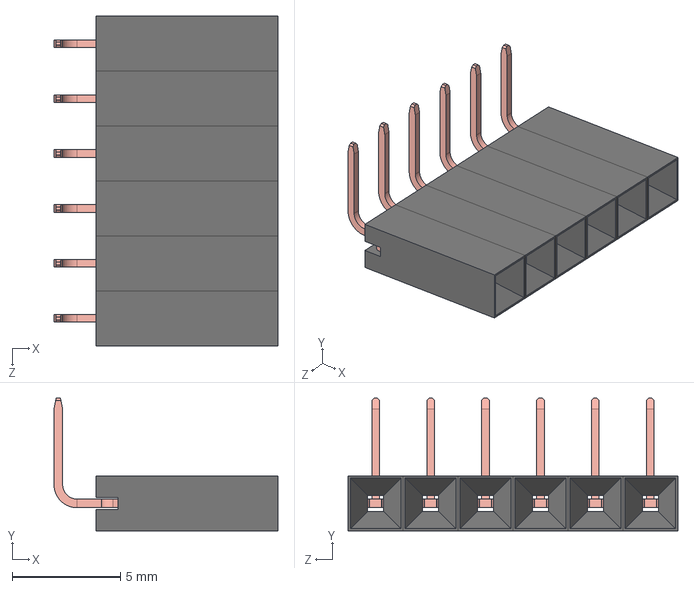
[picture p243: CAD file, 2023-11-28]
CAD/STEP Templates/H254_90deg_6pin.STEP
10.4 x 6.14 x 15.2 mm
frame_H254 x 6
pin-90deg x 6
