impatrq/aeroalert/CAD/STEP Templates/H254_90deg_4pin.STEP

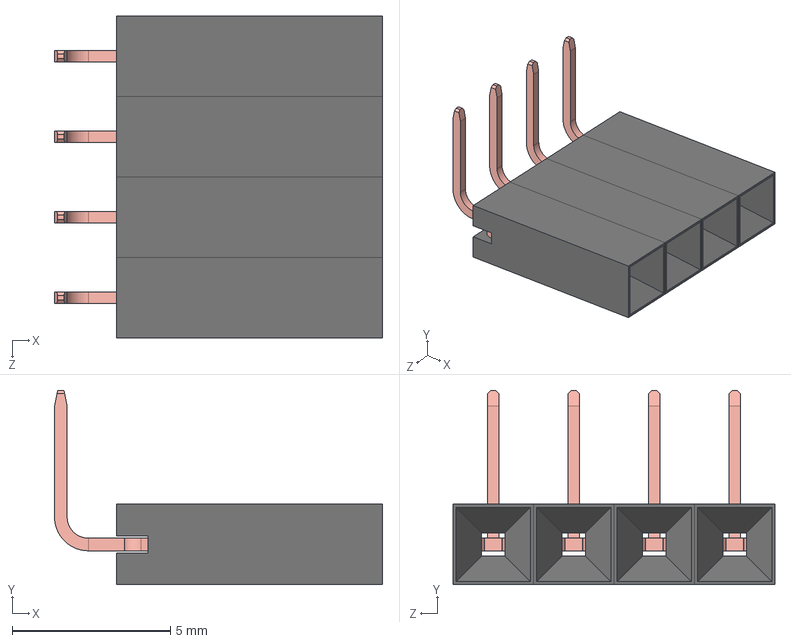
[picture p244: CAD file, 2023-11-28]
CAD/STEP Templates/H254_90deg_4pin.STEP
10.4 x 6.14 x 10.2 mm
frame_H254 x 4
pin-90deg x 4
