impatrq/aeroalert/CAD/STEP Templates/16-Pin Header - Male - 2.54mm.step

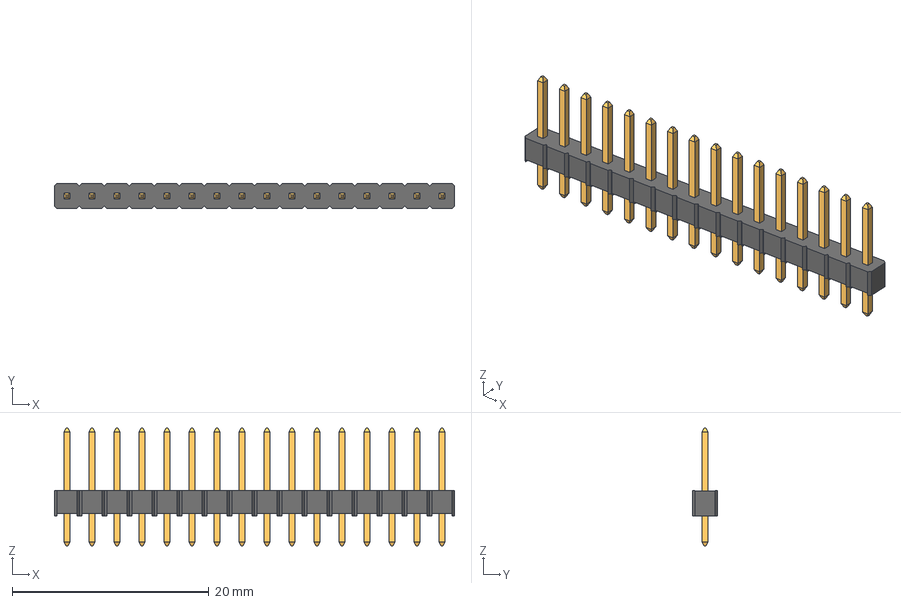
[picture p245: CAD file, 2023-11-28]
CAD/STEP Templates/16-Pin Header - Male - 2.54mm.step
40.6 x 2.54 x 11.9 mm
