impatrq/aeroalert/CAD/STEP Templates/PinHeader_3x16_P2.54mm_Horizontal.step

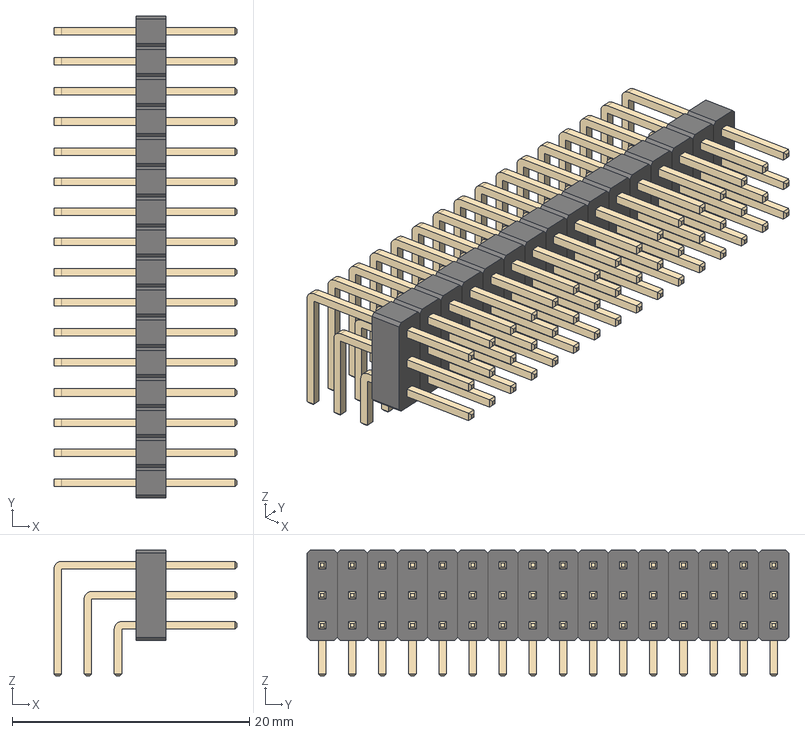
[picture p246: CAD file, 2023-11-28]
CAD/STEP Templates/PinHeader_3x16_P2.54mm_Horizontal.step
15.4 x 40.6 x 10.6 mm
