impatrq/aeroalert/CAD/STEP Templates/14-Pin Header - Female - 2.54mm.step

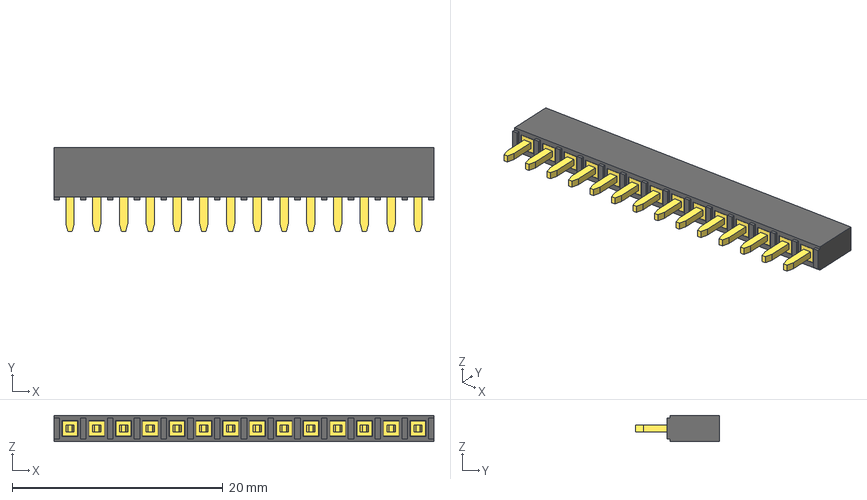
[picture p247: CAD file, 2023-11-28]
CAD/STEP Templates/14-Pin Header - Female - 2.54mm.step
36.1 x 8.00 x 2.50 mm
