impatrq/aeroalert/CAD/AES/AES - Assembly.png

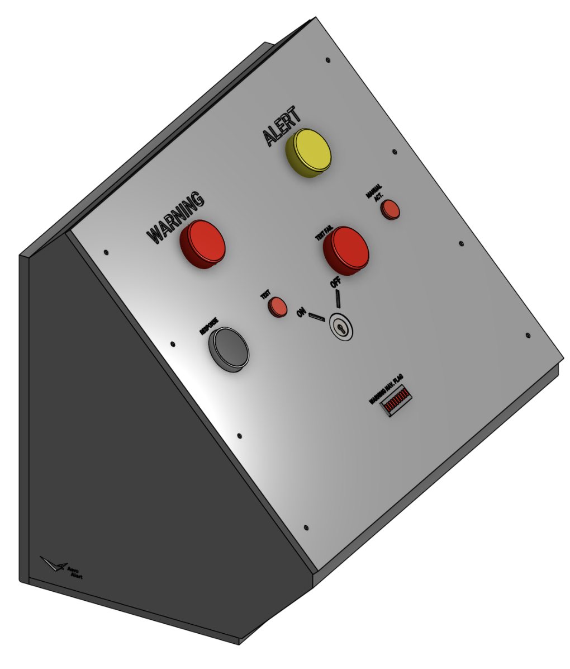
CAD/AES/AES - Assembly.png
