impatrq/aeroalert/CAD/CTRT/CTRT - Assembly.png

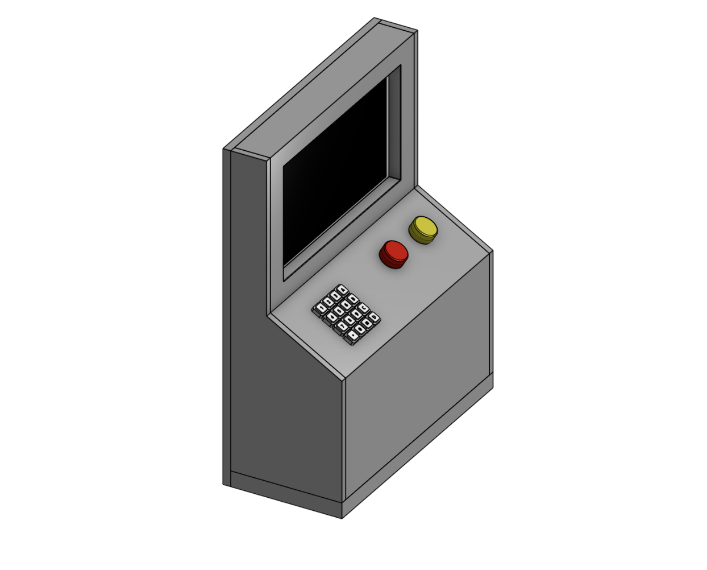
CAD/CTRT/CTRT - Assembly.png
