impatrq/aeroalert/CAD/STEP Templates/10-segment-linear-display-1/Renders/10 segment display.png

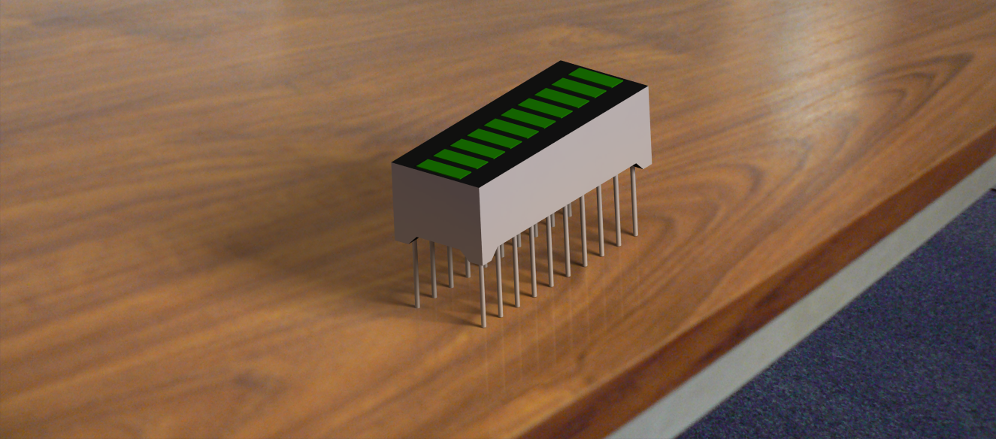
CAD/STEP Templates/10-segment-linear-display-1/Renders/10 segment display.png
