impatrq/aeroalert/CAD/STEP Templates/20230511_121501.jpg

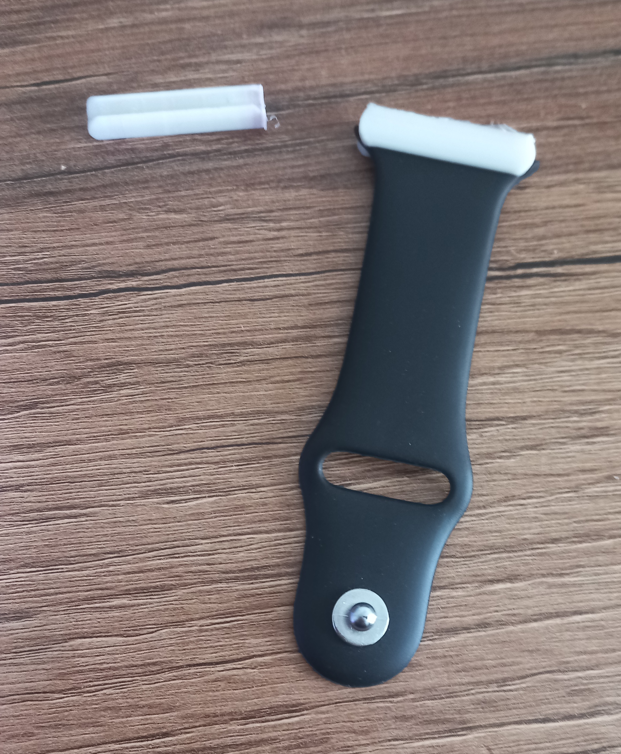
CAD/STEP Templates/20230511_121501.jpg
