impatrq/aeroalert/CAD/STEP Templates/Decals/Battery Label 3.7v.png

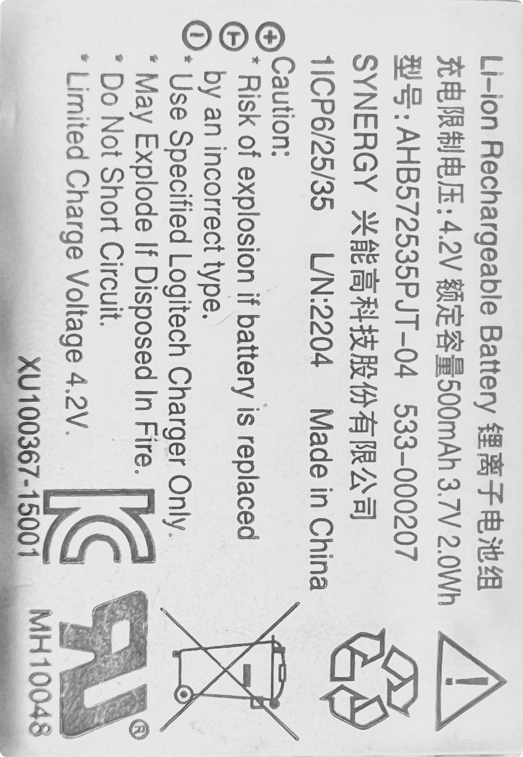
CAD/STEP Templates/Decals/Battery Label 3.7v.png
