impatrq/aeroalert/CAD/STEP Templates/DIP_switch_prev.png

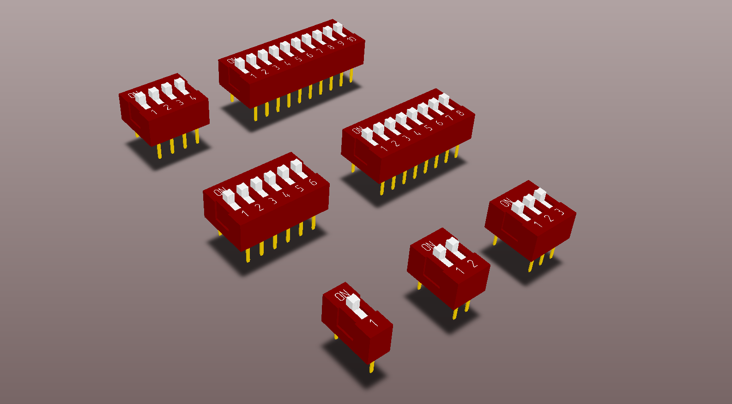
CAD/STEP Templates/DIP_switch_prev.png
