impatrq/aeroalert/CAD/STEP Templates/esp32_adapter_board.JPG

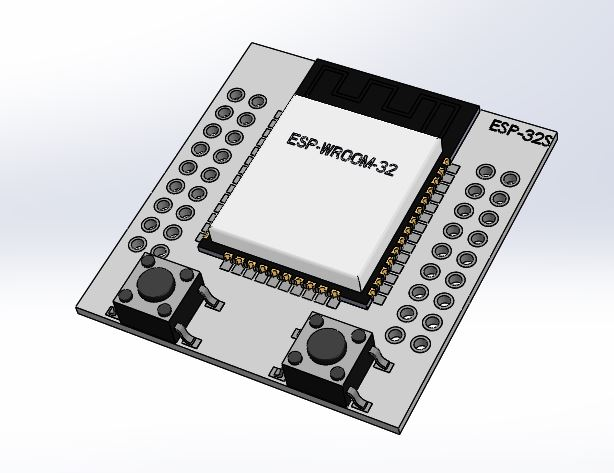
CAD/STEP Templates/esp32_adapter_board.JPG
