impatrq/aeroalert/CAD/STEP Templates/keyboard-4x4-1/Untitled.JPG

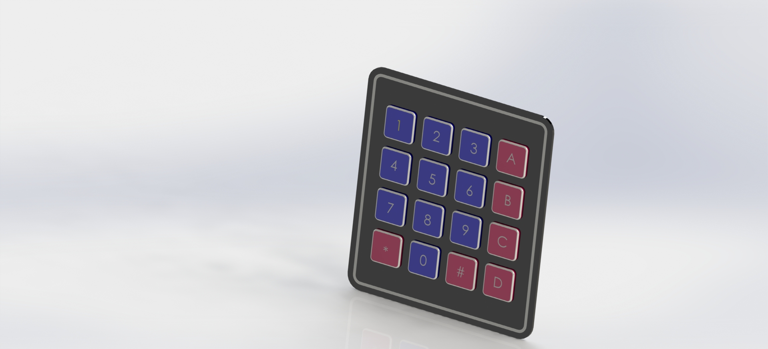
CAD/STEP Templates/keyboard-4x4-1/Untitled.JPG
