impatrq/aeroalert/CAD/STEP Templates/keylock-switch-adp16k4-1/Key Switch ADP16K4-ATO-1A.png

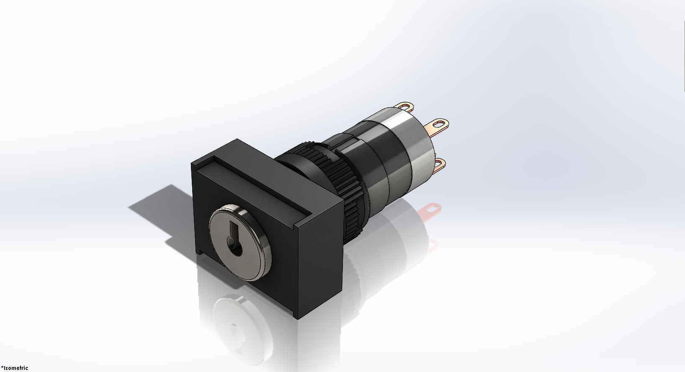
CAD/STEP Templates/keylock-switch-adp16k4-1/Key Switch ADP16K4-ATO-1A.png
