impatrq/aeroalert/CAD/STEP Templates/LED bar.JPG

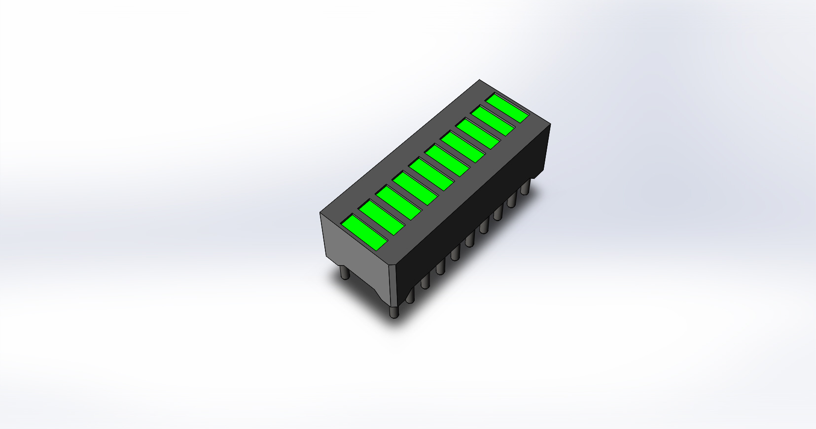
CAD/STEP Templates/LED bar.JPG
