impatrq/aeroalert/CAD/STEP Templates/led-pushbutton-1/LED Pushbutton.png

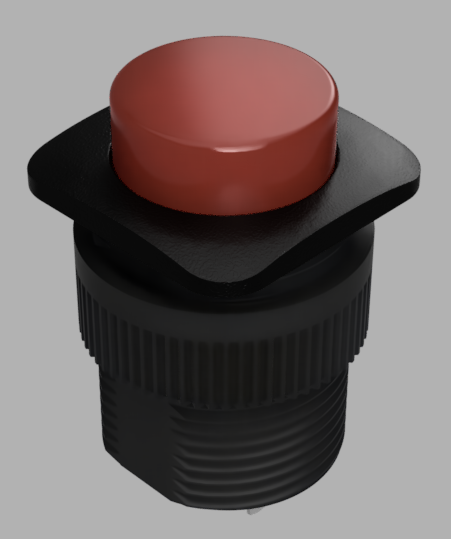
CAD/STEP Templates/led-pushbutton-1/LED Pushbutton.png
