impatrq/aeroalert/CAD/STEP Templates/mini-toggle-switches-1/Set.png

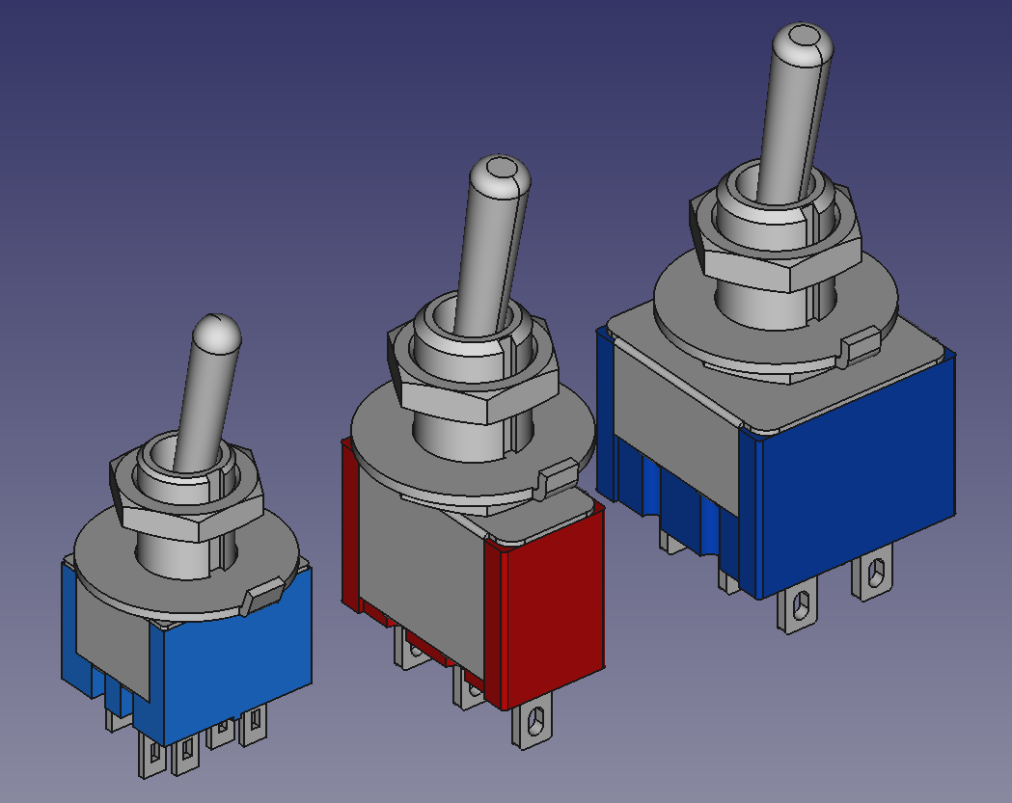
CAD/STEP Templates/mini-toggle-switches-1/Set.png
