impatrq/aeroalert/CAD/STEP Templates/panel-light-indicator-_-red-1/red.JPG

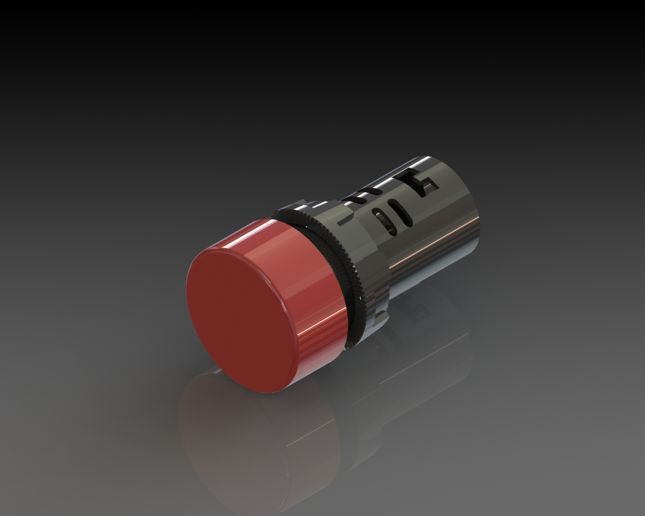
CAD/STEP Templates/panel-light-indicator-_-red-1/red.JPG
