impatrq/aeroalert/CAD/STEP Templates/panel-light-indicator-_-yellow-1/yellow.JPG

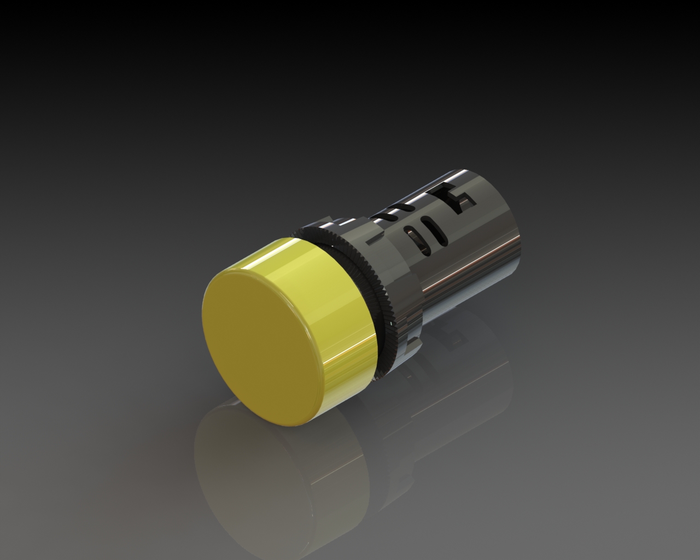
CAD/STEP Templates/panel-light-indicator-_-yellow-1/yellow.JPG
