impatrq/aeroalert/CAD/STEP Templates/Pin_Header-Male-2.54mm.png

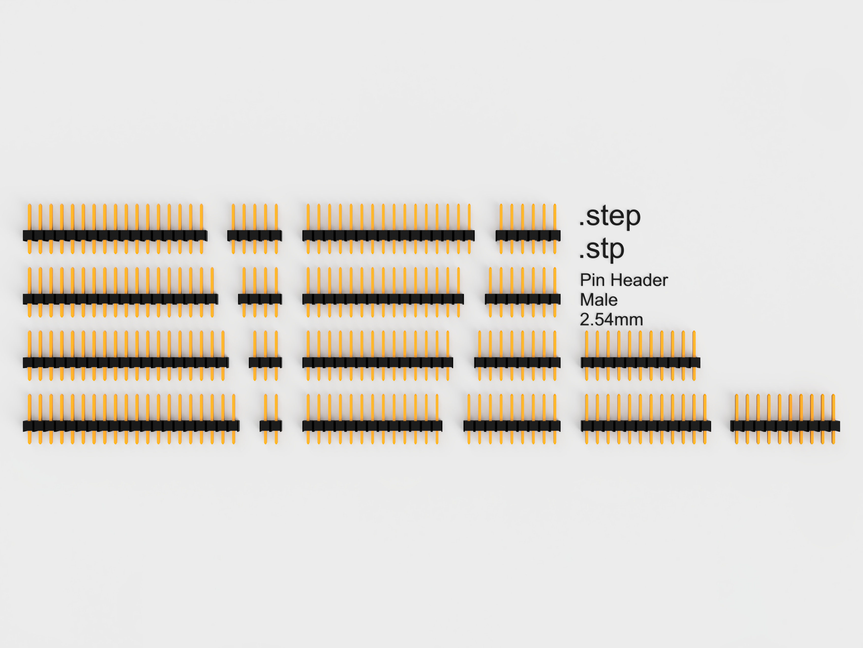
CAD/STEP Templates/Pin_Header-Male-2.54mm.png
