impatrq/aeroalert/CAD/STEP Templates/Redy to render.jpg

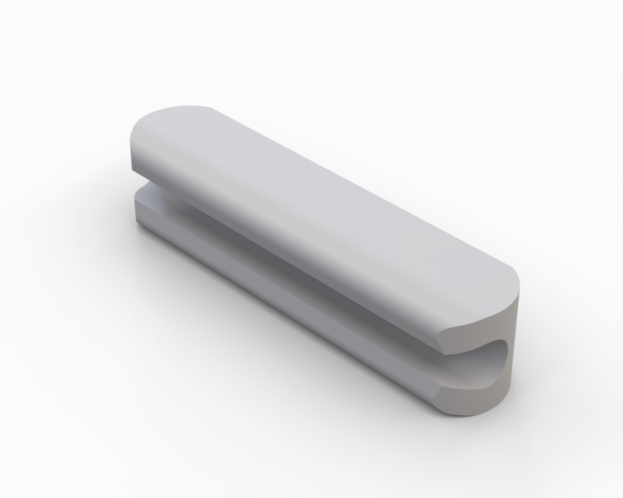
CAD/STEP Templates/Redy to render.jpg
