impatrq/aeroalert/CAD/STEP Templates/RENDER SENSOR PULSO.jpg

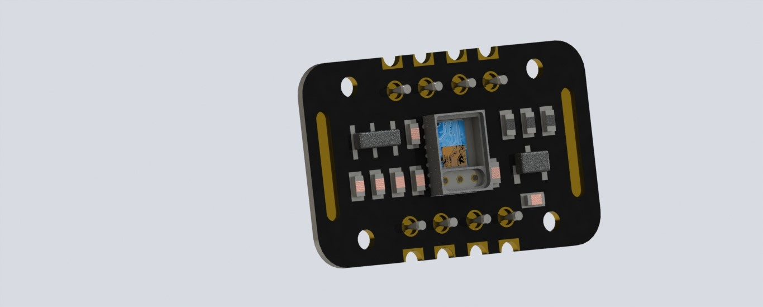
CAD/STEP Templates/RENDER SENSOR PULSO.jpg
