impatrq/aeroalert/CAD/STEP Templates/Rendering/DC-DC Boost Converter MT3608 3DView.jpg

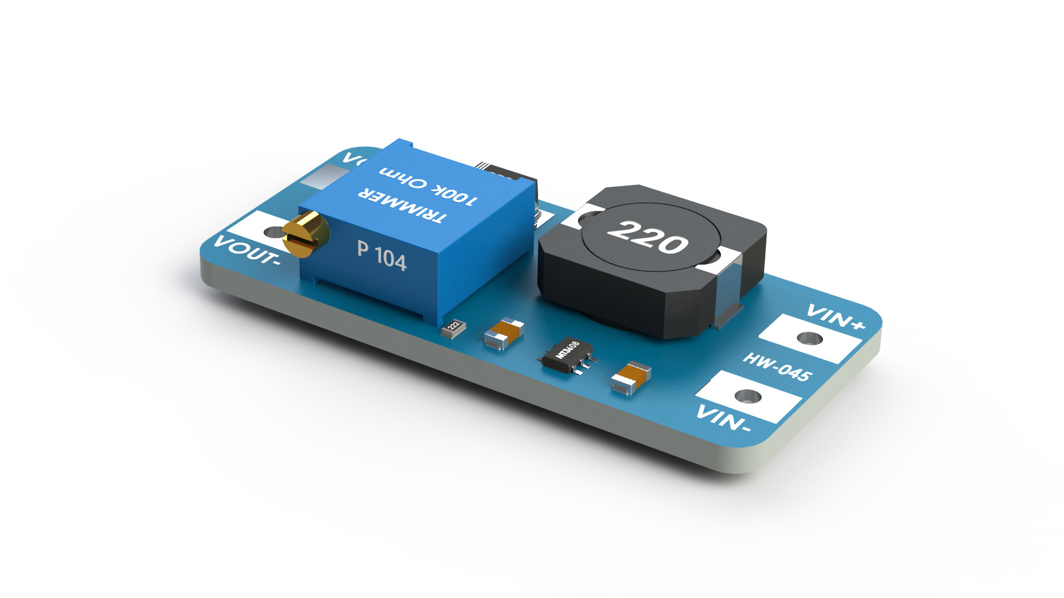
CAD/STEP Templates/Rendering/DC-DC Boost Converter MT3608 3DView.jpg
