impatrq/aeroalert/CAD/STEP Templates/Rendering/Fuse.jpg

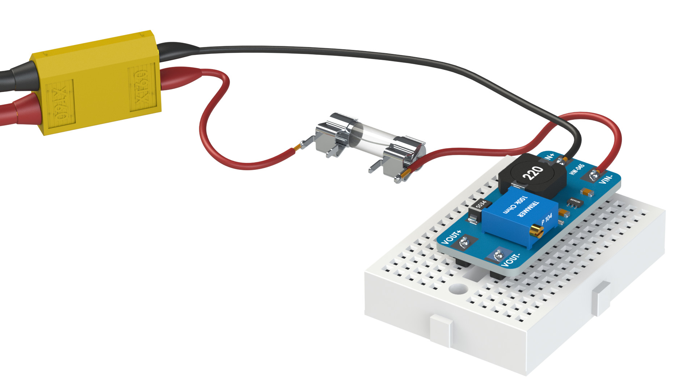
CAD/STEP Templates/Rendering/Fuse.jpg
