impatrq/aeroalert/CAD/STEP Templates/Rendering/Wiring.jpg

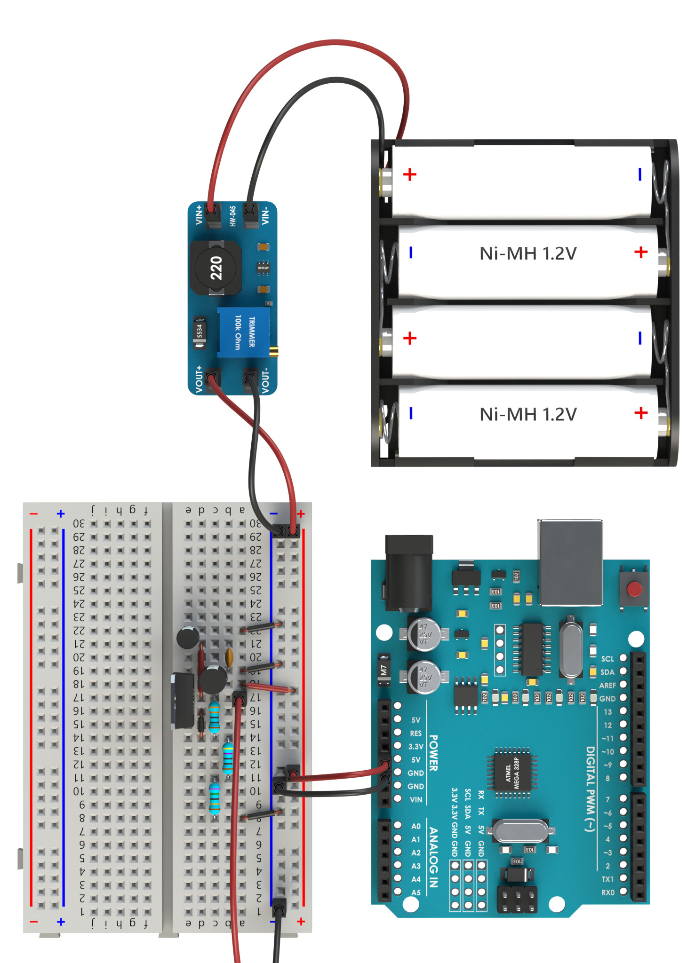
CAD/STEP Templates/Rendering/Wiring.jpg
