impatrq/aeroalert/CAD/STEP Templates/Renderings/LED bar render blue.JPG

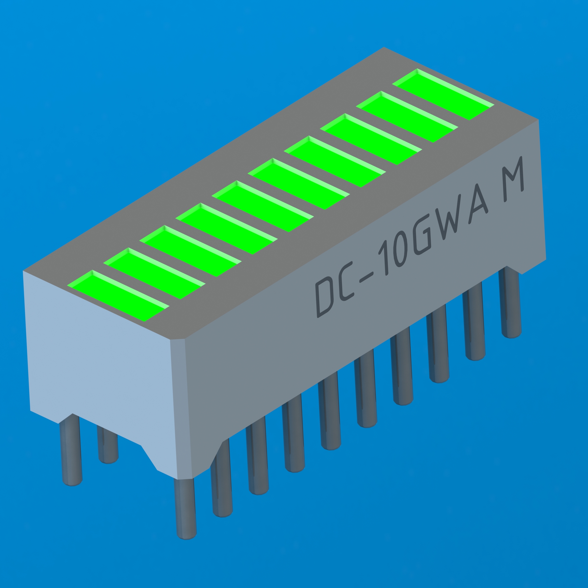
CAD/STEP Templates/Renderings/LED bar render blue.JPG
