impatrq/aeroalert/CAD/STEP Templates/Renderings/LED bar render.JPG

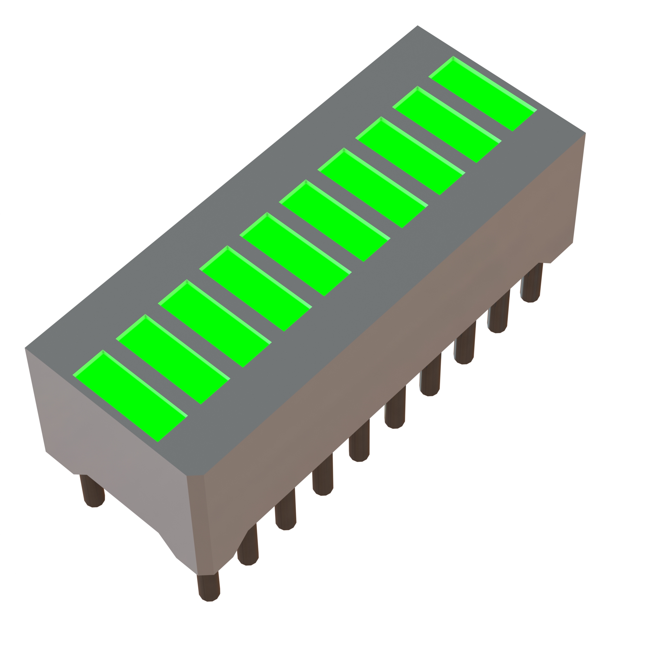
CAD/STEP Templates/Renderings/LED bar render.JPG
