impatrq/aeroalert/CAD/STEP Templates/Renders/Battery 2.png

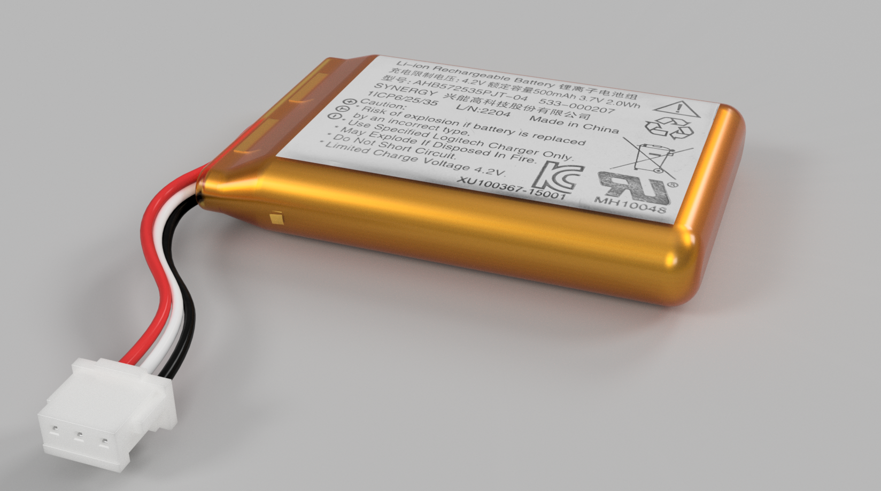
CAD/STEP Templates/Renders/Battery 2.png
