impatrq/aeroalert/CAD/STEP Templates/start-button-botao-pulsador-1/START BUTTON 1.png

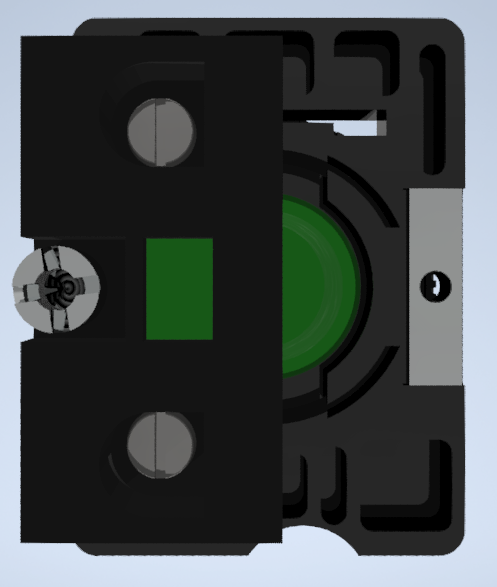
CAD/STEP Templates/start-button-botao-pulsador-1/START BUTTON 1.png
