impatrq/aeroalert/CAD/STEP Templates/TP4056 render_1.png

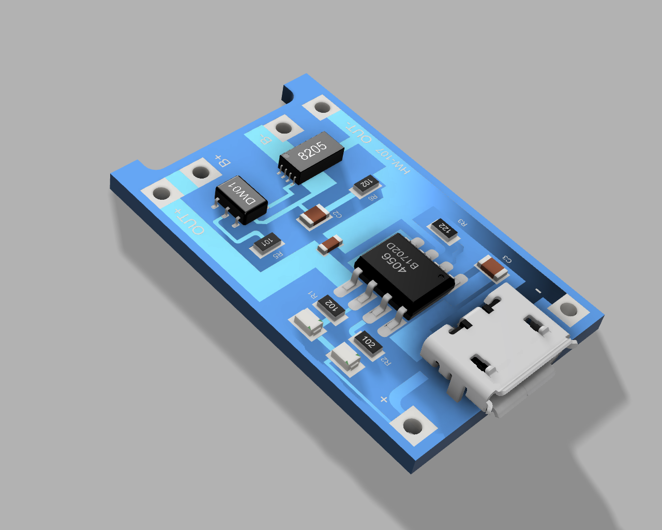
CAD/STEP Templates/TP4056 render_1.png
