impatrq/aeroalert/CAD/STEP Templates/TP4056 render_2.png

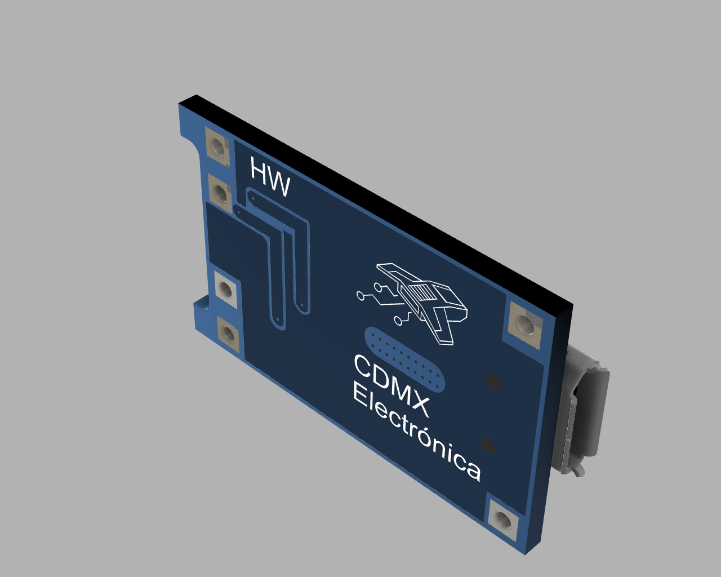
CAD/STEP Templates/TP4056 render_2.png
