impatrq/aeroalert/CAD/STEP Templates/TP4056 v56.png

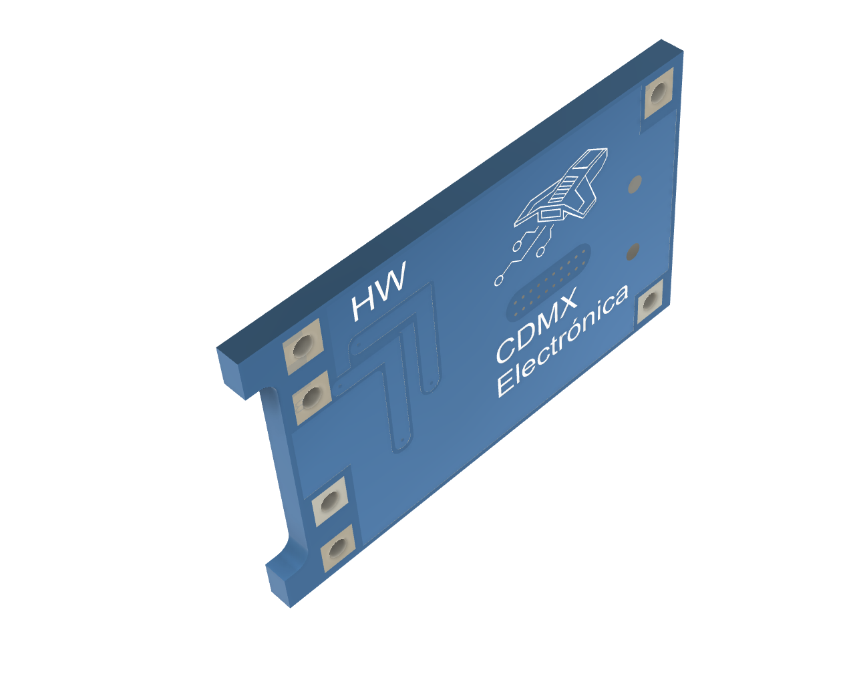
CAD/STEP Templates/TP4056 v56.png
