impatrq/aeroalert/CAD/STEP Templates/TP4056 v57.png

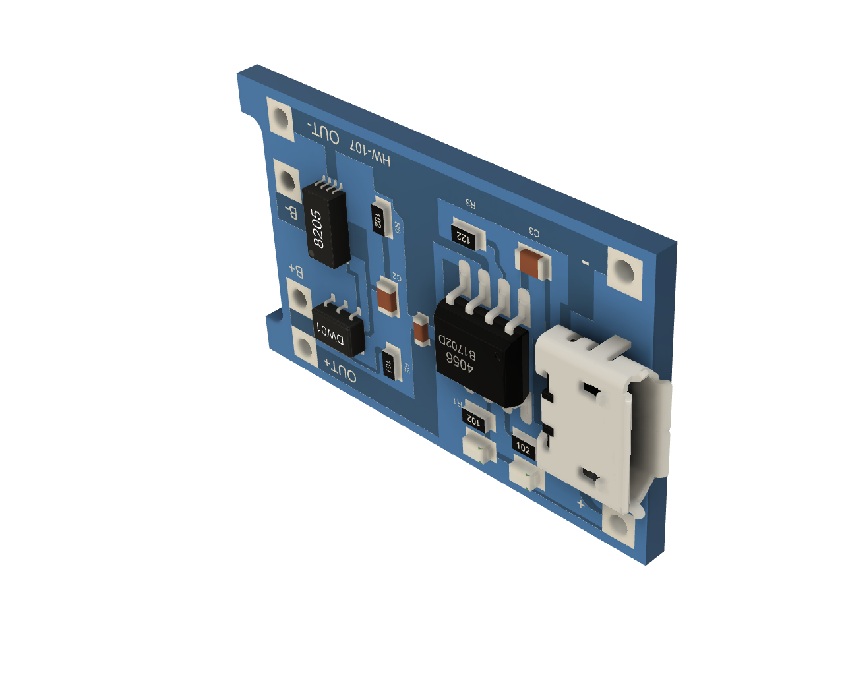
CAD/STEP Templates/TP4056 v57.png
