impatrq/aeroalert/CAD/STEP Templates/TP4056 v_.png

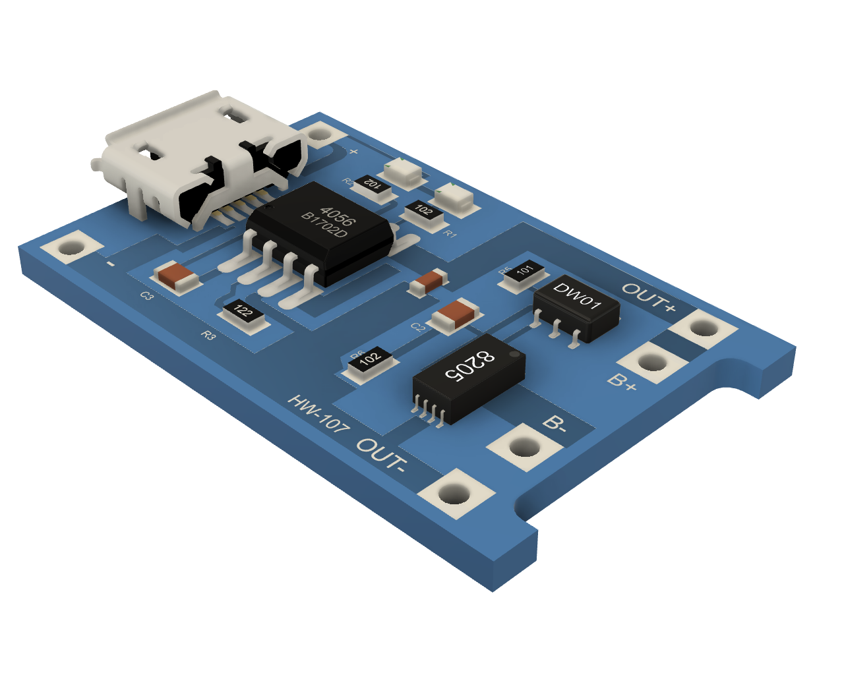
CAD/STEP Templates/TP4056 v_.png
