impatrq/aeroalert/CAD/VDB/VDB - Assembly.png

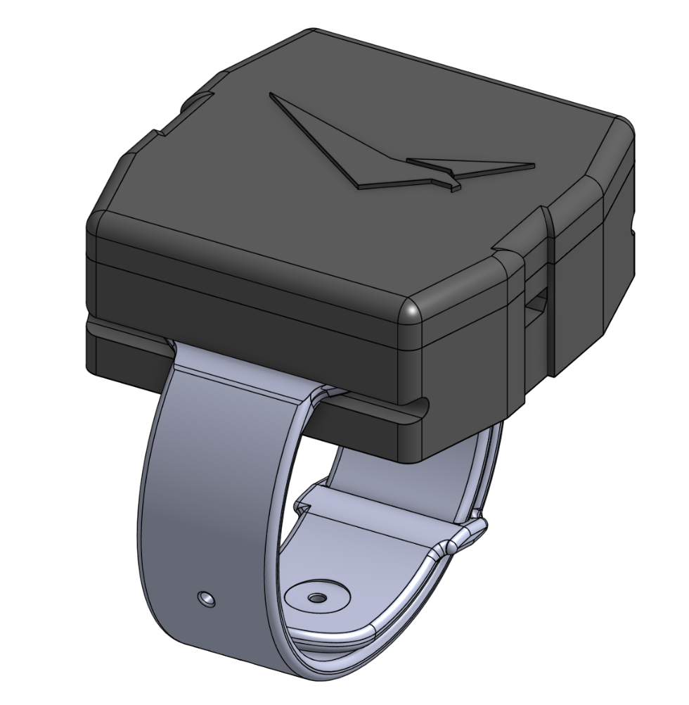
CAD/VDB/VDB - Assembly.png
