impatrq/aeroalert/Documentación/Documentos Administrativos/ONIET/Certificados de participación/Mateo Gastón Husulak Ledo.pdf

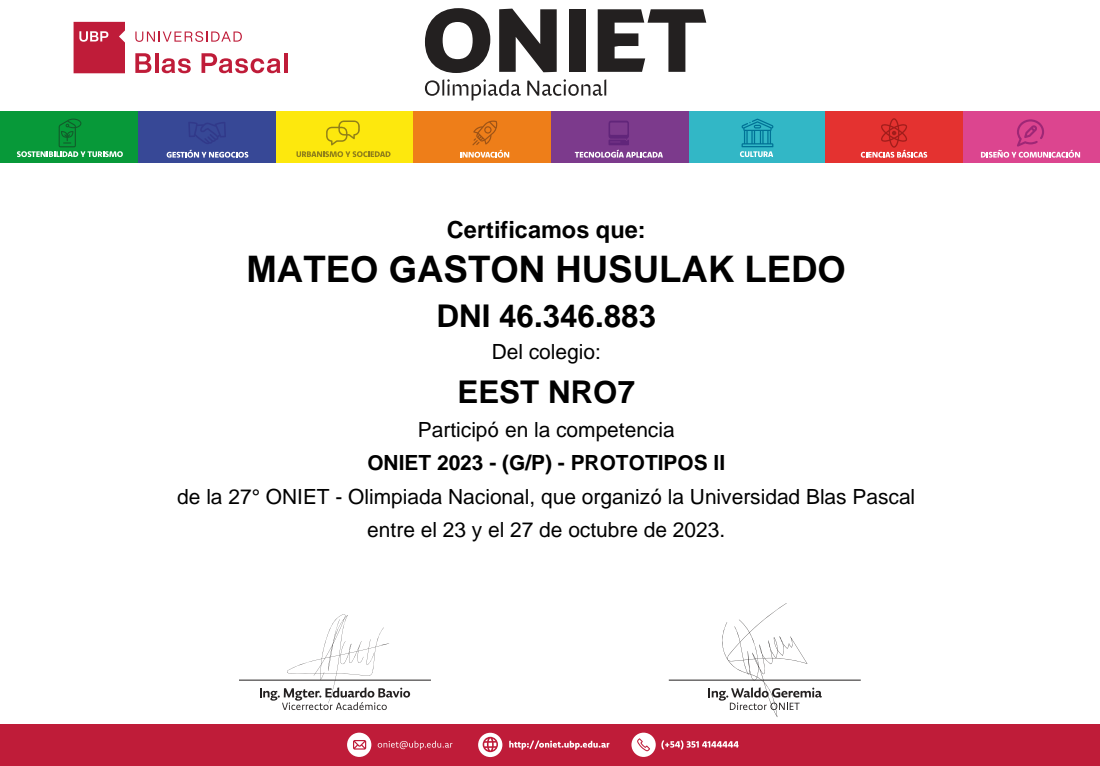
[picture p314: page 1]
Certificamos que:

MATEO GASTON HUSULAK LEDO

DNI 46.346.883
Del colegio:
EEST NRO7
Participó en la competencia
ONIET 2023 - (G/P) - PROTOTIPOS II

de la 27° ONIET - Olimpiada Nacional, que organizó la Universidad Blas Pascal

entre el 23 y el 27 de octubre de 2023.
