impatrq/aeroalert/CAD/AES/AES - Blueprint.pdf

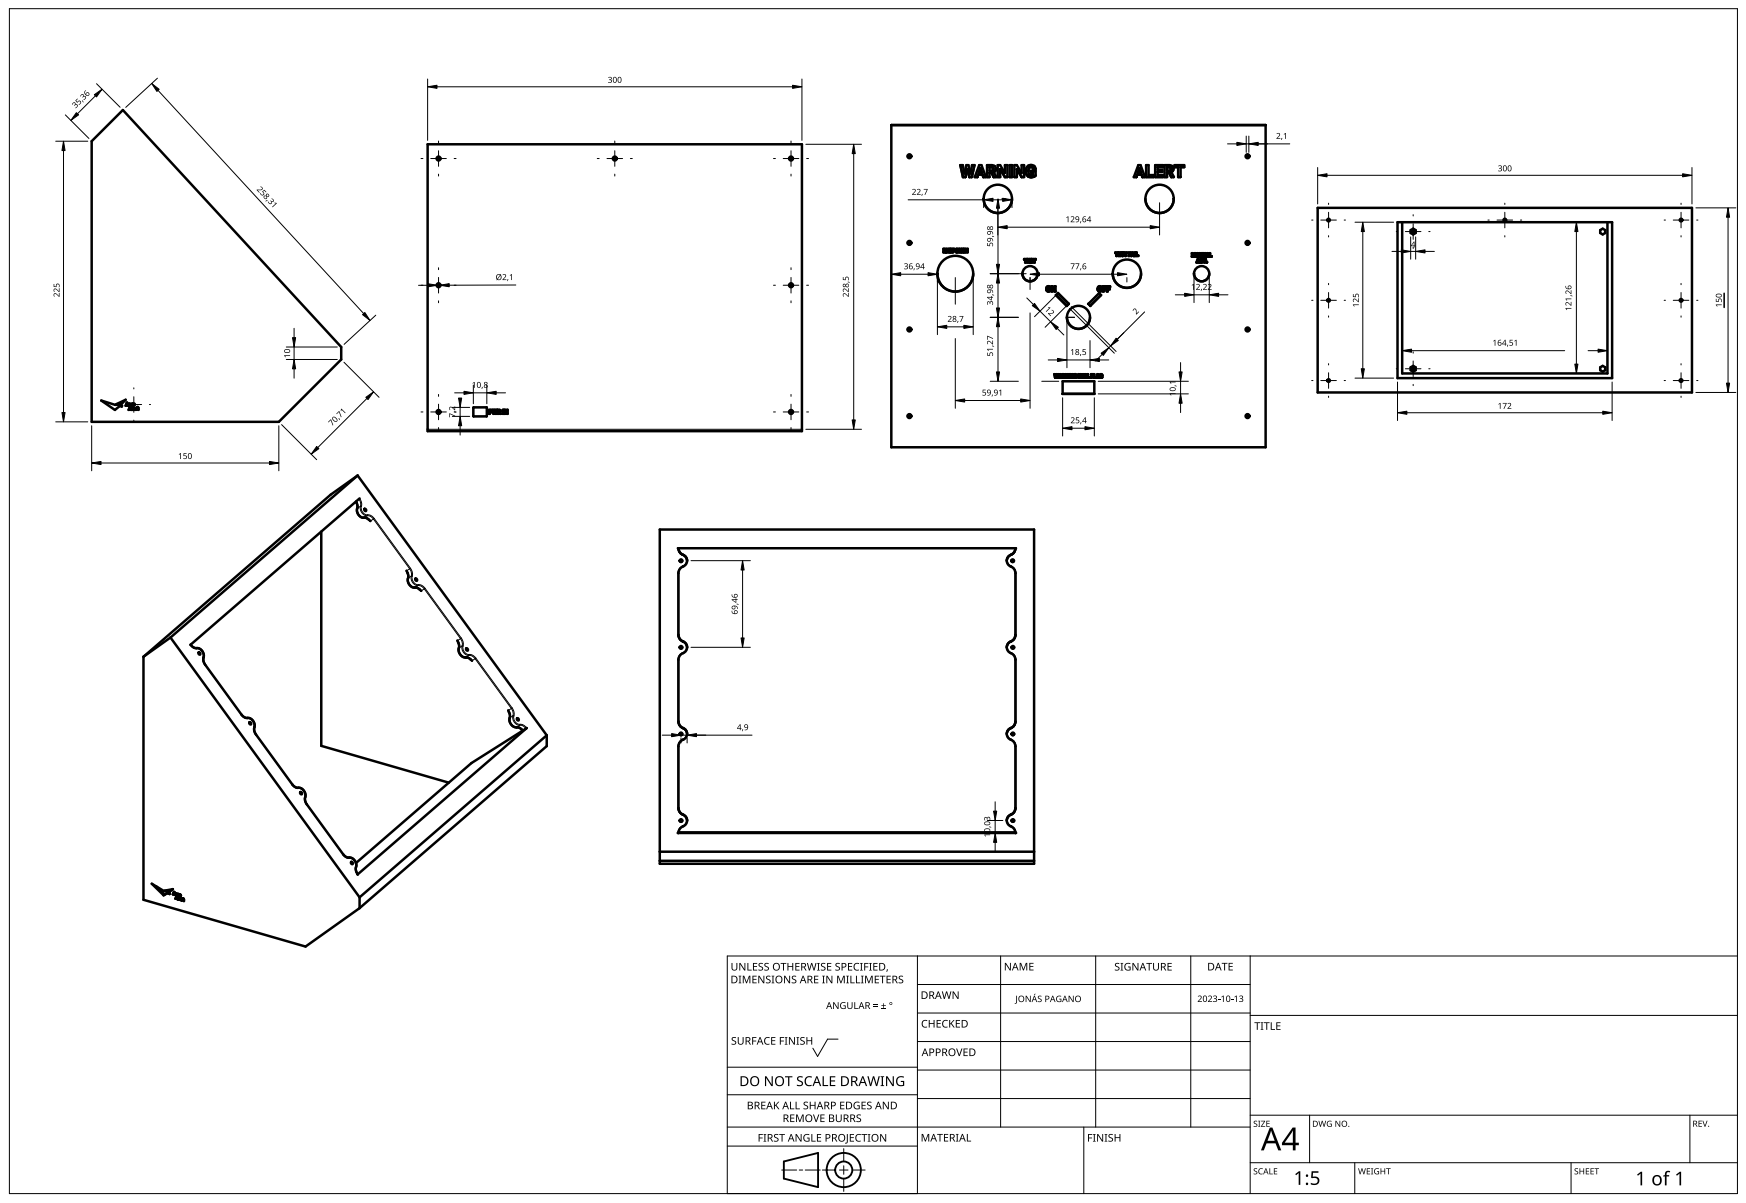
[picture p320: page 1]
