impatrq/aeroalert/CAD/CTRT/CTRT - Blueprint.pdf

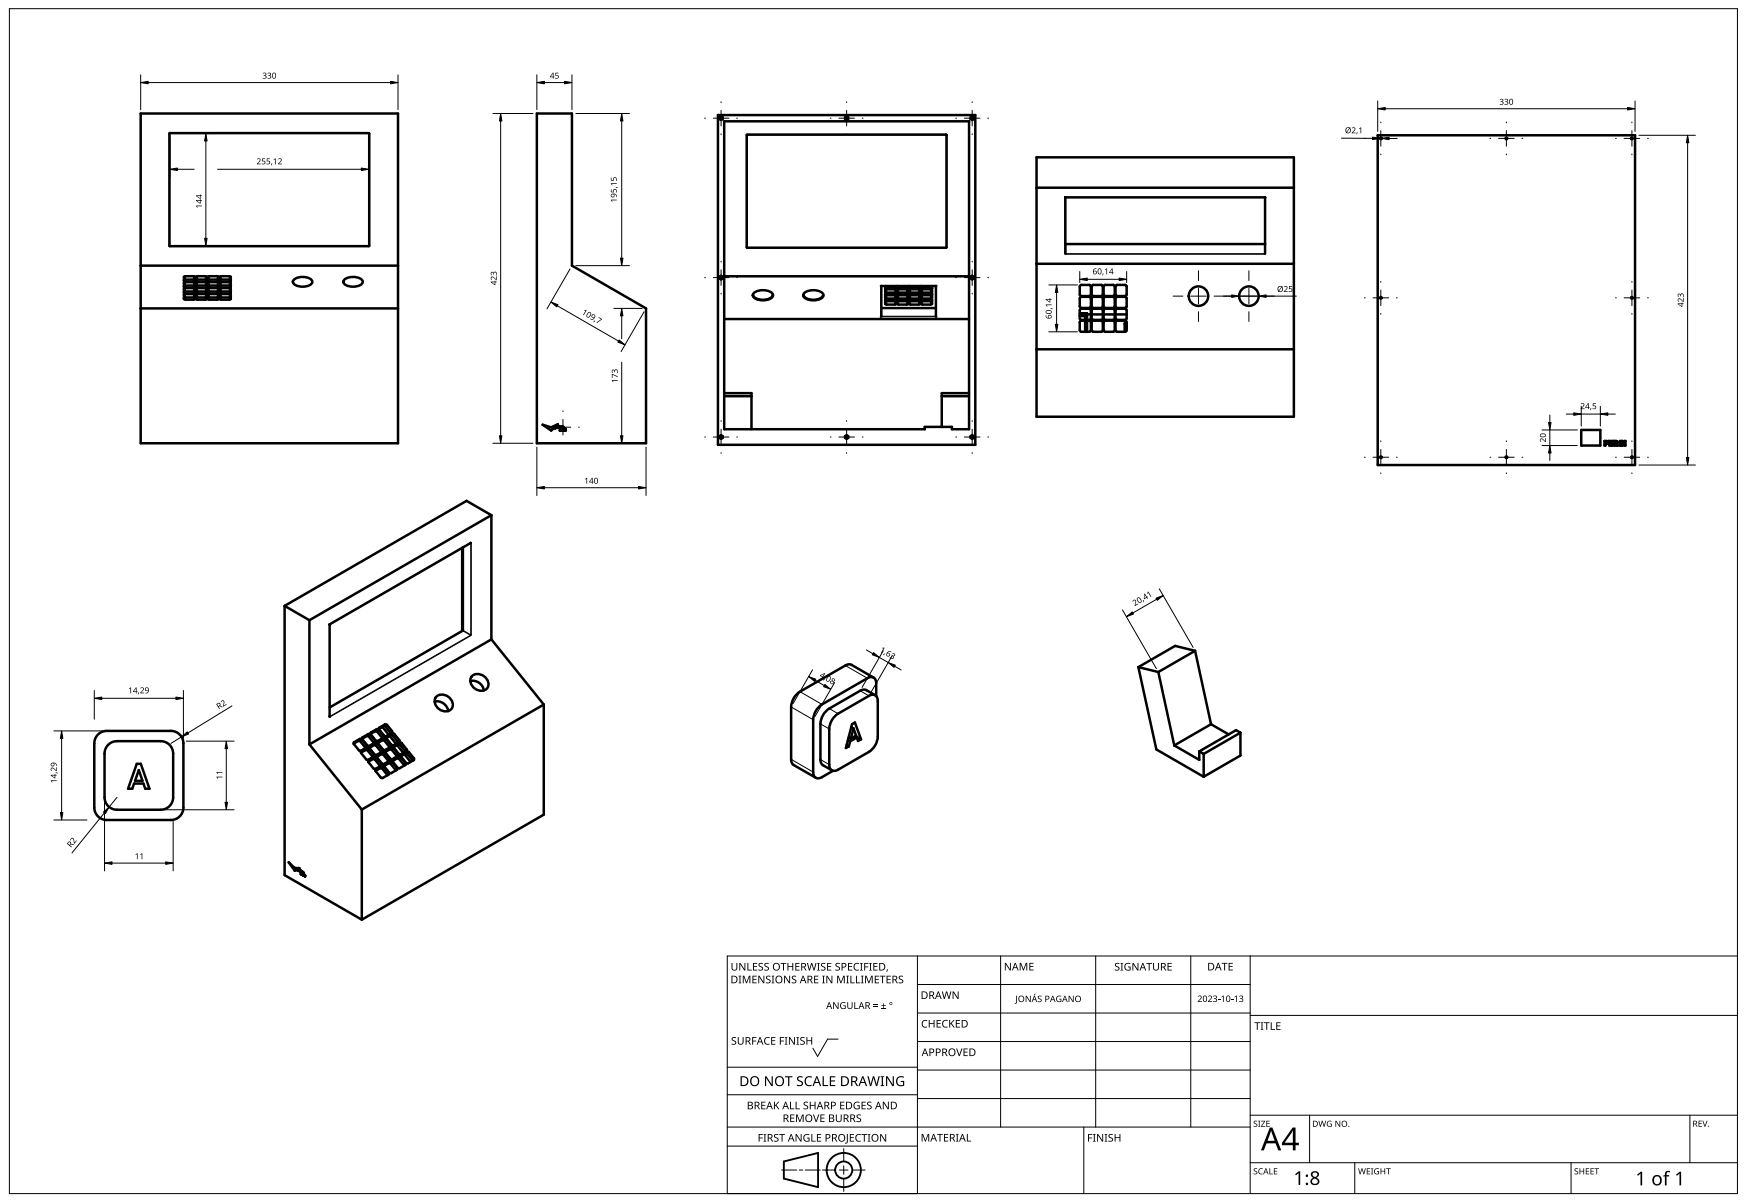
[picture p321: page 1]
