impatrq/aeroalert/CAD/CTRT/CTRT Internal Faces - Blueprint.pdf

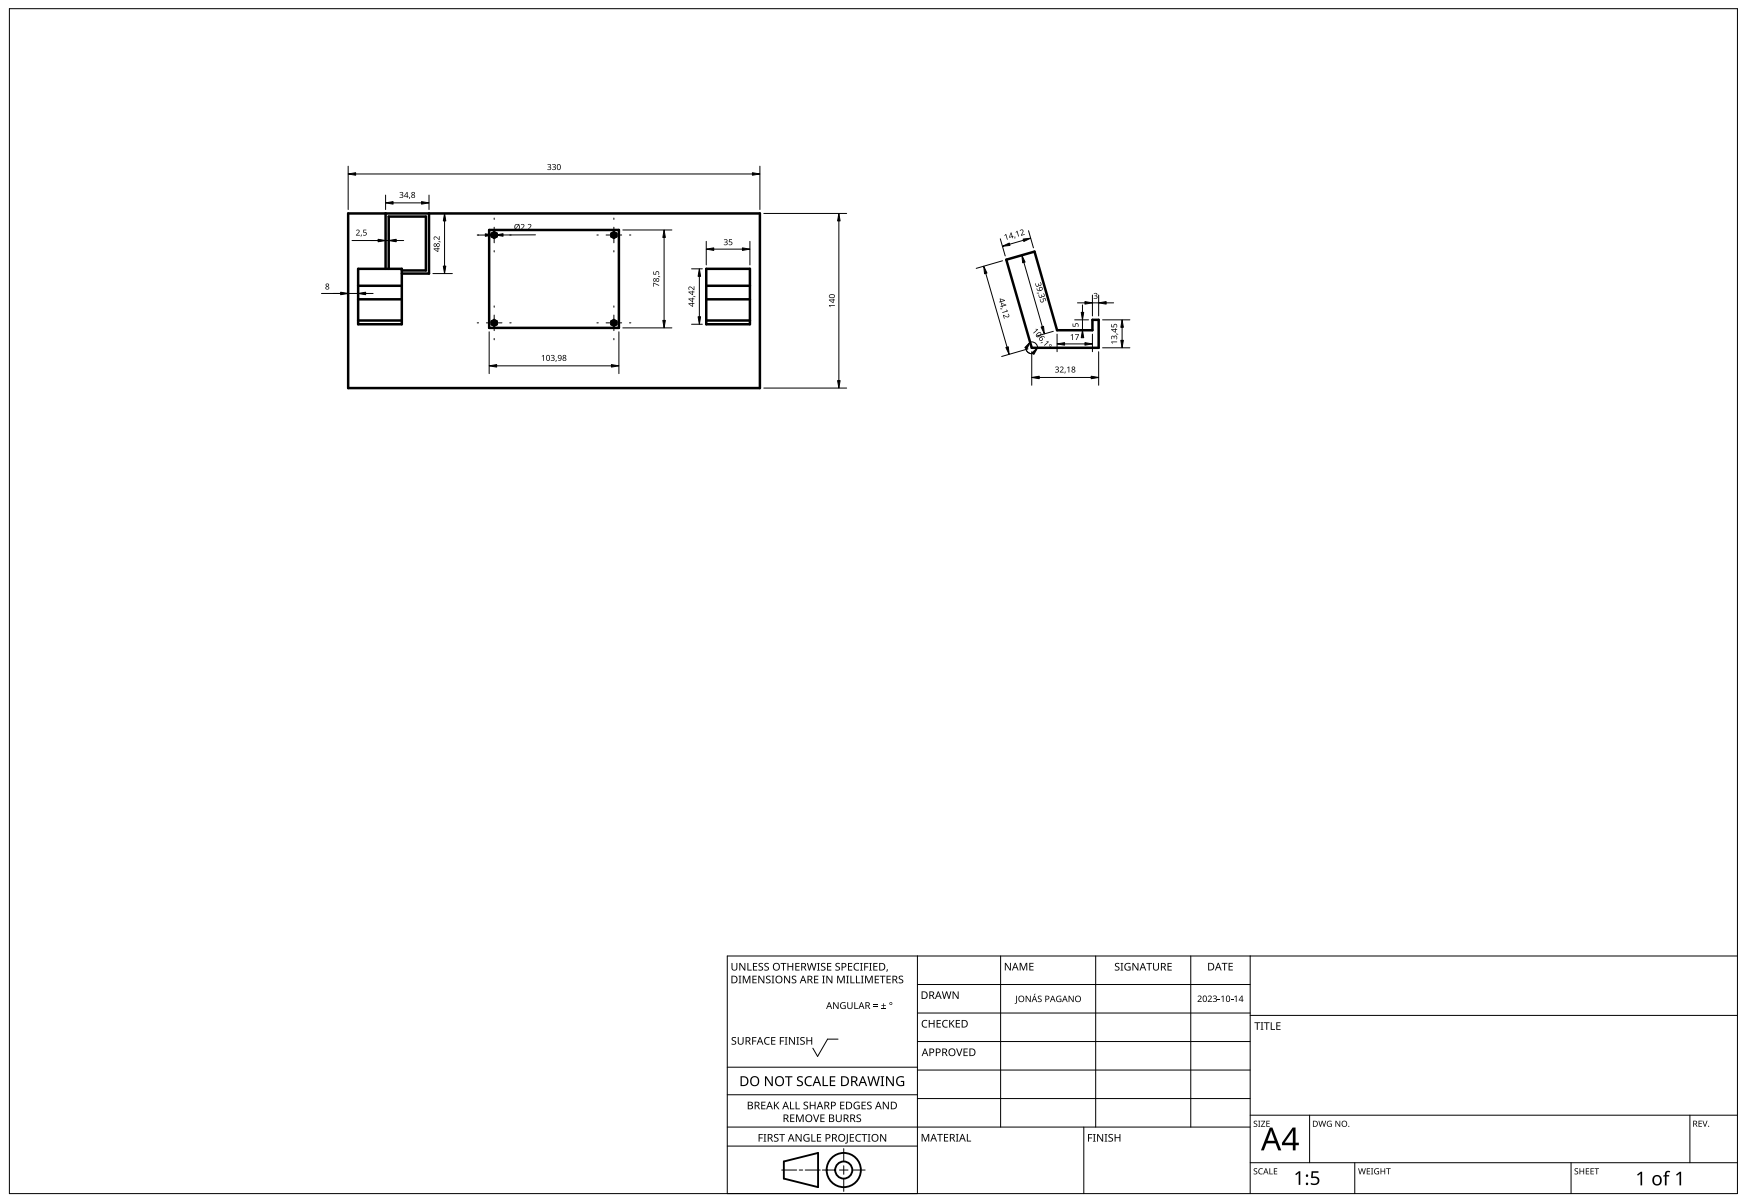
[picture p322: page 1]
