impatrq/aeroalert/CAD/VDB/VDB - Blueprint.pdf

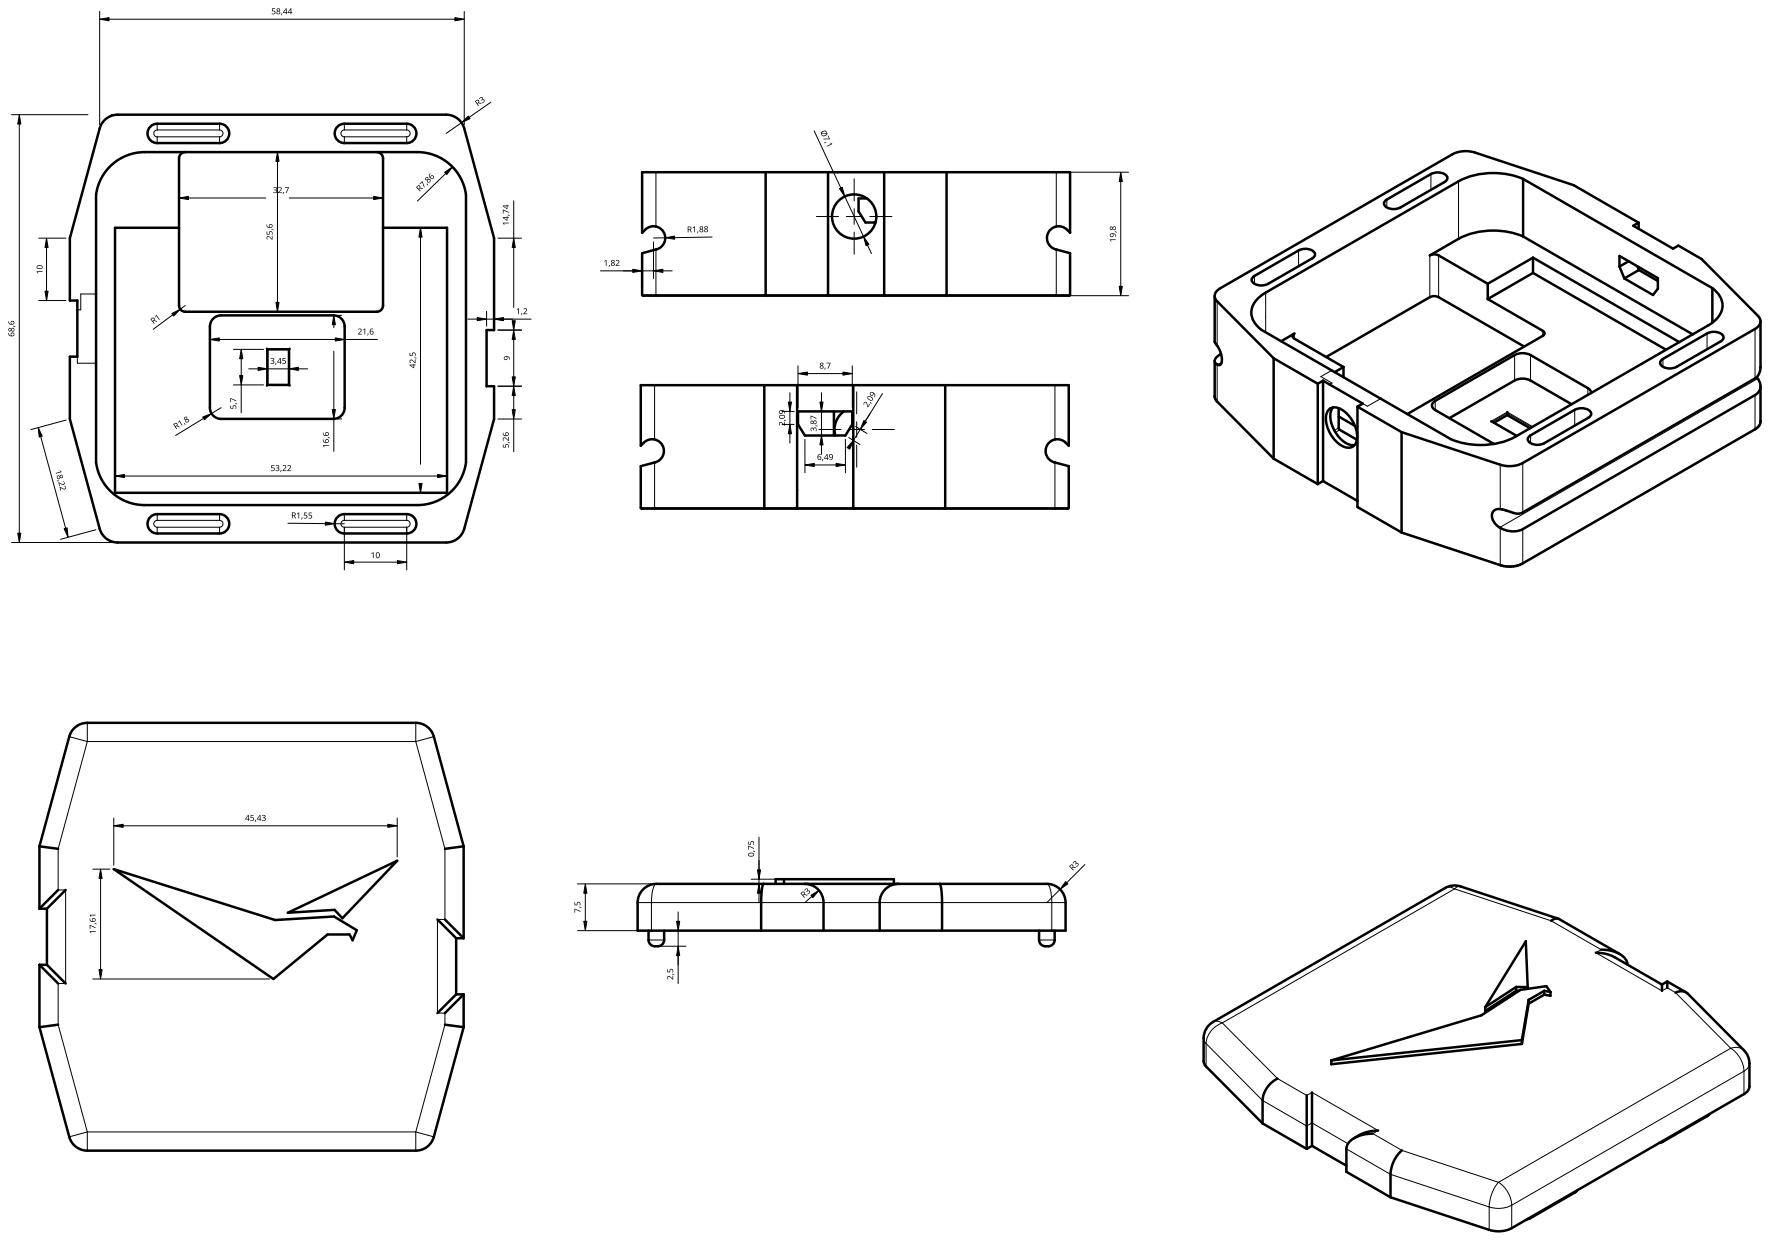
[picture p323: page 1]
