impatrq/aeroalert/AES-CTRT-VDB_programs/SAE/accesssv6.py

try:
    import usocket as socket
except:
    import socket
import network
import esp, gc
esp.osdebug(None)
gc.collect()
import random, json, time
from machine import Timer
import machine
from wifi_connection import connect_wifi

s = connect_wifi()

listabpm = []
listaspo = []
bpm_bajos1 = bpm_altos1 = spo_bajos1 = dormido1 = temp_baja1 = temp_alta1 = 0 
bpm_bajos2 = 0# pin
bpm_altos2 = 0# pin
spo_bajos2= 0# pin
dormido2 =   0# pin
temp_baja2 = 0# pin
temp_alta2 = 0# pin
tomar_control = 0

station1, addr1 = s.accept()
print('Conexión establecida con el ESP32 como estación 1(rtdc):', addr1)

#station2, addr2 = s.accept()
#print('Conexión establecida con el ESP32 como estación 2(band):', addr2)

station3 = 3 # la pulsera del copiloto

def recibir_band1(estacion2):
    while True:
        message2 = estacion2.recv(1024)
        print(message2.decode('utf-8'))
        evaluar_info(message2)
        

def recibir_rtdc(estacion1):
    while True: 
        message1 = estacion1.recv(1024)
        print('Datos recibidos:', message1.decode('utf-8'))
        
def enviar_rtdc(rtdc):
    global bpm_bajos1, bpm_altos1, spo_bajos1, dormido1, temp_baja1, temp_alta1
    global bpm_bajos2, bpm_altos2, spo_bajos2, dormido2, temp_baja2, temp_alta2
    global tomar_control
    global codigo
    while True:
        codigo = [bpm_altos1,bpm_altos2, bpm_bajos1,bpm_bajos2, dormido1,dormido2,
                   spo_bajos1,spo_bajos2, tomar_control]
        codigo_enviar = json.dumps(codigo).encode('utf-8')
        print(codigo)
        #rtdc.send(codigo_enviar)
        time.sleep(10)

# Configurar los pines de la luz y el botón
pin_luz_amarilla = machine.Pin(5, machine.Pin.OUT)
pin_reaccion = machine.Pin(4, machine.Pin.IN)
pin_boton_reaccion = pin_reaccion
pin_luz_alarma = machine.Pin(6, machine.Pin.OUT)
pin_luz_dormido = machine.Pin(7, machine.Pin.OUT)
pin_luz_roja = machine.Pin(8, machine.Pin.OUT)

pasaron_30segs_spo = pasaron_30segs_bpm_b = pasaron_30segs_bpm = 0
contador_iniciado_60_bpm = contador_iniciado_60_spo = contador_iniciado_60_bpm_b = 0
contador_iniciado_30_bpm = contador_iniciado_30_spo = contador_iniciado_30_bpm_b = 0
tomar_control = alarmas_off_spo = alarmas_off_bpm = alarmas_off_bpm_b = 0
            
t30spo = Timer(0)
t60spo = Timer(0)
t30bpm = Timer(0)
t60bpm = Timer(0)
t30bpm_b = Timer(0)
t60bpm_b = Timer(0)

def contador(cual):
    global alarmas_off_bpm, alarmas_off_bpm_b
    global alarmas_off_spo


    if cual == "30spo":
        global pasaron_30segs_spo
        pasaron_30segs_spo = 1
        alarmas_off_spo = 0
    elif cual == "60spo":
        global contador_iniciado_60_spo
        contador_iniciado_60_spo = 0
        alarmas_off_spo = 0


    elif cual == "30bpm":
        global pasaron_30segs_bpm
        pasaron_30segs_bpm = 1
        alarmas_off_bpm = 0
    elif cual == "60bpm":
        global contador_iniciado_60_bpm
        contador_iniciado_60_bpm = 1
        alarmas_off_bpm = 0


    elif cual == "30bpm_b":
        global pasaron_30segs_bpm_b
        pasaron_30segs_bpm_b = 1
        alarmas_off_bpm_b = 0
    elif cual == "60bpm_b":
        global contador_iniciado_60_bpm_b
        contador_iniciado_60_bpm_b = 0
        alarmas_off_bpm_b = 0



def activar_SAE():
    global codigo
    global pasaron_30segs_spo, pasaron_30segs_bpm_b, pasaron_30segs_bpm
    global contador_iniciado_60_bpm, contador_iniciado_60_spo, contador_iniciado_60_bpm_b
    global contador_iniciado_30_bpm, contador_iniciado_30_spo, contador_iniciado_30_bpm_b
    global tomar_control, alarmas_off_spo, alarmas_off_bpm, alarmas_off_bpm_b
    
    #------------------------------------------
    
    if pin_reaccion is not pin_boton_reaccion:
        pin_boton_reaccion = 1
        


    #protocolo hipoxia
    if codigo[6]==1 and codigo[7]==1:        
        if alarmas_off_spo == 0:
            pin_luz_alarma.value(1)
            #alarma sonora tmb


            if pin_boton_reaccion == 1:
                alarmas_off_spo = 1
                tomar_control = 0
                if contador_iniciado_60_spo != 1:
                    t60spo.init(mode=Timer.ONE_SHOT, period=60000, callback=contador, args="60spo")
                    contador_iniciado_60_spo = 1


            elif contador_iniciado_30_spo != 1:
                contador_iniciado_30_spo = 1
                t30spo.init(mode=Timer.ONE_SHOT, period=30000, callback=contador, args="30spo")

            elif pasaron_30segs_spo == 1:
                contador_iniciado_30_spo = 0
                if pin_boton_reaccion != 1:
                    tomar_control = 1


        elif alarmas_off_spo == 1:
            pin_luz_alarma.value(0)
            pass

    if codigo[6]==1 or codigo[7]==1:
        print("1 piloto tiene hipoxia")
        pin_luz_roja.value(1)
    elif codigo[6]==0 and codigo[7]==0:
        print("ningun piloto tiene hipoxia")
        pin_luz_amarilla.value(0)

    #------------------------------------------
    
    
    #protocolo pulsaciones altas
    if codigo[0]==1 and codigo[1]==1:        
        if alarmas_off_bpm == 0:
            pin_luz_alarma.value(1)
            #alarma sonora tmb


            if pin_boton_reaccion == 1:
                alarmas_off_bpm = 1
                tomar_control = 0
                if contador_iniciado_60_bpm != 1:
                    t60bpm.init(mode=Timer.ONE_SHOT, period=6000, callback=contador, args="60bpm")
                    contador_iniciado_60_bpm = 1


            elif contador_iniciado_30_bpm != 1:
                contador_iniciado_30_bpm = 1
                t30bpm.init(mode=Timer.ONE_SHOT, period=3000, callback=contador, args="30bpm")
            
            elif pasaron_30segs_bpm == 1:
                contador_iniciado_30_bpm = 0
                if pin_boton_reaccion != 0:
                    tomar_control = 1


        elif alarmas_off_bpm == 1:
            pin_luz_alarma.value(0)
            pass


    elif codigo[0]==1 or codigo[1]==1:
        print("pulsaciones altas 1 piloto")
        pin_luz_amarilla.value(1)
    elif codigo[0]==0 and codigo[1]==0: #pulsaciones altas
        print("ninguno de los 2 pilotos tine pulsaciones altas")
        pin_luz_amarilla.value(0)

    #------------------------------------------
    
    
    #protocolo pulsaciones bajas
    if codigo[2]==1 and codigo[3]==1:                   #si ambos tienen    
        if alarmas_off_bpm_b != 1:                      #si las alarmas no estan desactivadas
            pin_luz_alarma.value(1)                     #PRENDE luz de alarma
            #alarma sonora tmb

            if pin_boton_reaccion == 1:                 #si el boton esta presionado
                alarmas_off_bpm_b = 1                   #DESACTIVA las alarmas
                tomar_control = 0                       #no permite que tomen el control
                if contador_iniciado_60_bpm_b != 1:     #si no esta iniciado el contador 60s
                    t60bpm_b.init(mode=Timer.ONE_SHOT, period=6000, callback=contador, args="60bpm_b")
                                                        #INICIA temporizador, luego apagara la variable del contador 60s
                    contador_iniciado_60_bpm_b = 1      #PRENDE variable del contador 60s

            elif contador_iniciado_30_bpm_b != 1:       #sino, si no esta iniciado contador de 30s          
                t30bpm_b.init(mode=Timer.ONE_SHOT, period=3000, callback=contador, args="30bpm_b")
                                                        #INICIAtemporizador, luego apagara la variable del contador 30s
                contador_iniciado_30_bpm_b = 1          #PRENDE variable del contador 30s

            elif pasaron_30segs_bpm_b == 1:             #sino, si pasaron 30s
                contador_iniciado_30_bpm_b = 0          #APAGA variable del contador iniciado 30s, porque ya paso
                if pin_boton_reaccion != 1:             #si el boton de reaccion no esta presionado
                    tomar_control = 1                   #deja que tomen el control

        elif alarmas_off_bpm_b == 1:                    #sino, si estan apagadas las alarmas
            pin_luz_alarma.value(0)                     #apaga luz alarma
            pass

    elif codigo[2]==1 or codigo[3]==1:                  #sino son ambos, si alguno tiene
        print("pulsaciones bajas 1 piloto")
        pin_luz_amarilla.value(1)                       #prende luz
    elif codigo[2]==0 and codigo[3]==0:                 #si ninguno tiene
        print("ninguno de los 2 pilotos tine pulsaciones bajas")
        pin_luz_amarilla.value(0)                       #prende luz
    
    
    #------------------------------------------

    if dormido1 == 1:
        pin_luz_dormido.value(1)
        print("el piloto esta dormido")
    else:
        pin_luz_dormido.value(0)
        print("el piloto esta despierto")
    






    
def evaluar_info(message):
    global bpm_bajos1, bpm_altos1, spo_bajos1, dormido1, temp_baja1, temp_alta1

    data1 = json.loads(message.decode('utf-8'))
    bpm = data1['value1']
    spo = data1['value2']
    temp = data1['value3']
    print("bpm={:02} spo= {:02}% Temp {:02}°C".format(bpm, spo, temp))  #borrar
    


    #Listas de pulsaciones y oxigeno
    listabpm.append(bpm)
    listabpm = listabpm[-48:]
    listaspo.append(spo)
    listaspo = listaspo[-48:] #12 valores cada uno cada 5 segs son 60 segs en total
    
    #dormido
    
     
    #suma de primeros 7 digitos de la lista
    bpm_prom_inicial = sum(listabpm[0:7])
    #suma de los ultimos 8 digitos de la lista
    bpm_prom_actual = sum(listabpm[:-8:-1])
    #diferencia entre ambos
    bpm_dif = bpm_prom_actual - bpm_prom_inicial
    

    spo_prom_inicial = sum(listabpm[0:7])
    spo_prom_actual = sum(listabpm[:-8:-1])
    spo_dif = spo_prom_actual - spo_prom_inicial

    if spo_dif >= 3 and spo_dif <= 8:
        if bpm_dif >= 15 and bpm_dif <= 35:
            print("tiene menos pulsaciones y oxigeno que hace un ratito, suponemos que esta dormido")
            dormido1 = 1
            bpm_dormido = bpm
            spo_dormido = spo
    bpm_dormido_dif = bpm - bpm_dormido
    spo_dormido_dif = spo - spo_dormido

    if bpm_dormido_dif >= 20:
        if spo_dormido_dif >= 3:
            print("esta despierto ahora")
            dormido1 = 0
    #despierto

    #bpms
    if bpm < 60:
        bpm_bajos1 = 1
        bpm_altos1 = 0
    elif bpm > 140:
        bpm_altos1 = 1
        bpm_bajos1 = 0
    else:
        bpm_bajos1 = 0
        bpm_altos1 = 0
    
    #spo
    if spo <= 90:
        spo_bajos1 = 1
    elif spo > 90:
        spo_bajos1 = 0
    
    #segun temperaturas:
    if temp < 5:
        temp_baja1 = 1
        temp_alta1 = 0
    elif temp > 40:
        temp_alta1 = 1
        temp_baja1 = 0
    else:
        temp_baja1 = 0
        temp_alta1 = 0  

#_thread.start_new_thread(recibir_rtdc, (station1,))
#_thread.start_new_thread(enviar_rtdc, (station1,))
_thread.start_new_thread(recibir_band1, (station2,))
#_thread.start_new_thread(recibir_band2, (station3,))
#exchange_data2(station2)
#exchange_data1(station1)
